VivIngInf/kaffettino-rebrewed/Resources/Images/Buongiornissimi/Christmas/auguri-di-natale-immagini-1.png

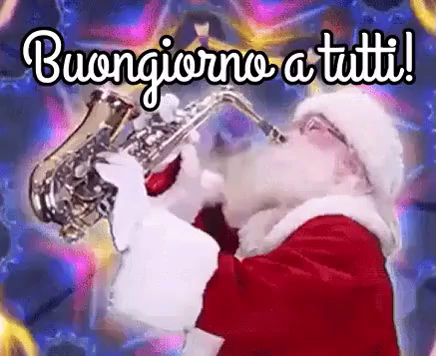
Resources/Images/Buongiornissimi/Christmas/auguri-di-natale-immagini-1.png
