VivIngInf/kaffettino-rebrewed/Resources/Images/Buongiornissimi/Christmas/auguri-di-natale-immagini-11.jpg

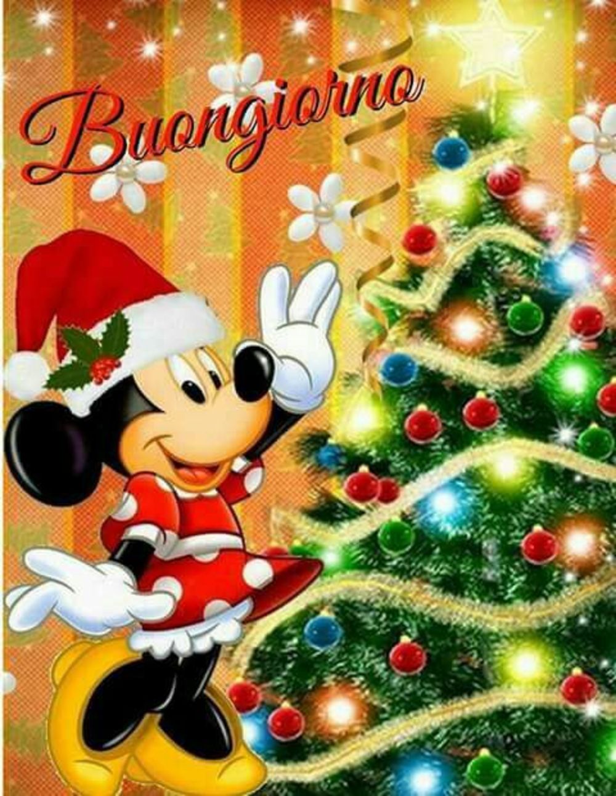
Resources/Images/Buongiornissimi/Christmas/auguri-di-natale-immagini-11.jpg
