VivIngInf/kaffettino-rebrewed/Resources/Images/Buongiornissimi/Christmas/Buongiorno-con-gatto-e-albero-di-Natale.jpg

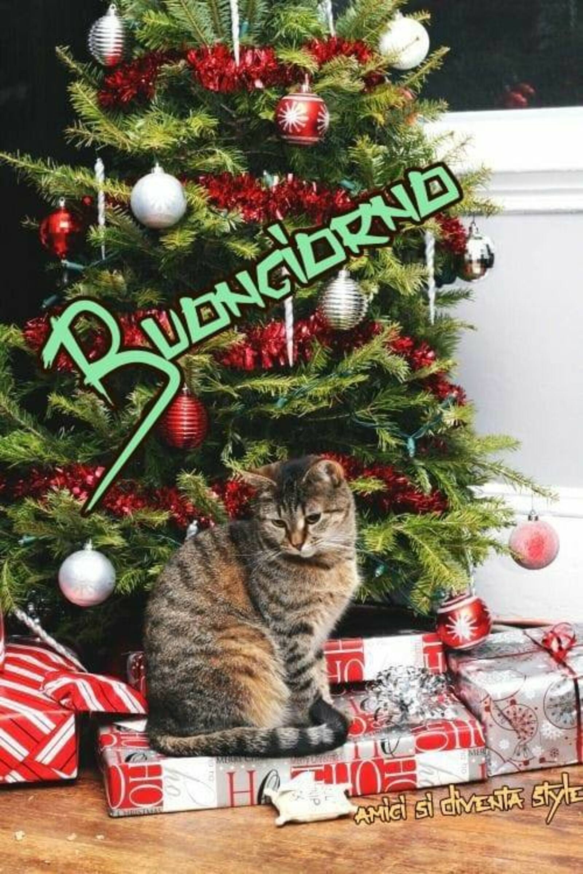
Resources/Images/Buongiornissimi/Christmas/Buongiorno-con-gatto-e-albero-di-Natale.jpg
