VivIngInf/kaffettino-rebrewed/Resources/Images/Buongiornissimi/Christmas/Buongiorno-Natale-1.jpg

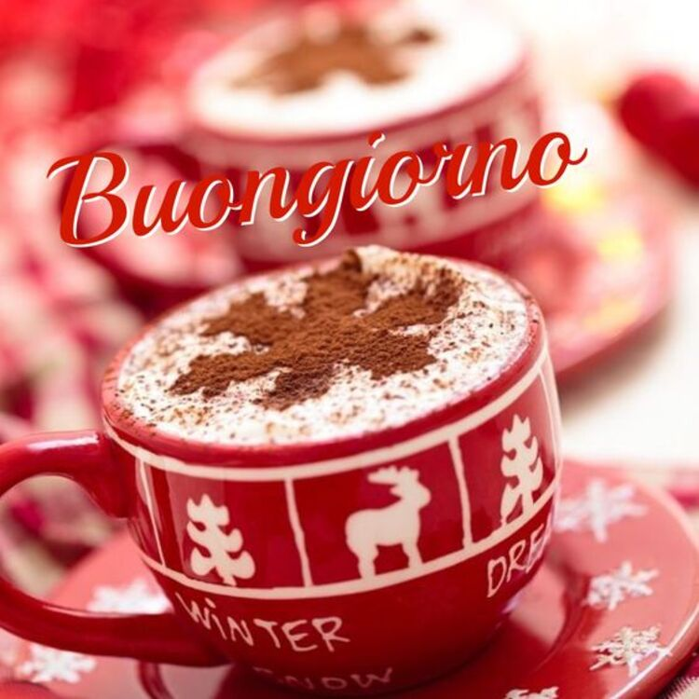
Resources/Images/Buongiornissimi/Christmas/Buongiorno-Natale-1.jpg
