VivIngInf/kaffettino-rebrewed/Resources/Images/Buongiornissimi/Christmas/Buongiorno-natalizio-3-693x1024.jpg

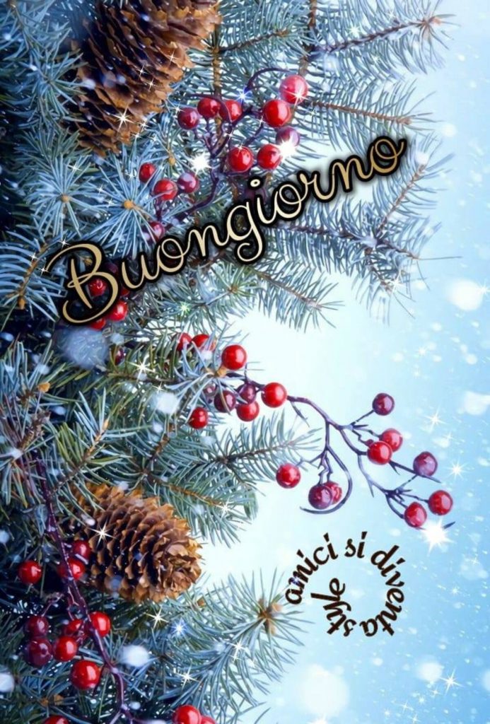
Resources/Images/Buongiornissimi/Christmas/Buongiorno-natalizio-3-693x1024.jpg
