VivIngInf/kaffettino-rebrewed/Resources/Images/Buongiornissimi/Christmas/Buongiorno-natalizio-3.jpg

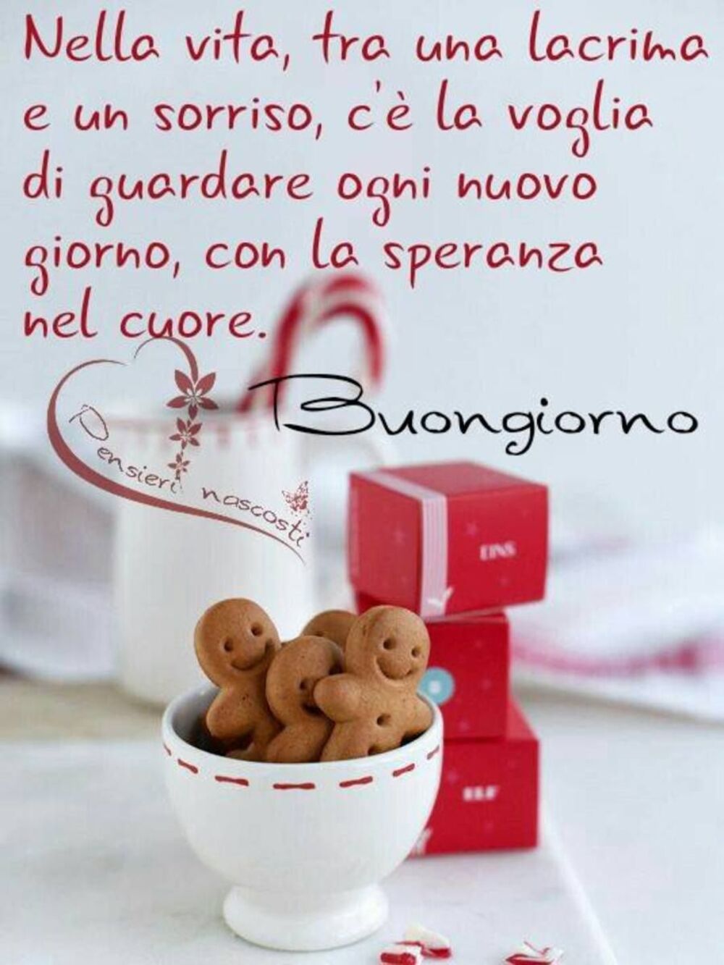
Resources/Images/Buongiornissimi/Christmas/Buongiorno-natalizio-3.jpg
