VivIngInf/kaffettino-rebrewed/Resources/Images/Buongiornissimi/Christmas/Buongiorno-natalizio-8-687x1024.jpg

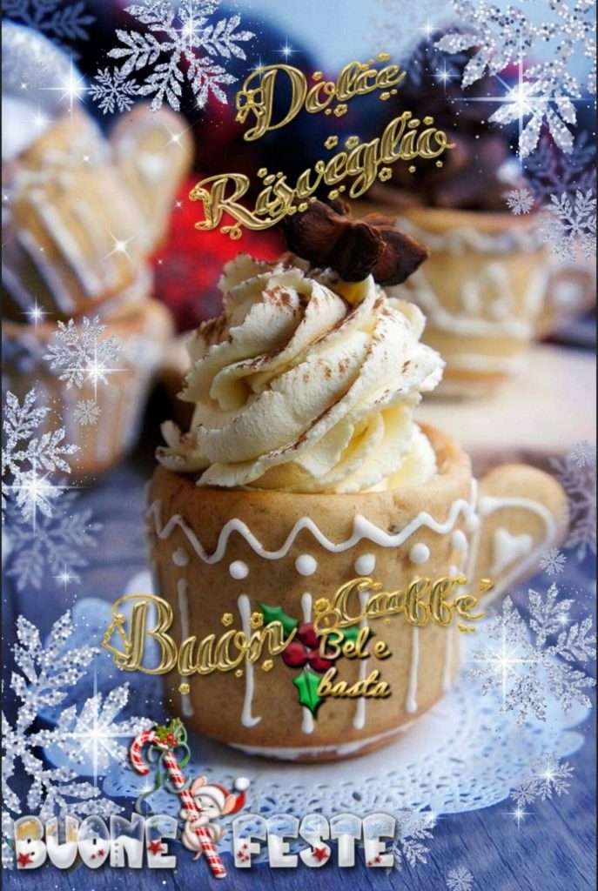
Resources/Images/Buongiornissimi/Christmas/Buongiorno-natalizio-8-687x1024.jpg
