VivIngInf/kaffettino-rebrewed/Resources/Images/Buongiornissimi/Christmas/Buongiorno-natalizio-14-680x1024.jpg

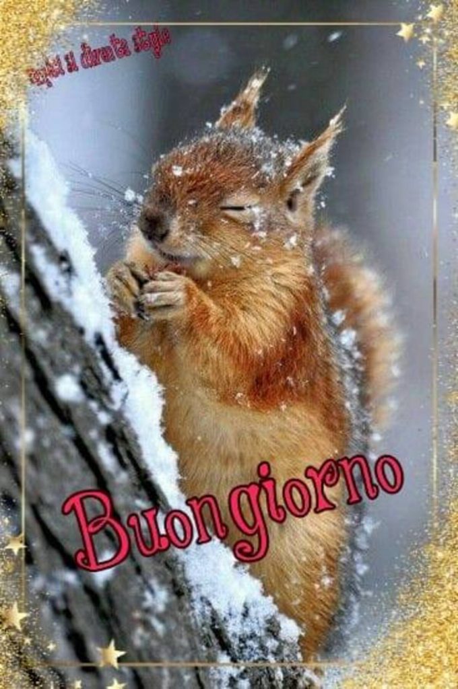
Resources/Images/Buongiornissimi/Christmas/Buongiorno-natalizio-14-680x1024.jpg
