VivIngInf/kaffettino-rebrewed/Resources/Images/Buongiornissimi/Christmas/Buongiorno-natalizio-15-692x1024.jpg

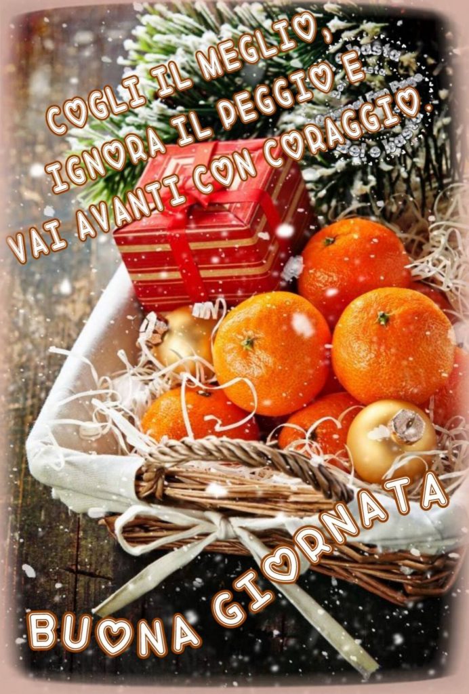
Resources/Images/Buongiornissimi/Christmas/Buongiorno-natalizio-15-692x1024.jpg
