VivIngInf/kaffettino-rebrewed/Resources/Images/Buongiornissimi/Christmas/Buongiorno-natalizio-18-598x1024.jpg

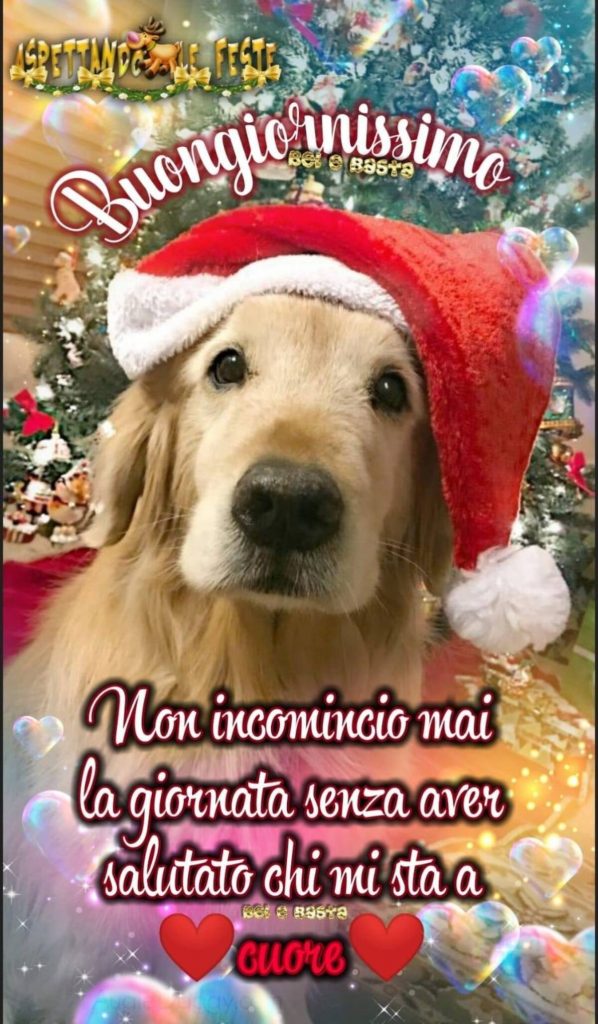
Resources/Images/Buongiornissimi/Christmas/Buongiorno-natalizio-18-598x1024.jpg
