VivIngInf/kaffettino-rebrewed/Resources/Images/Buongiornissimi/Christmas/Buongiorno-natalizio-24-807x1024.jpg

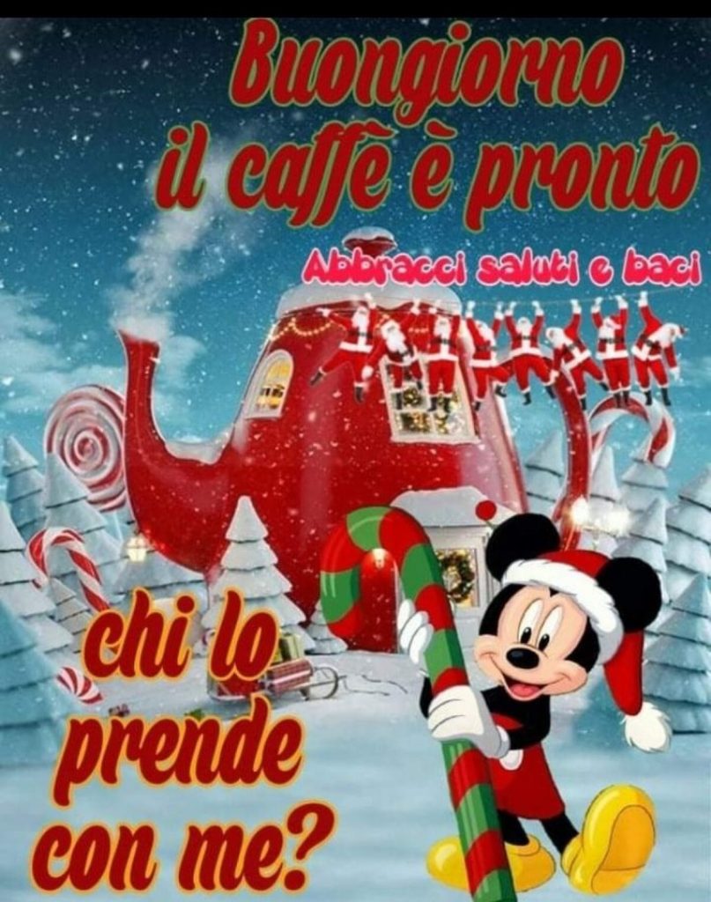
Resources/Images/Buongiornissimi/Christmas/Buongiorno-natalizio-24-807x1024.jpg
