VivIngInf/kaffettino-rebrewed/Resources/Images/Buongiornissimi/Christmas/Buongiorno-natalizio-25-825x1024.jpg

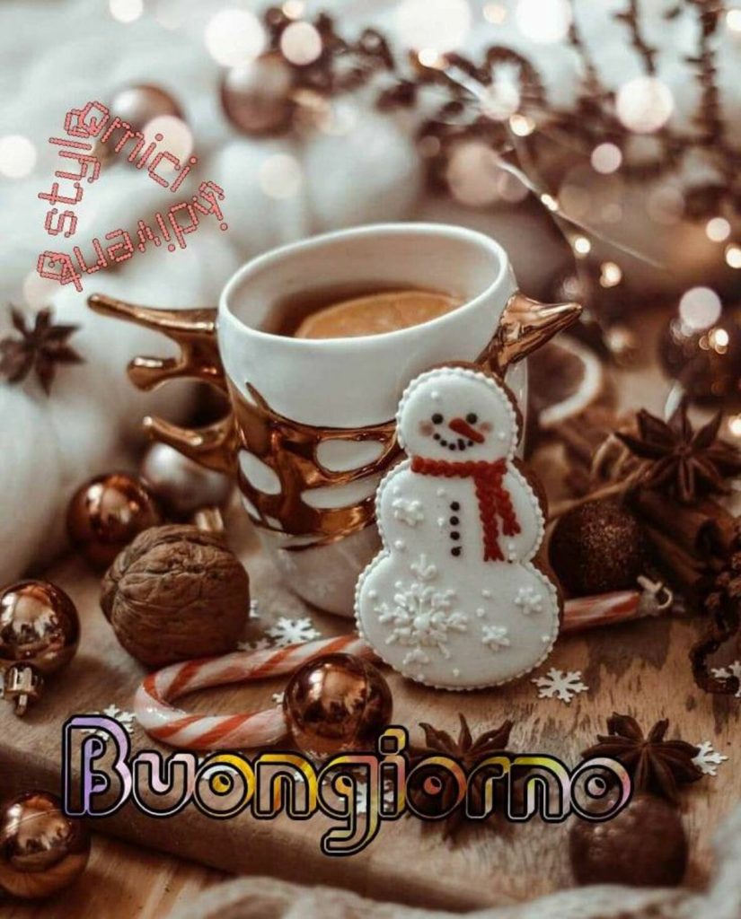
Resources/Images/Buongiornissimi/Christmas/Buongiorno-natalizio-25-825x1024.jpg
