VivIngInf/kaffettino-rebrewed/Resources/Images/Buongiornissimi/Christmas/Buongiorno-natalizio-27-742x1024.jpg

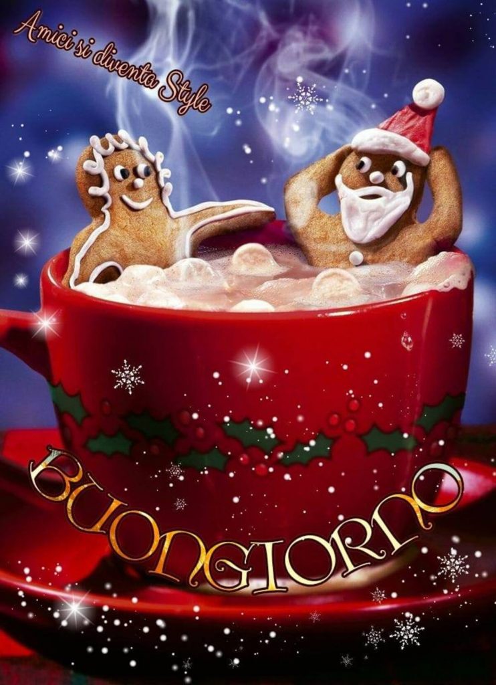
Resources/Images/Buongiornissimi/Christmas/Buongiorno-natalizio-27-742x1024.jpg
