VivIngInf/kaffettino-rebrewed/Resources/Images/Buongiornissimi/Christmas/Buongiorno-natalizio-34-1024x1024.jpg

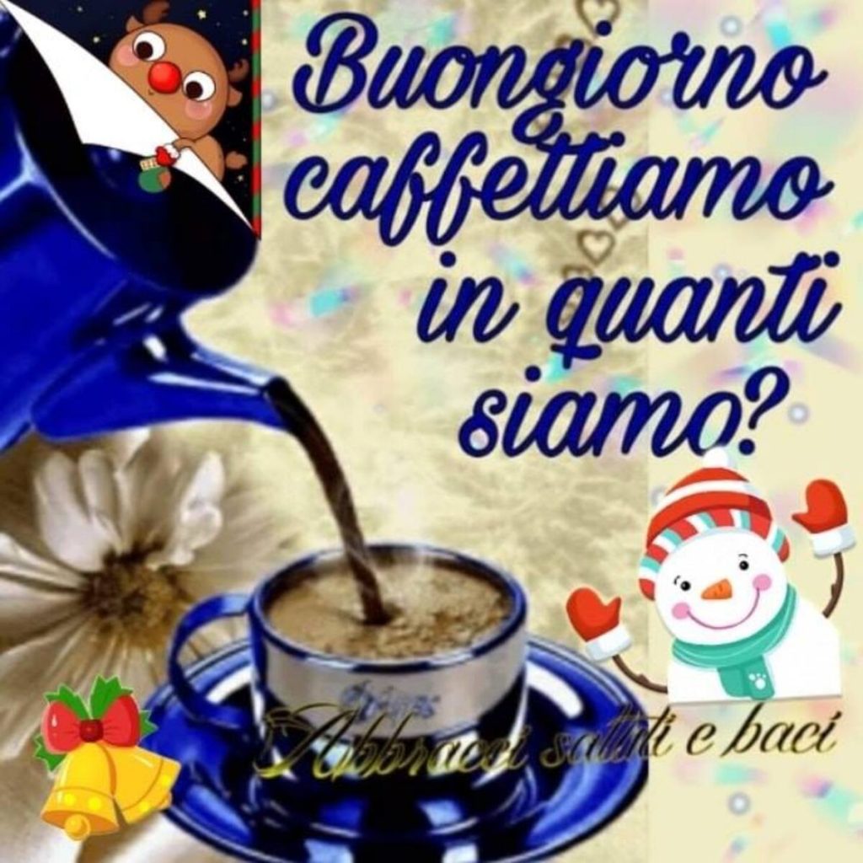
Resources/Images/Buongiornissimi/Christmas/Buongiorno-natalizio-34-1024x1024.jpg
