VivIngInf/kaffettino-rebrewed/Resources/Images/Buongiornissimi/Christmas/Buongiorno-natalizio-37-1024x683.jpg

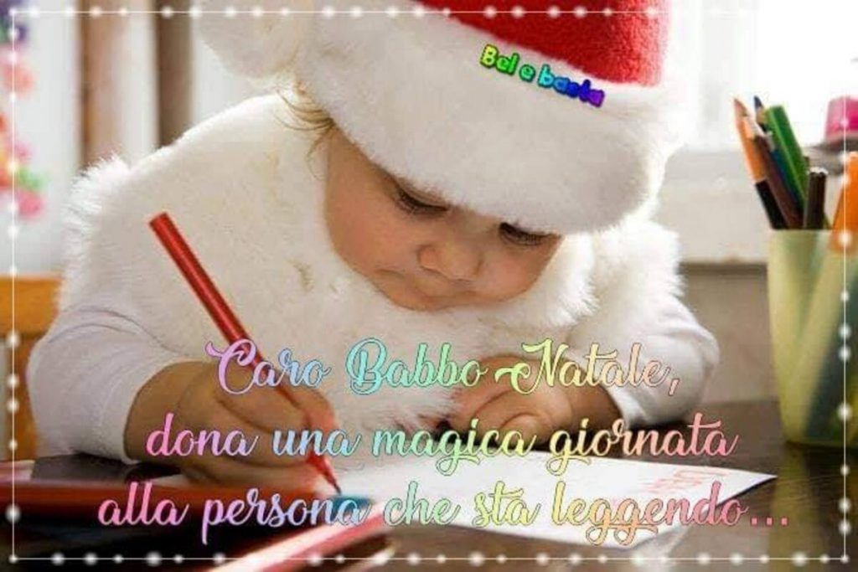
Resources/Images/Buongiornissimi/Christmas/Buongiorno-natalizio-37-1024x683.jpg
