VivIngInf/kaffettino-rebrewed/Resources/Images/Buongiornissimi/Christmas/Buongiorno-natalizio-38-1024x1024.jpg

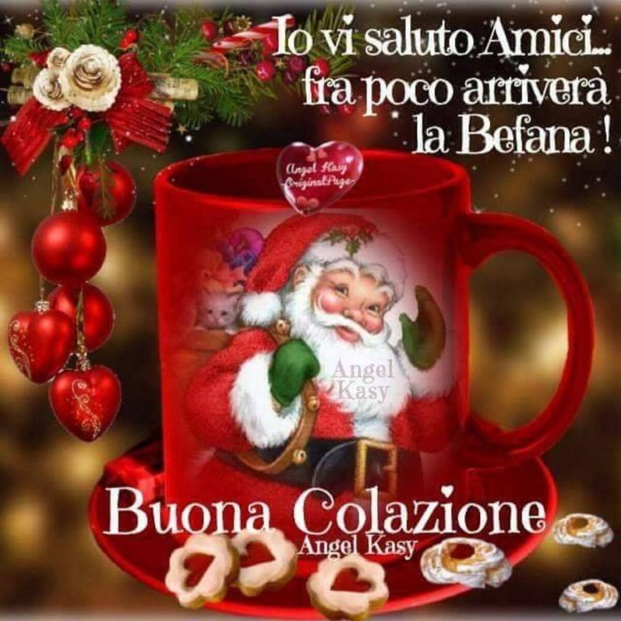
Resources/Images/Buongiornissimi/Christmas/Buongiorno-natalizio-38-1024x1024.jpg
