VivIngInf/kaffettino-rebrewed/Resources/Images/Buongiornissimi/Christmas/Buongiorno-natalizio-43-840x1024.jpg

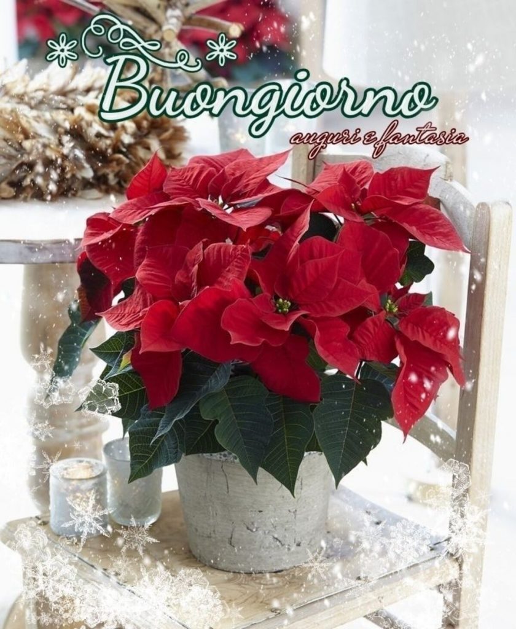
Resources/Images/Buongiornissimi/Christmas/Buongiorno-natalizio-43-840x1024.jpg
