VivIngInf/kaffettino-rebrewed/Resources/Images/Buongiornissimi/Christmas/Buongiorno-natalizio-44-1024x794.jpg

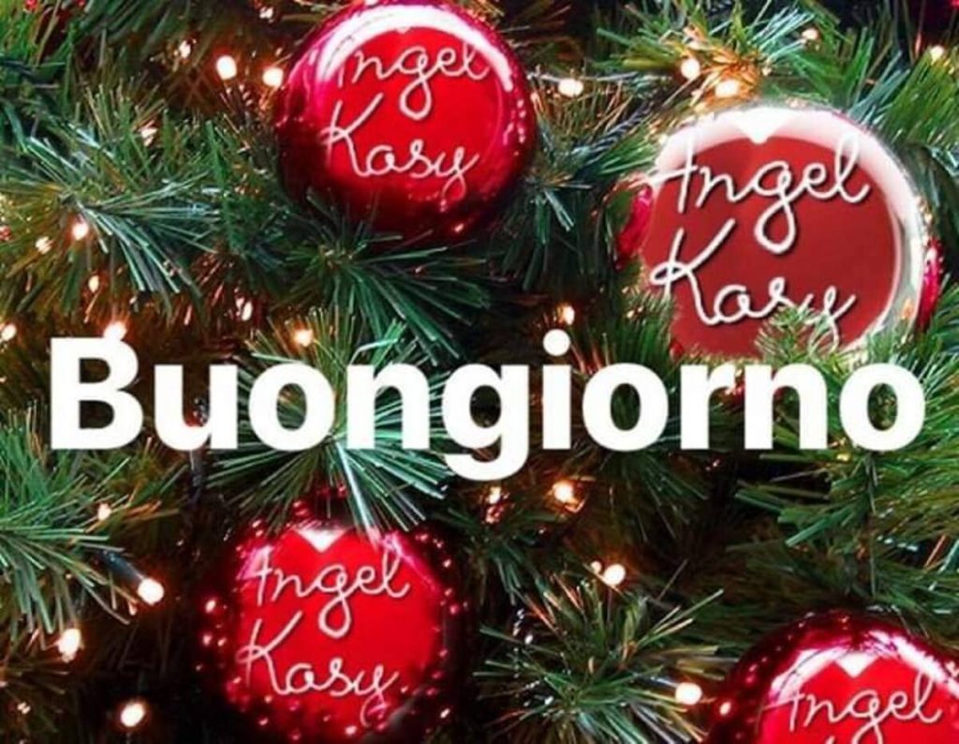
Resources/Images/Buongiornissimi/Christmas/Buongiorno-natalizio-44-1024x794.jpg
