VivIngInf/kaffettino-rebrewed/Resources/Images/Buongiornissimi/Christmas/Buongiorno-natalizio-belle-immagini-1.jpg

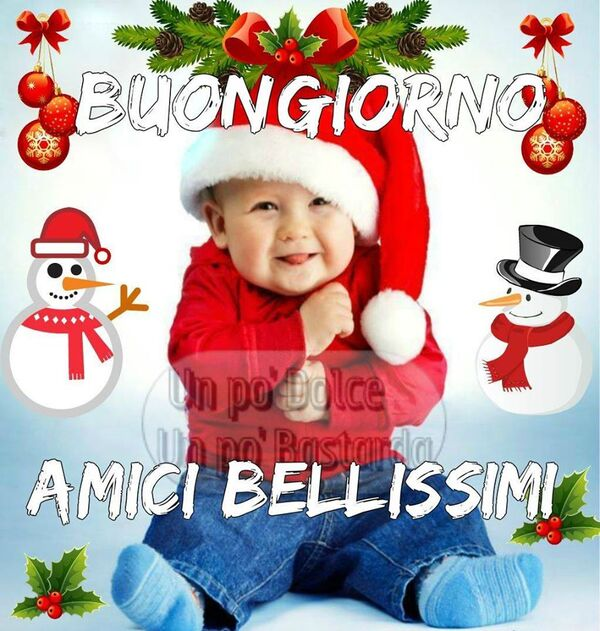
Resources/Images/Buongiornissimi/Christmas/Buongiorno-natalizio-belle-immagini-1.jpg
