VivIngInf/kaffettino-rebrewed/Resources/Images/Buongiornissimi/Christmas/Buongiorno-natalizio-belle-immagini-7.jpg

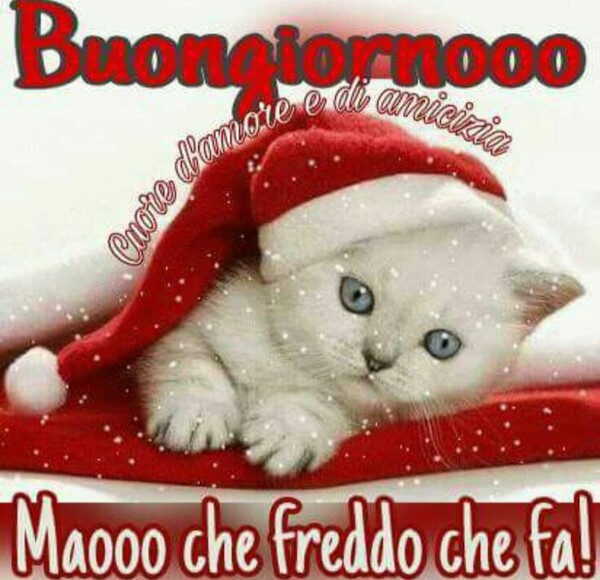
Resources/Images/Buongiornissimi/Christmas/Buongiorno-natalizio-belle-immagini-7.jpg
