VivIngInf/kaffettino-rebrewed/Resources/Images/Buongiornissimi/Christmas/Buongiorno-natalizio-belle-immagini-13.jpg

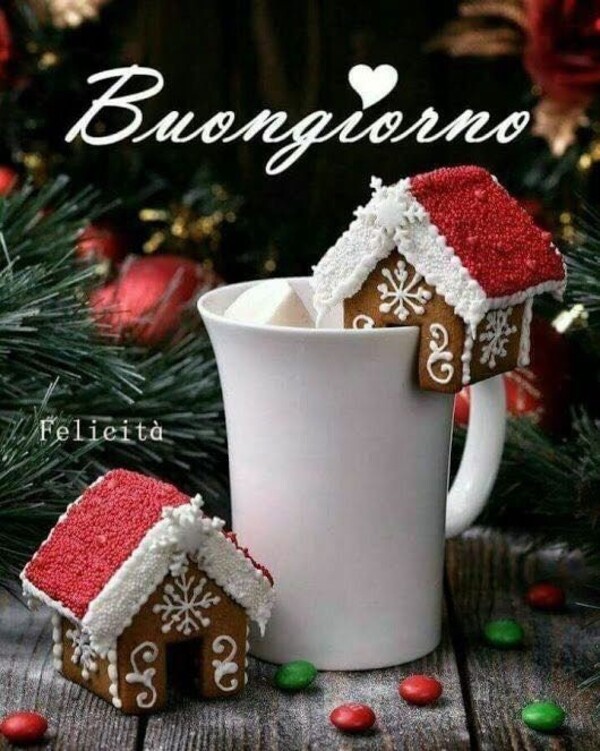
Resources/Images/Buongiornissimi/Christmas/Buongiorno-natalizio-belle-immagini-13.jpg
