VivIngInf/kaffettino-rebrewed/Resources/Images/Buongiornissimi/Christmas/Buongiorno-natalizio-belle-immagini-15.jpg

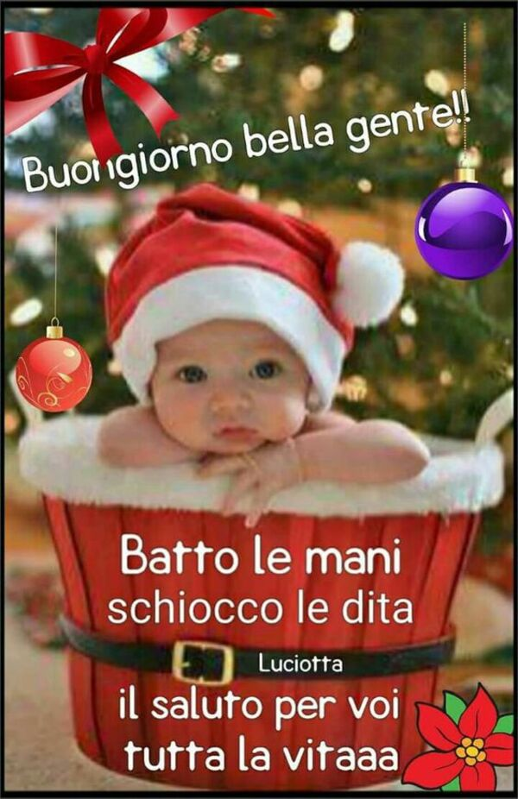
Resources/Images/Buongiornissimi/Christmas/Buongiorno-natalizio-belle-immagini-15.jpg
