VivIngInf/kaffettino-rebrewed/Resources/Images/Buongiornissimi/Christmas/Buongiorno-natalizio-link-nuovi-5.jpg

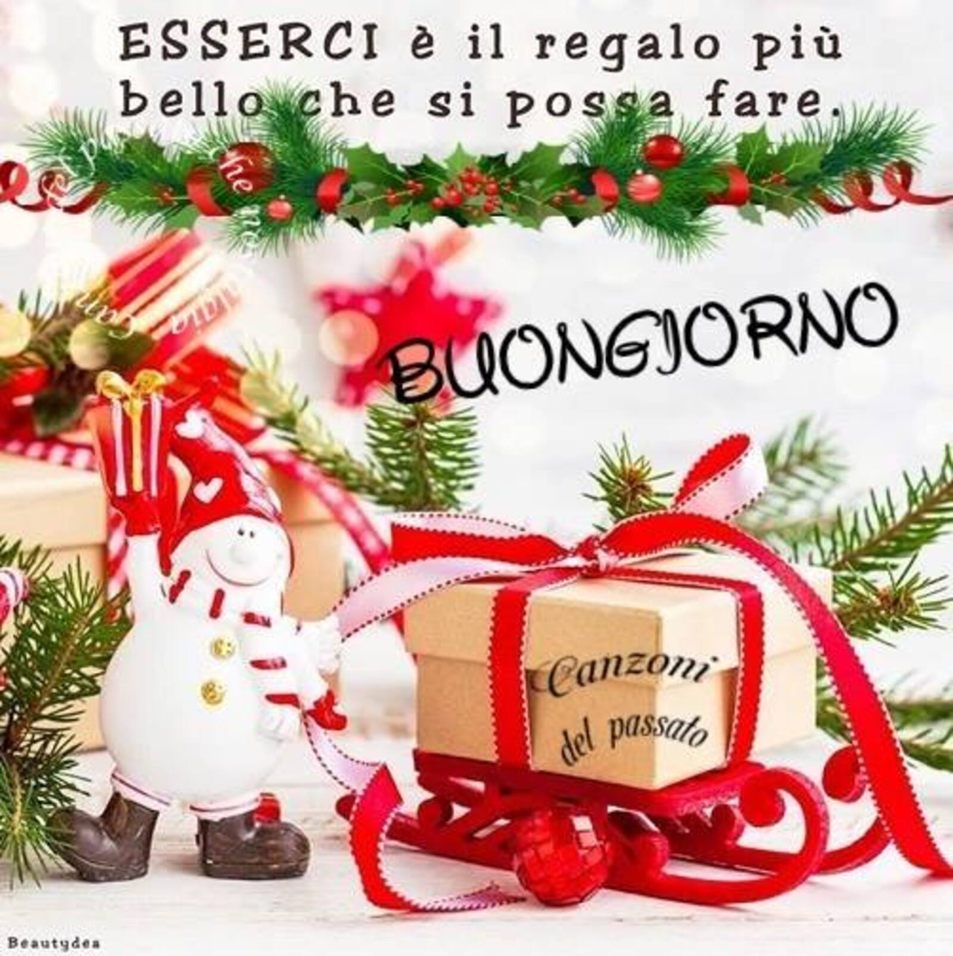
Resources/Images/Buongiornissimi/Christmas/Buongiorno-natalizio-link-nuovi-5.jpg
