VivIngInf/kaffettino-rebrewed/Resources/Images/Buongiornissimi/Christmas/Buongiorno-per-il-Natale-1-860x1024.jpg

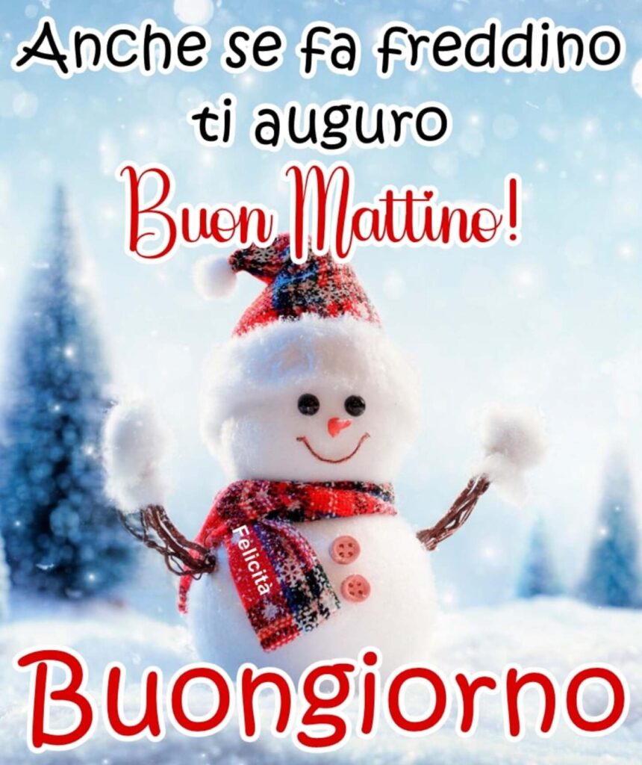
Resources/Images/Buongiornissimi/Christmas/Buongiorno-per-il-Natale-1-860x1024.jpg
