VivIngInf/kaffettino-rebrewed/Resources/Images/Buongiornissimi/Christmas/Buongiorno-per-il-Natale-3-808x1024.jpg

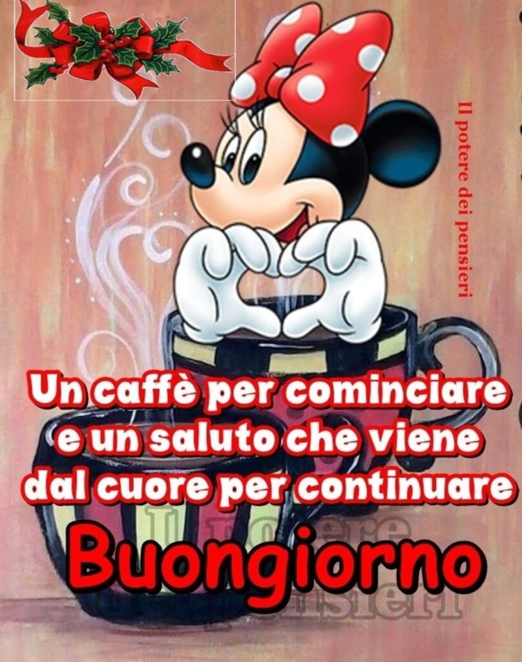
Resources/Images/Buongiornissimi/Christmas/Buongiorno-per-il-Natale-3-808x1024.jpg
