VivIngInf/kaffettino-rebrewed/Resources/Images/Buongiornissimi/Christmas/Buongiorno-per-il-Natale-6-769x1024.jpg

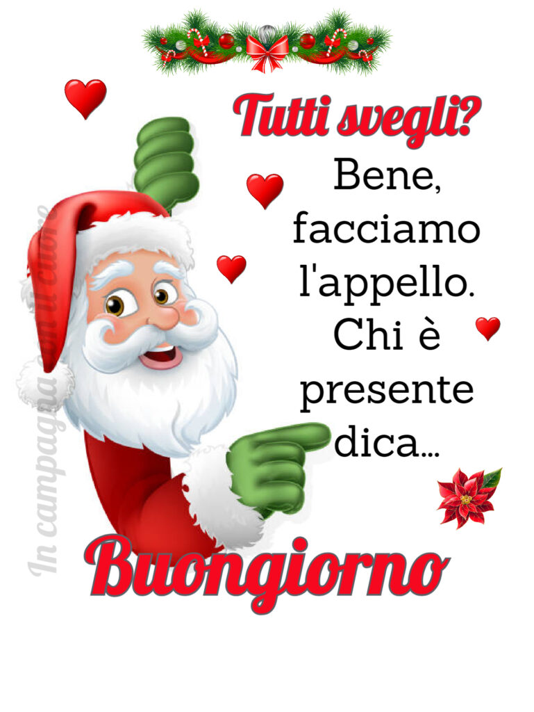
Resources/Images/Buongiornissimi/Christmas/Buongiorno-per-il-Natale-6-769x1024.jpg
