VivIngInf/kaffettino-rebrewed/Resources/Images/Buongiornissimi/Christmas/Buongiorno-per-il-Natale-8-858x1024.jpg

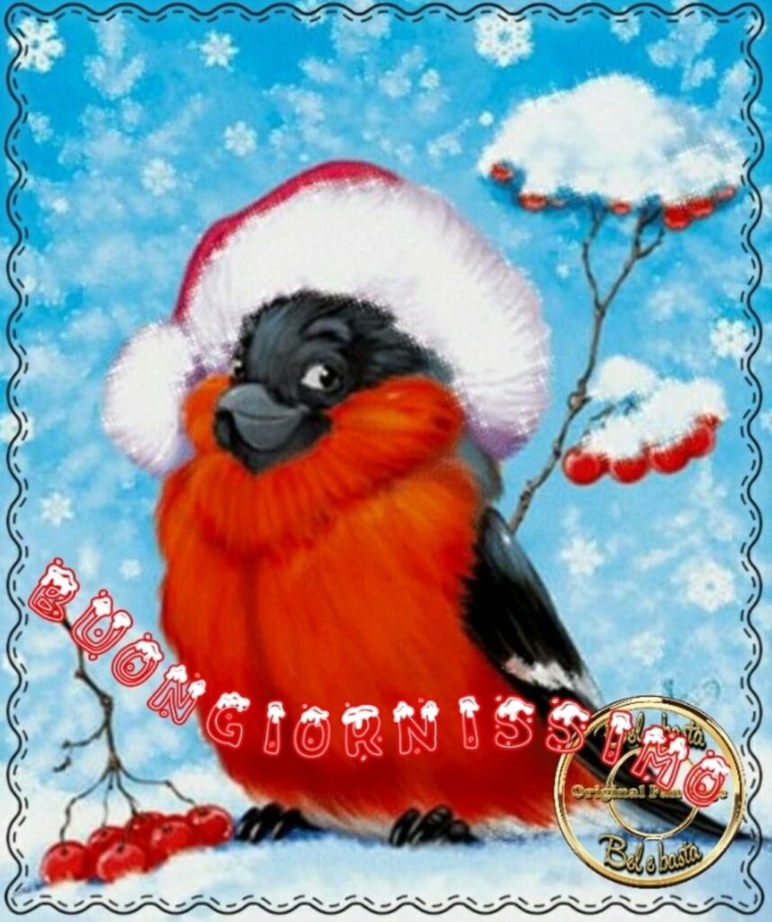
Resources/Images/Buongiornissimi/Christmas/Buongiorno-per-il-Natale-8-858x1024.jpg
