VivIngInf/kaffettino-rebrewed/Resources/Images/Buongiornissimi/Christmas/Buongiorno-per-il-Natale-11-773x1024.jpg

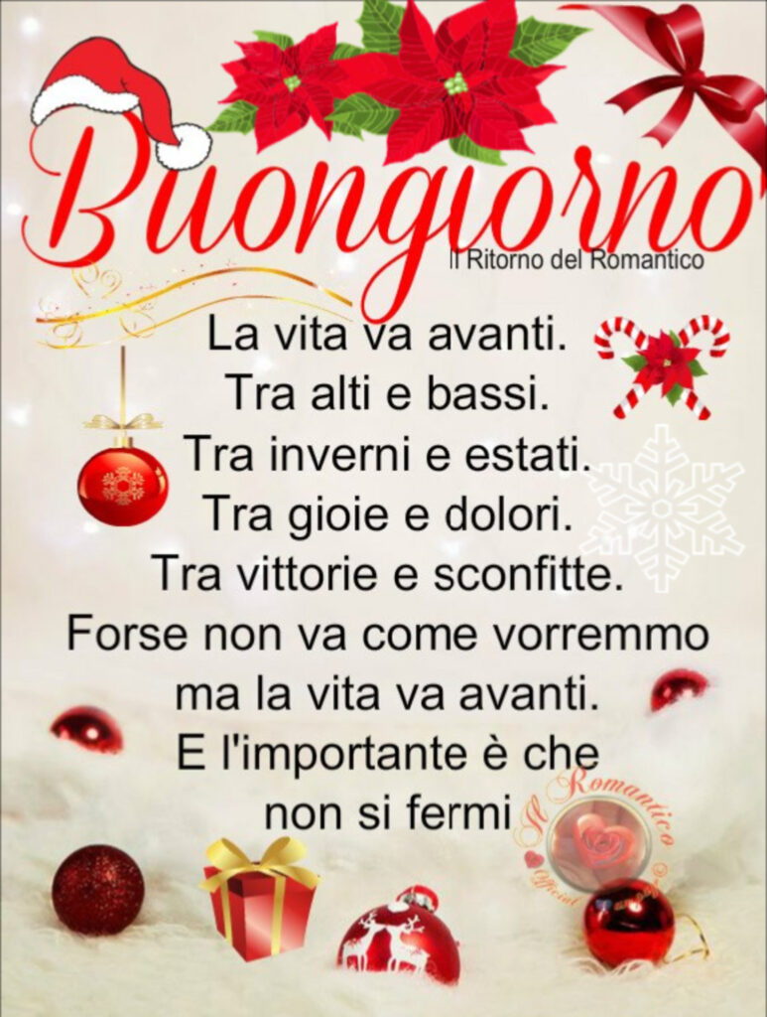
Resources/Images/Buongiornissimi/Christmas/Buongiorno-per-il-Natale-11-773x1024.jpg
