VivIngInf/kaffettino-rebrewed/Resources/Images/Buongiornissimi/Christmas/d4e82814d92ebad9347e3b47b032a1e5.jpg

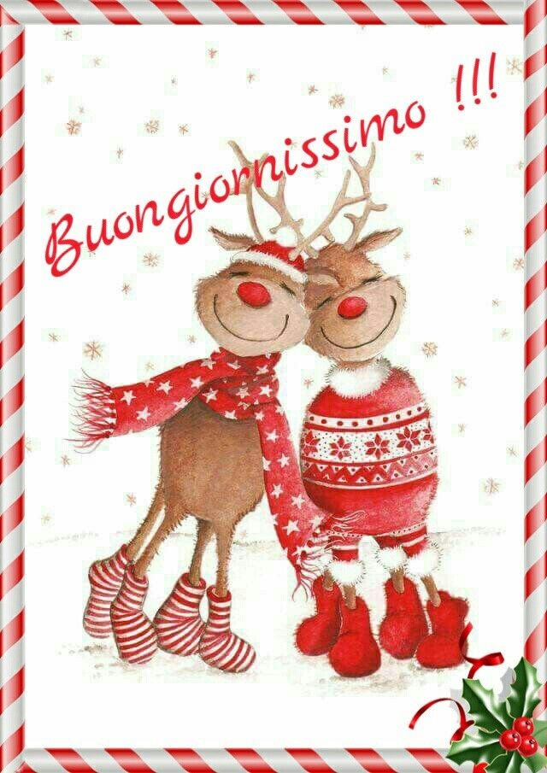
Resources/Images/Buongiornissimi/Christmas/d4e82814d92ebad9347e3b47b032a1e5.jpg
