VivIngInf/kaffettino-rebrewed/Resources/Images/Buongiornissimi/Christmas/d062dc0604afb666024305d2ea12398f.jpg

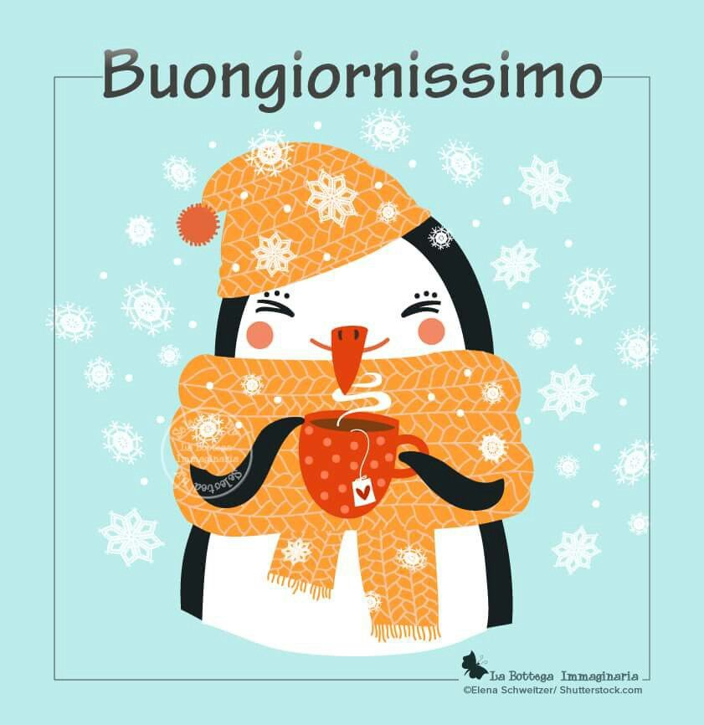
Resources/Images/Buongiornissimi/Christmas/d062dc0604afb666024305d2ea12398f.jpg
