VivIngInf/kaffettino-rebrewed/Resources/Images/Buongiornissimi/Christmas/IMG-20181119-WA0004.jpg

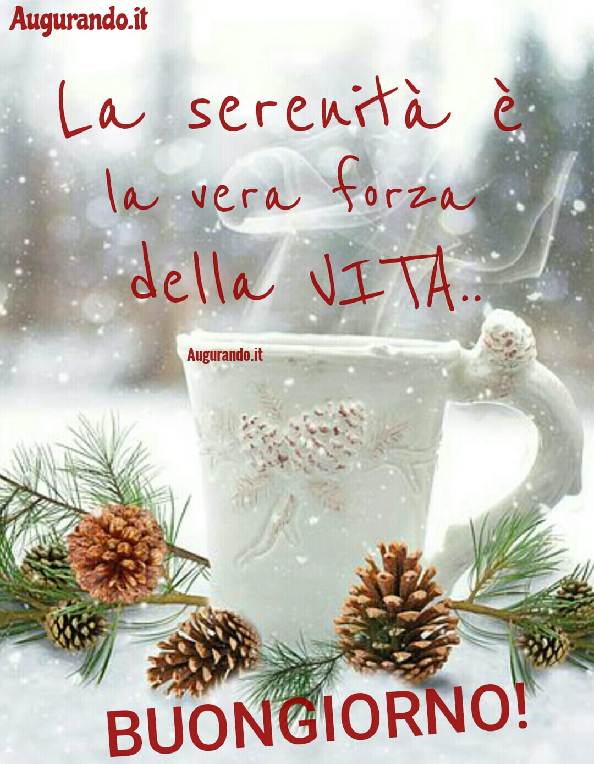
Resources/Images/Buongiornissimi/Christmas/IMG-20181119-WA0004.jpg
