VivIngInf/kaffettino-rebrewed/Resources/Images/Buongiornissimi/Debt/Bed.jpg

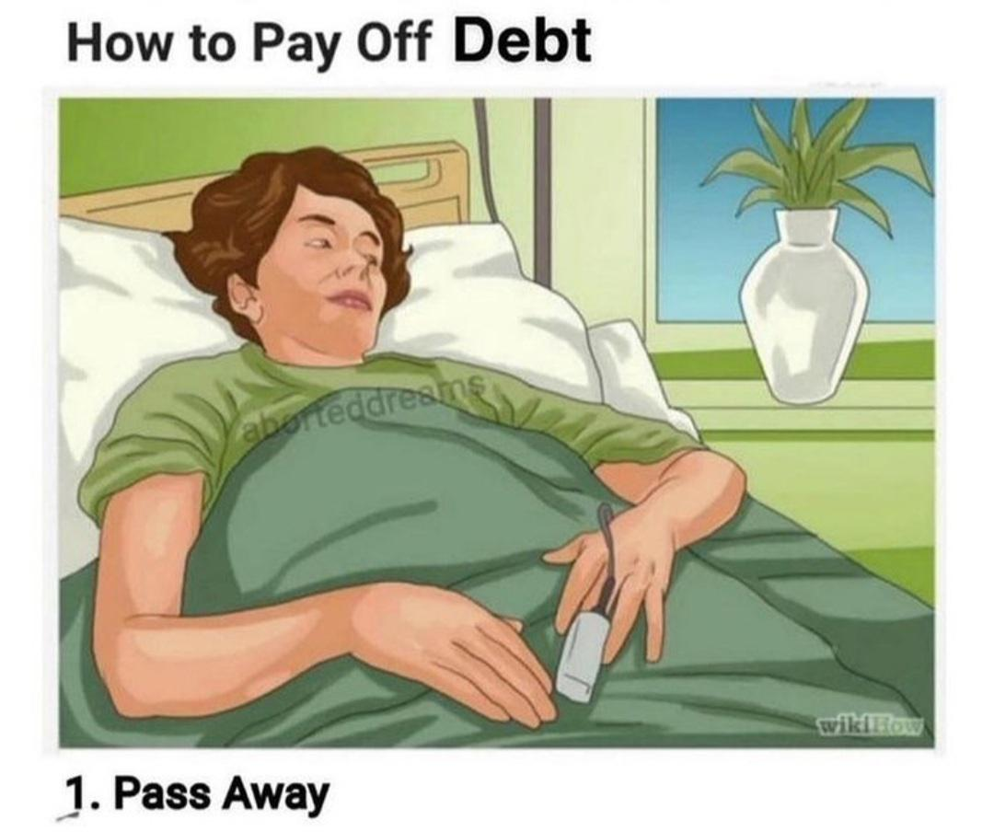
Resources/Images/Buongiornissimi/Debt/Bed.jpg
