VivIngInf/kaffettino-rebrewed/Resources/Images/Buongiornissimi/Debt/Crying.jpg

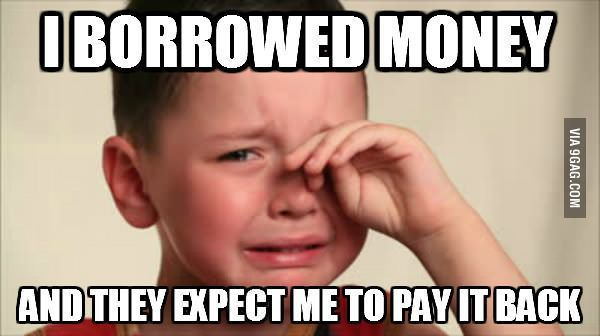
Resources/Images/Buongiornissimi/Debt/Crying.jpg
