VivIngInf/kaffettino-rebrewed/Resources/Images/Buongiornissimi/Debt/Dog.webp

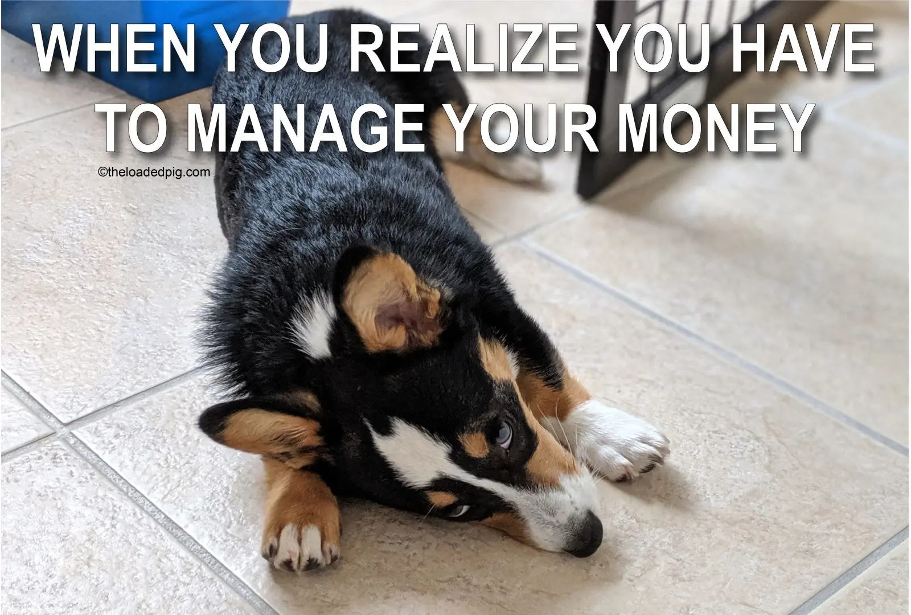
Resources/Images/Buongiornissimi/Debt/Dog.webp
