VivIngInf/kaffettino-rebrewed/Resources/Images/Buongiornissimi/Debt/Excursion.jpg

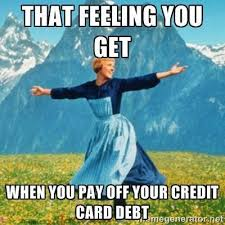
Resources/Images/Buongiornissimi/Debt/Excursion.jpg
