VivIngInf/kaffettino-rebrewed/Resources/Images/Buongiornissimi/Debt/Jump.jpg

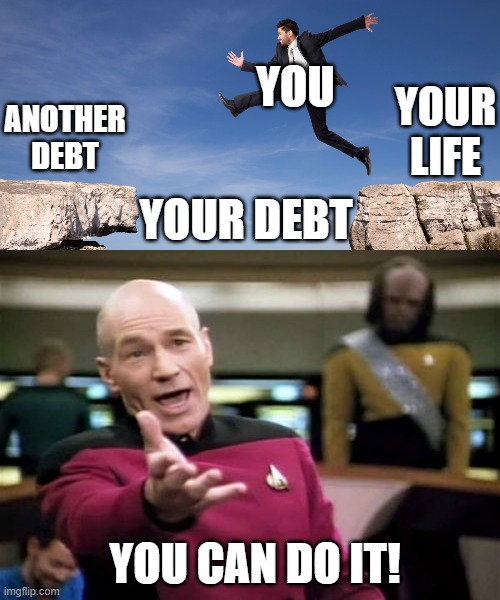
Resources/Images/Buongiornissimi/Debt/Jump.jpg
