VivIngInf/kaffettino-rebrewed/Resources/Images/Buongiornissimi/Debt/Peter.webp

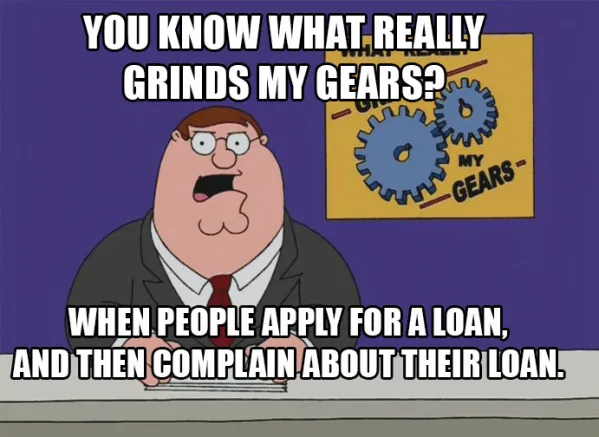
Resources/Images/Buongiornissimi/Debt/Peter.webp
