VivIngInf/kaffettino-rebrewed/Resources/Images/Buongiornissimi/Debt/Swimming.jpg

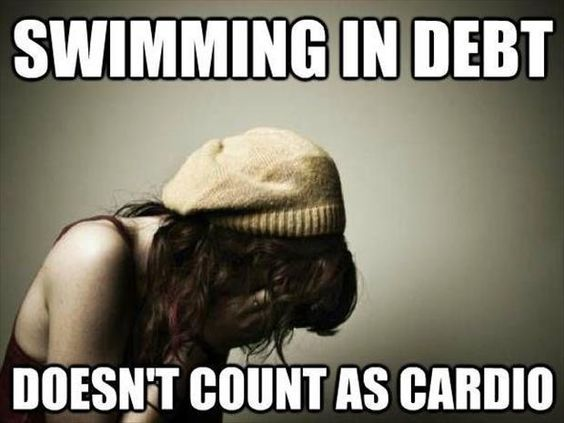
Resources/Images/Buongiornissimi/Debt/Swimming.jpg
