VivIngInf/kaffettino-rebrewed/Resources/Images/Buongiornissimi/Debt/Wallet.jpg

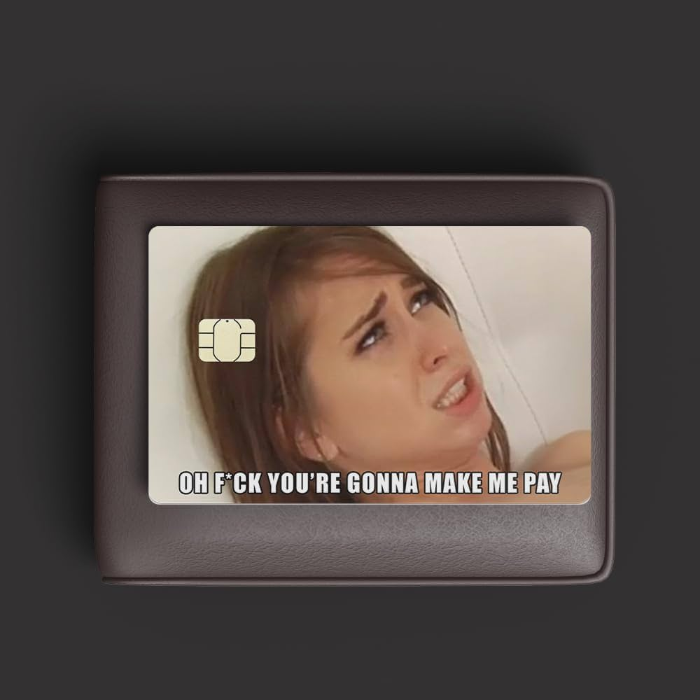
Resources/Images/Buongiornissimi/Debt/Wallet.jpg
