VivIngInf/kaffettino-rebrewed/Resources/Images/Buongiornissimi/Easter/8abb78aae9db7de9b1623d1325ee7758.jpg

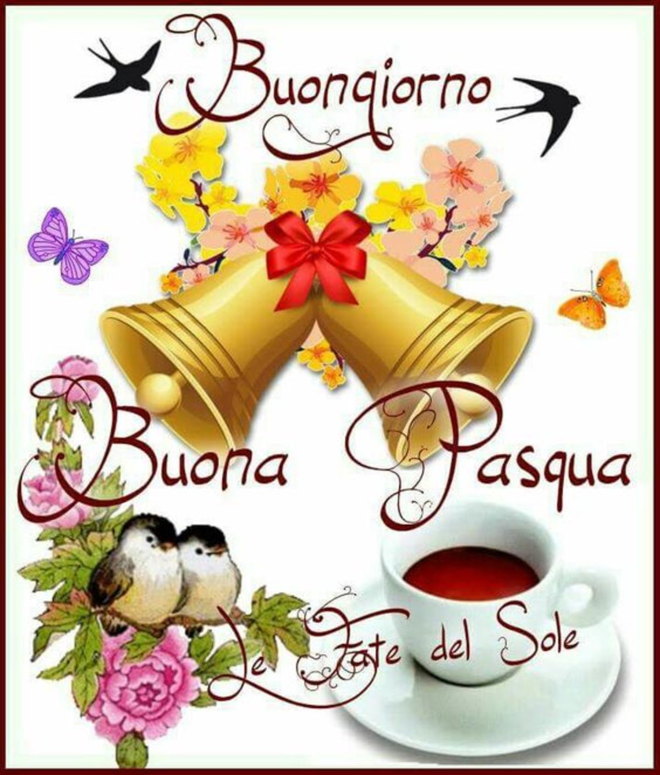
Resources/Images/Buongiornissimi/Easter/8abb78aae9db7de9b1623d1325ee7758.jpg
