VivIngInf/kaffettino-rebrewed/Resources/Images/Buongiornissimi/Easter/Buona-Pasqua-buongiorno-immagini-8727.jpg

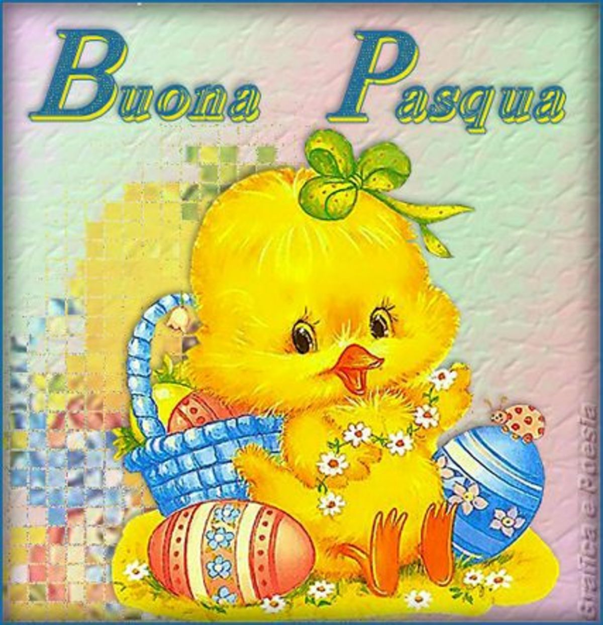
Resources/Images/Buongiornissimi/Easter/Buona-Pasqua-buongiorno-immagini-8727.jpg
