VivIngInf/kaffettino-rebrewed/Resources/Images/Buongiornissimi/Easter/buona-pasqua-con-uova-e-coniglietto.jpg

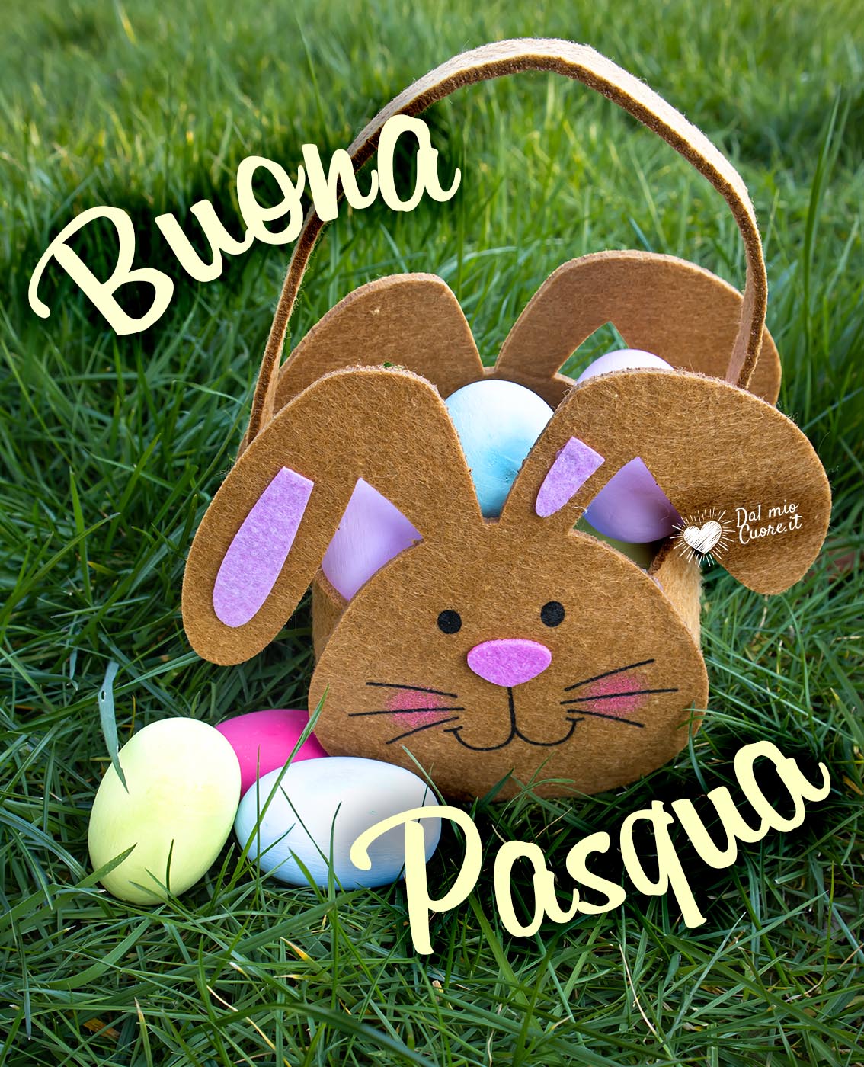
Resources/Images/Buongiornissimi/Easter/buona-pasqua-con-uova-e-coniglietto.jpg
