VivIngInf/kaffettino-rebrewed/Resources/Images/Buongiornissimi/Easter/campane-pasqua.jpg

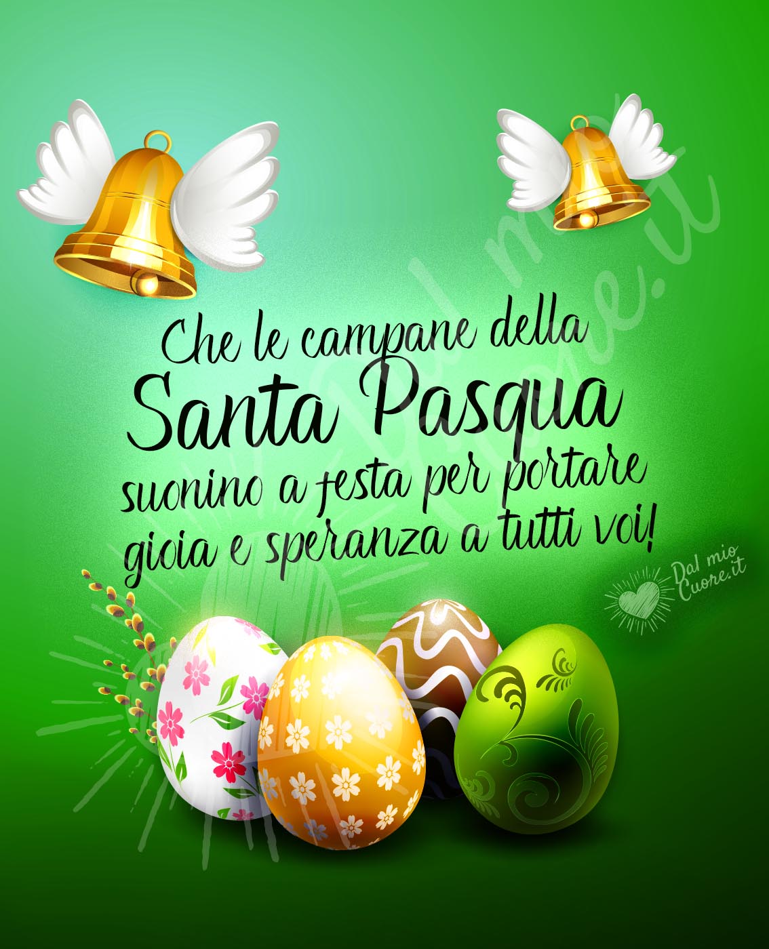
Resources/Images/Buongiornissimi/Easter/campane-pasqua.jpg
