VivIngInf/kaffettino-rebrewed/Resources/Images/Buongiornissimi/Easter/Immagine WhatsApp 2024-03-31 ore 10.33.46_9a69b27c.jpg

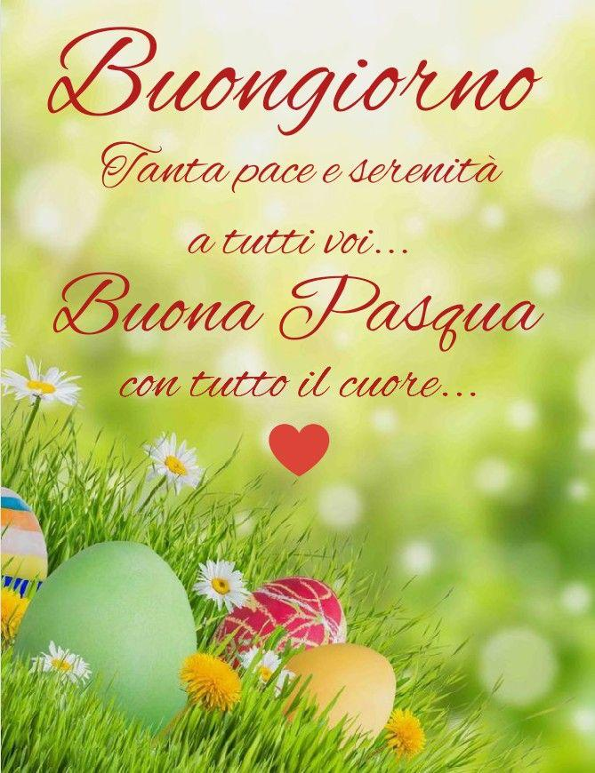
Resources/Images/Buongiornissimi/Easter/Immagine WhatsApp 2024-03-31 ore 10.33.46_9a69b27c.jpg
