VivIngInf/kaffettino-rebrewed/Resources/Images/Buongiornissimi/Easter/Immagine WhatsApp 2024-03-31 ore 10.36.33_8d8238a4.jpg

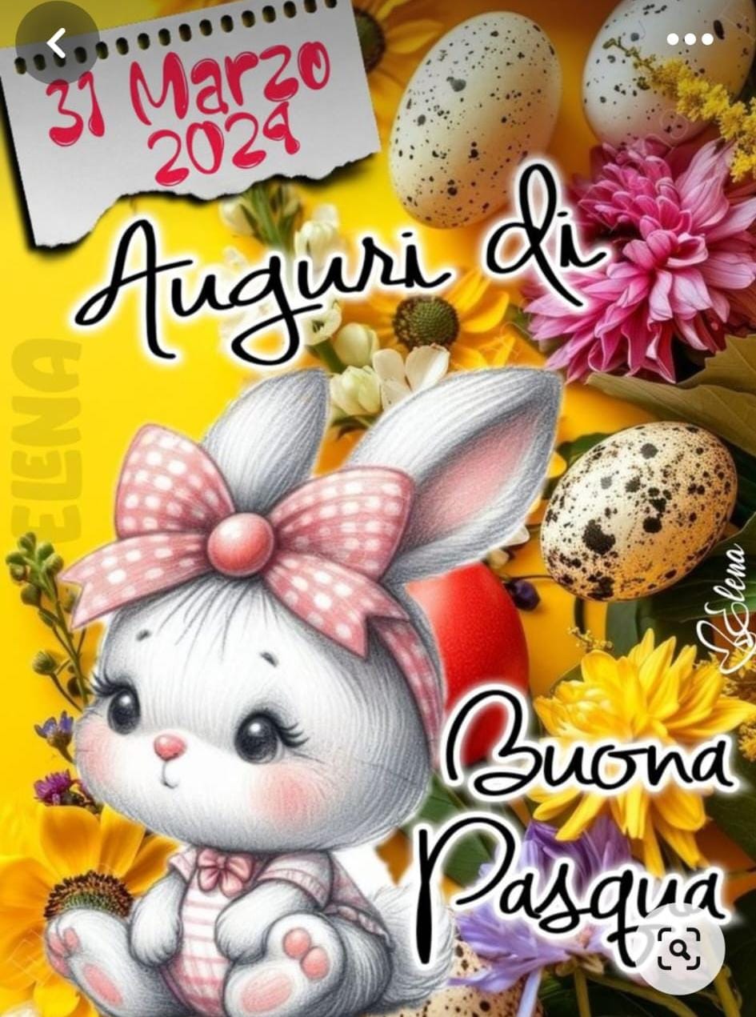
Resources/Images/Buongiornissimi/Easter/Immagine WhatsApp 2024-03-31 ore 10.36.33_8d8238a4.jpg
