VivIngInf/kaffettino-rebrewed/Resources/Images/Buongiornissimi/Easter/immagine_04-13-03.24.48.jpg

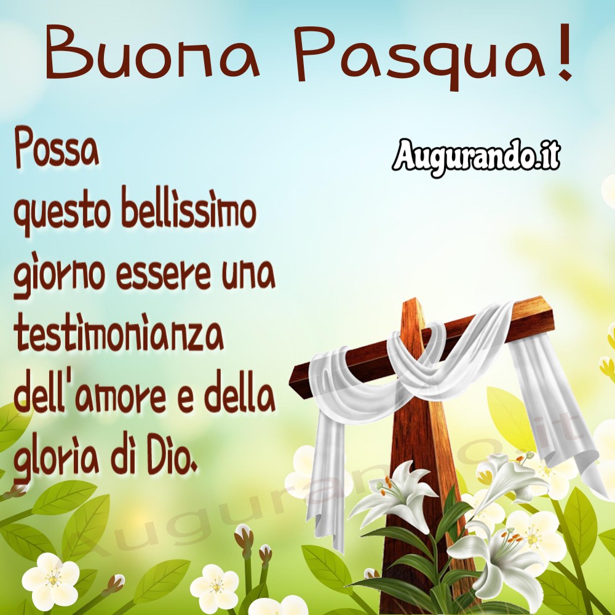
Resources/Images/Buongiornissimi/Easter/immagine_04-13-03.24.48.jpg
