VivIngInf/kaffettino-rebrewed/Resources/Images/Buongiornissimi/Easter/Immagini-buongiorno-carina-buon-giorno-a-tutti-voi-nuove-foto-e-illustrazioni-2023-belle-e-gratis-per-WhatsApp-e-Facebook-1682-1200x1200.jpg

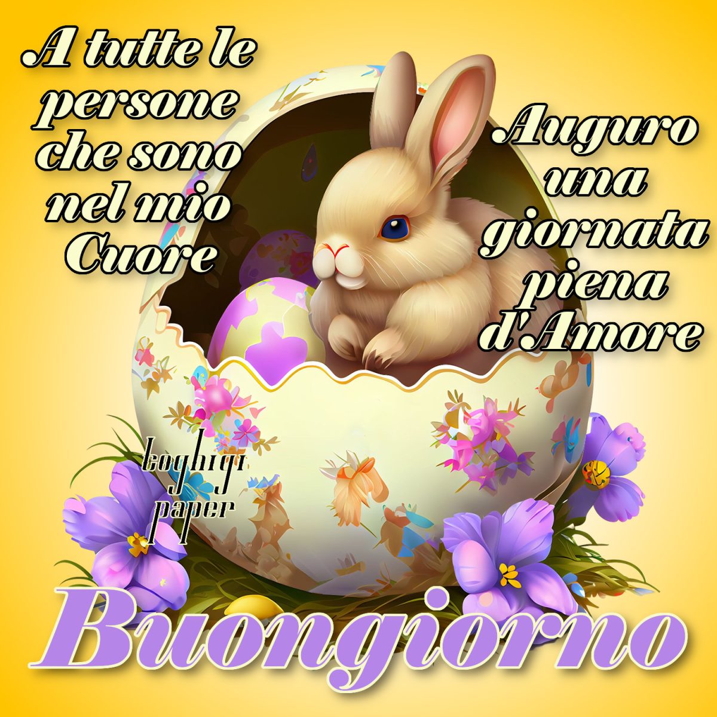
Resources/Images/Buongiornissimi/Easter/Immagini-buongiorno-carina-buon-giorno-a-tutti-voi-nuove-foto-e-illustrazioni-2023-belle-e-gratis-per-WhatsApp-e-Facebook-1682-1200x1200.jpg
