VivIngInf/kaffettino-rebrewed/Resources/Images/Buongiornissimi/Friday/4f488a0c-9a6c-42d8-9248-403378ce7738.webp

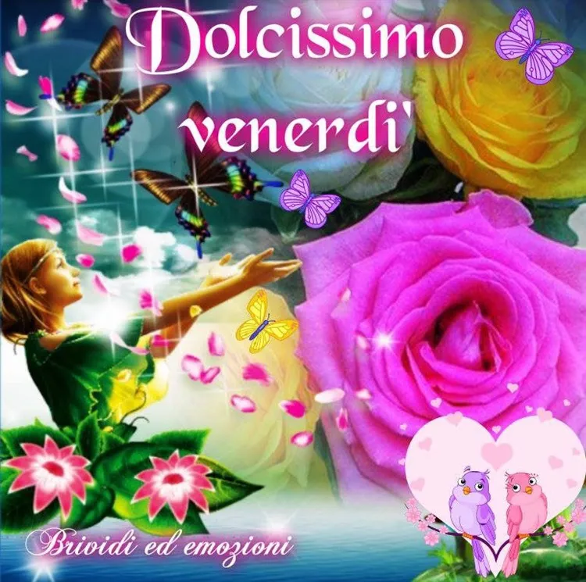
Resources/Images/Buongiornissimi/Friday/4f488a0c-9a6c-42d8-9248-403378ce7738.webp
