VivIngInf/kaffettino-rebrewed/Resources/Images/Buongiornissimi/Friday/9ca3b033-6efd-4079-9b4c-2d049fb06968.webp

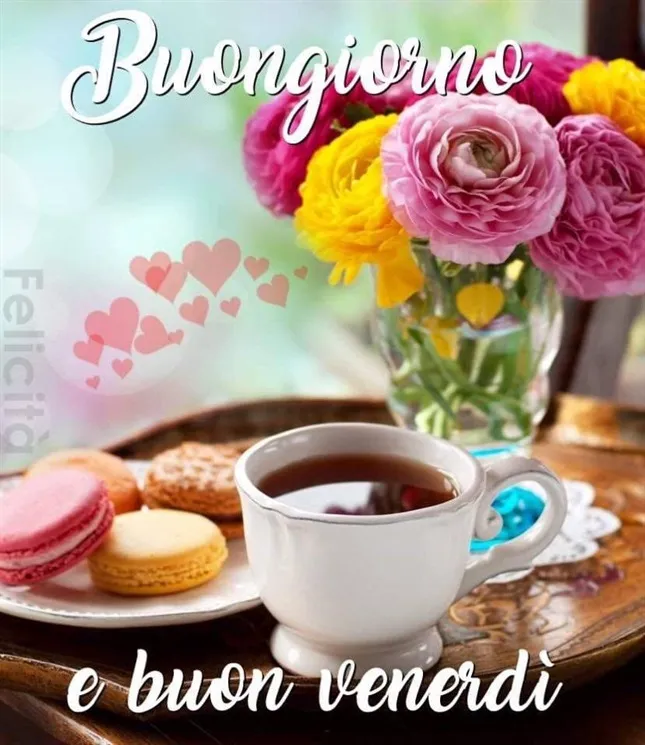
Resources/Images/Buongiornissimi/Friday/9ca3b033-6efd-4079-9b4c-2d049fb06968.webp
