VivIngInf/kaffettino-rebrewed/Resources/Images/Buongiornissimi/Friday/f532cb81-6a29-4cc0-b30d-aa58d23269c9.webp

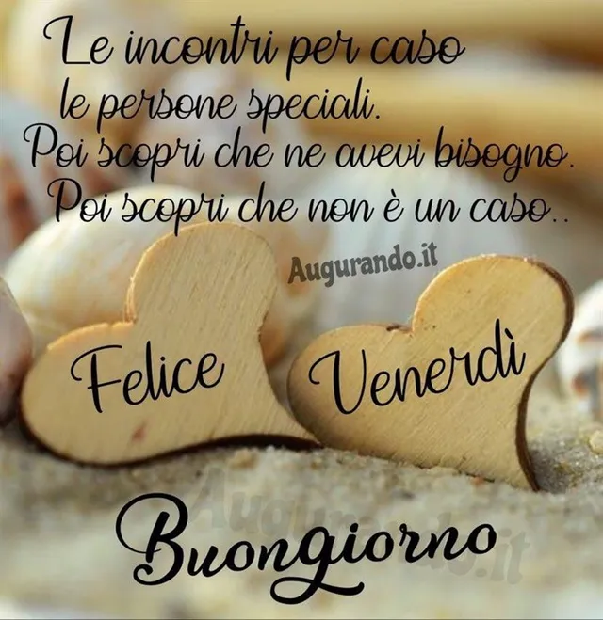
Resources/Images/Buongiornissimi/Friday/f532cb81-6a29-4cc0-b30d-aa58d23269c9.webp
