VivIngInf/kaffettino-rebrewed/Resources/Images/Buongiornissimi/Generic/0cd03b4f-e176-4b3a-ba63-b01ec4a9e170.webp

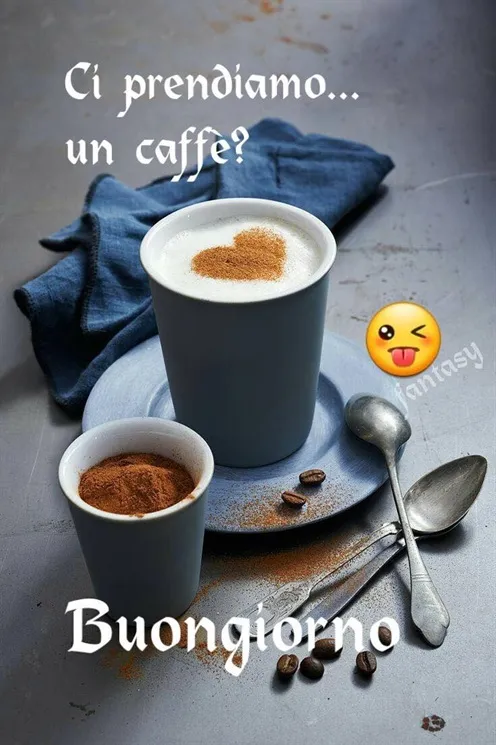
Resources/Images/Buongiornissimi/Generic/0cd03b4f-e176-4b3a-ba63-b01ec4a9e170.webp
