VivIngInf/kaffettino-rebrewed/Resources/Images/Buongiornissimi/Generic/1b87f4f6f6bcae58b27e785f82037db5.jpg

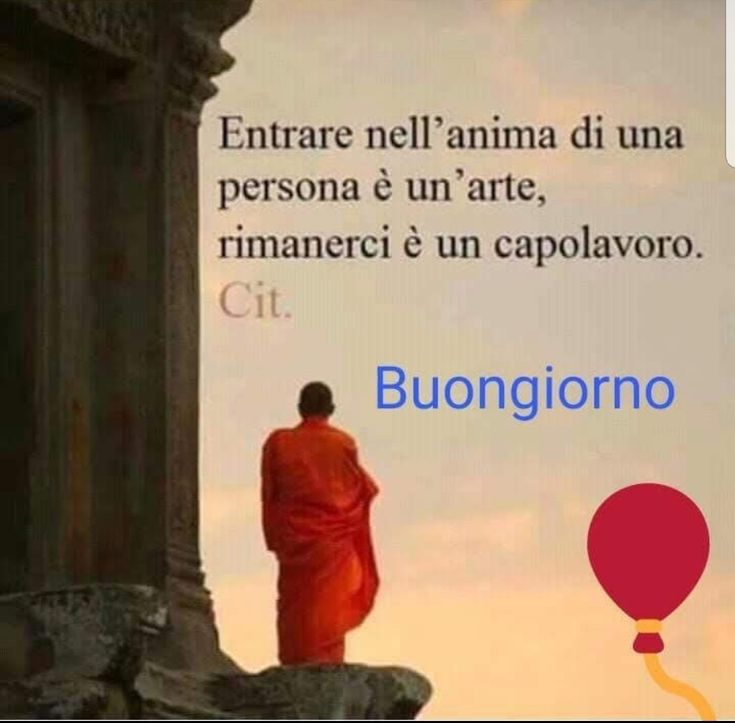
Resources/Images/Buongiornissimi/Generic/1b87f4f6f6bcae58b27e785f82037db5.jpg
