VivIngInf/kaffettino-rebrewed/Resources/Images/Buongiornissimi/Generic/5aa4cef3-88a1-4547-8e83-7e98b3b1e247.webp

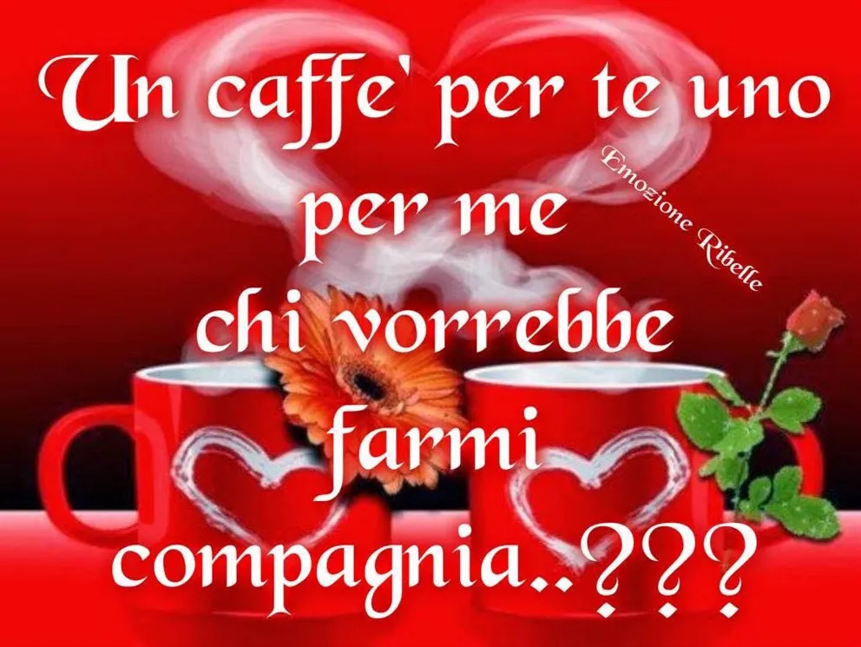
Resources/Images/Buongiornissimi/Generic/5aa4cef3-88a1-4547-8e83-7e98b3b1e247.webp
