VivIngInf/kaffettino-rebrewed/Resources/Images/Buongiornissimi/Generic/5b0cf740-647b-4bf8-86a9-f51fdd0b8581.webp

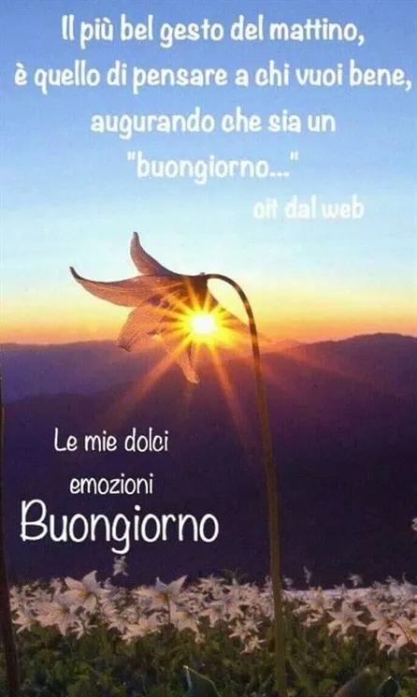
Resources/Images/Buongiornissimi/Generic/5b0cf740-647b-4bf8-86a9-f51fdd0b8581.webp
