VivIngInf/kaffettino-rebrewed/Resources/Images/Buongiornissimi/Generic/5b81dde2-28db-466e-8c16-6fa4bef59208.webp

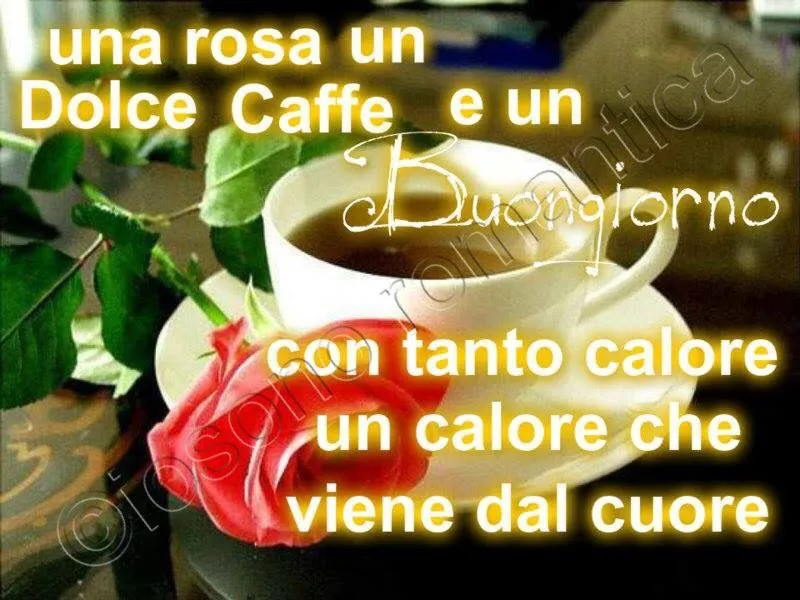
Resources/Images/Buongiornissimi/Generic/5b81dde2-28db-466e-8c16-6fa4bef59208.webp
