VivIngInf/kaffettino-rebrewed/Resources/Images/Buongiornissimi/Generic/5fd64717-fd01-4203-b0f4-138df30803b3.webp

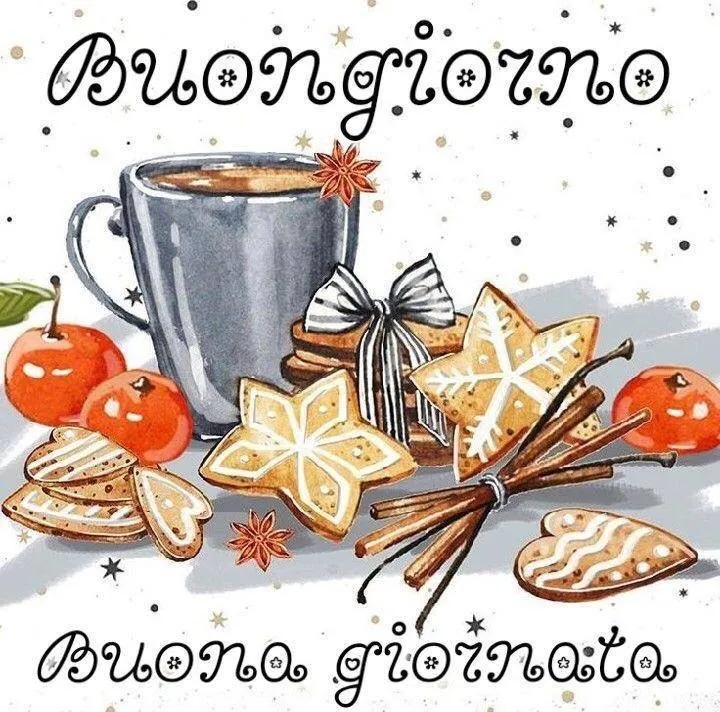
Resources/Images/Buongiornissimi/Generic/5fd64717-fd01-4203-b0f4-138df30803b3.webp
