VivIngInf/kaffettino-rebrewed/Resources/Images/Buongiornissimi/Generic/6b4ee7c6e6c8f73aadceb773648431fd.jpg

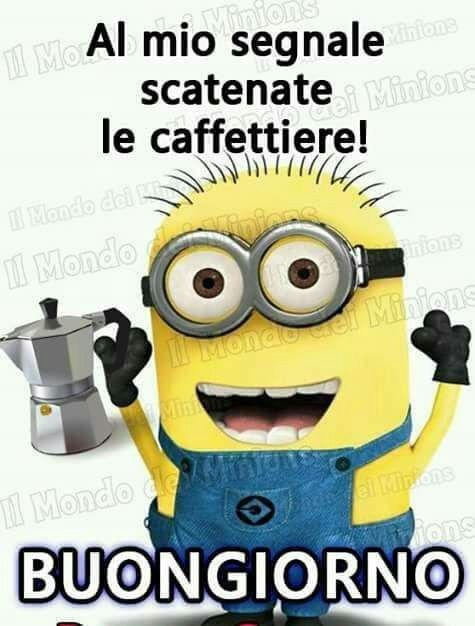
Resources/Images/Buongiornissimi/Generic/6b4ee7c6e6c8f73aadceb773648431fd.jpg
