VivIngInf/kaffettino-rebrewed/Resources/Images/Buongiornissimi/Generic/8c0f9481-1c6c-4b6d-8e49-031604e2f272.webp

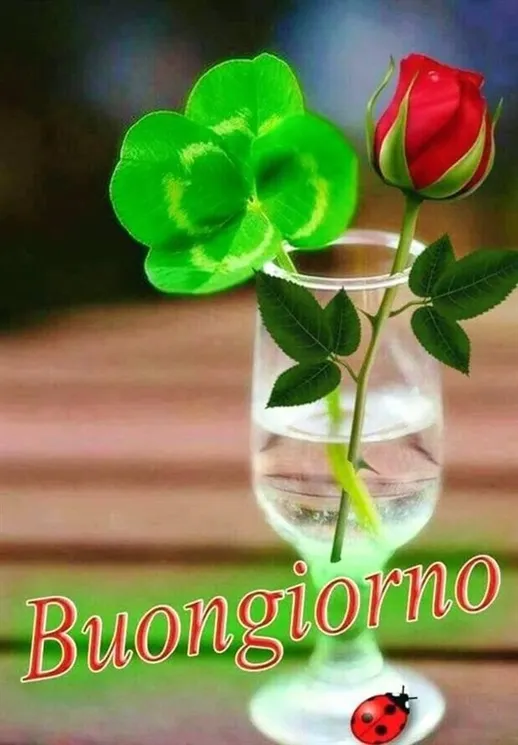
Resources/Images/Buongiornissimi/Generic/8c0f9481-1c6c-4b6d-8e49-031604e2f272.webp
