VivIngInf/kaffettino-rebrewed/Resources/Images/Buongiornissimi/Generic/9bb3ce2d-50fd-4d6e-9a53-dfc79c3d239a.webp

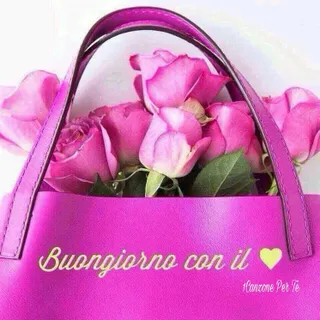
Resources/Images/Buongiornissimi/Generic/9bb3ce2d-50fd-4d6e-9a53-dfc79c3d239a.webp
