VivIngInf/kaffettino-rebrewed/Resources/Images/Buongiornissimi/Generic/9e38db0e-bb65-4197-bb3c-504397742d2d.webp

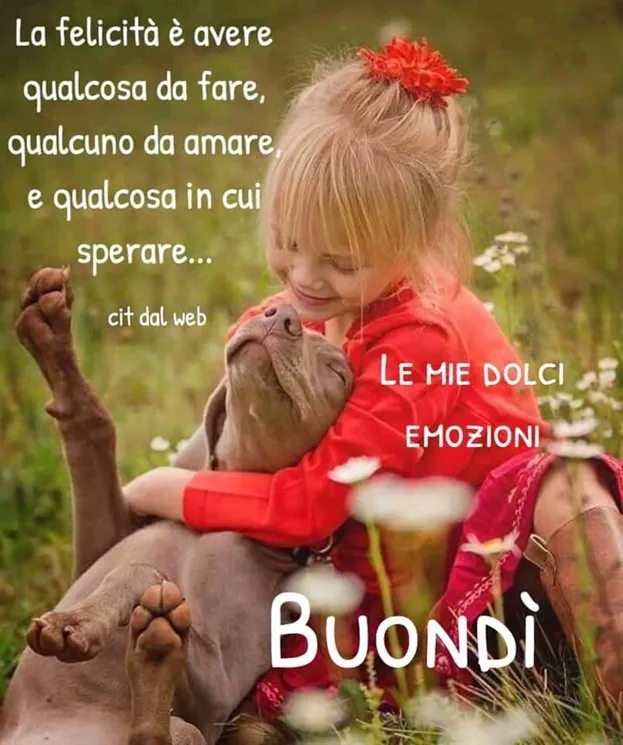
Resources/Images/Buongiornissimi/Generic/9e38db0e-bb65-4197-bb3c-504397742d2d.webp
