VivIngInf/kaffettino-rebrewed/Resources/Images/Buongiornissimi/Generic/10efbae6e278d4fe69cb8eef036e3af7.jpg

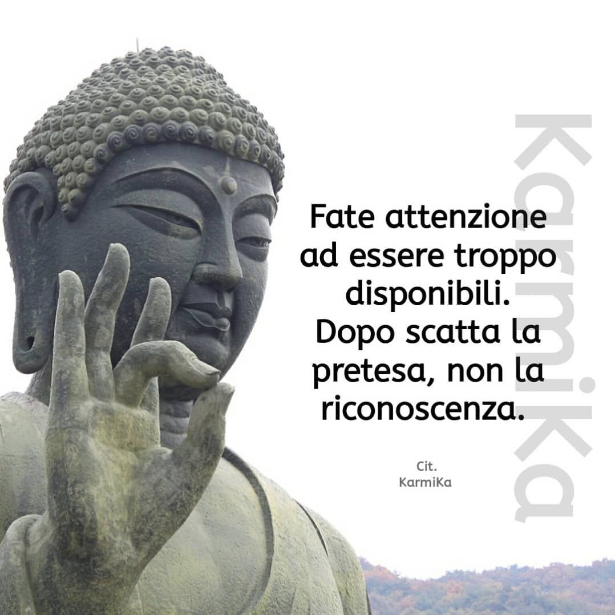
Resources/Images/Buongiornissimi/Generic/10efbae6e278d4fe69cb8eef036e3af7.jpg
