VivIngInf/kaffettino-rebrewed/Resources/Images/Buongiornissimi/Generic/22b4b0a0-1949-4e6d-b147-1446d3182da9.webp

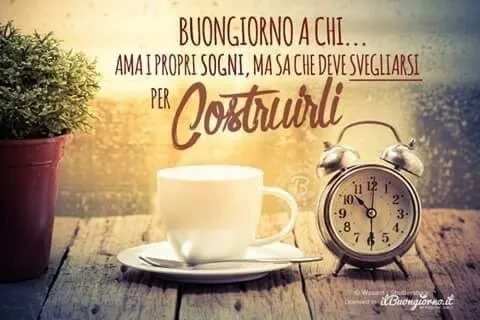
Resources/Images/Buongiornissimi/Generic/22b4b0a0-1949-4e6d-b147-1446d3182da9.webp
