VivIngInf/kaffettino-rebrewed/Resources/Images/Buongiornissimi/Generic/56c3cdce-9aa5-417f-94c6-ebe91152a586.webp

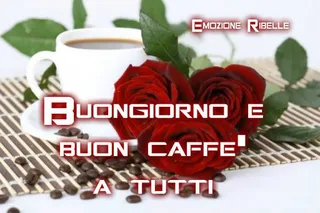
Resources/Images/Buongiornissimi/Generic/56c3cdce-9aa5-417f-94c6-ebe91152a586.webp
