VivIngInf/kaffettino-rebrewed/Resources/Images/Buongiornissimi/Generic/60c8fa58-d0fb-4c18-b04b-db5620e8aa8a.webp

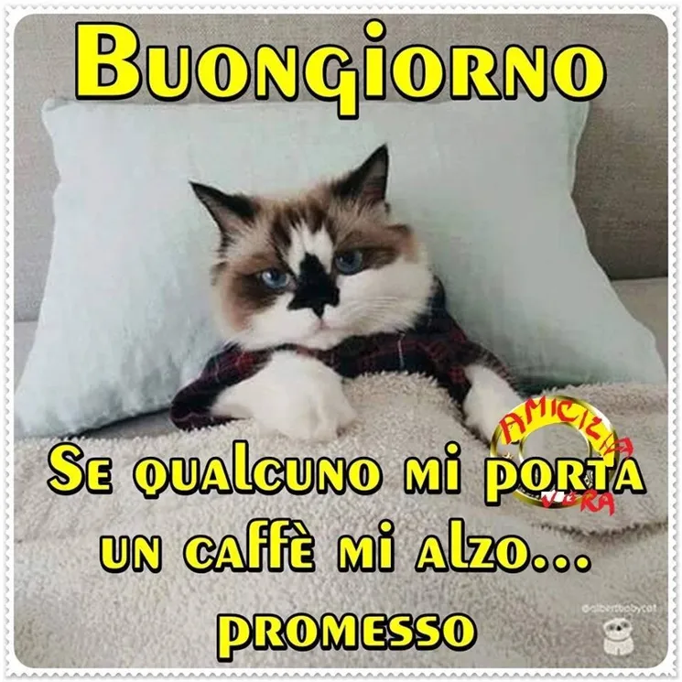
Resources/Images/Buongiornissimi/Generic/60c8fa58-d0fb-4c18-b04b-db5620e8aa8a.webp
