VivIngInf/kaffettino-rebrewed/Resources/Images/Buongiornissimi/Generic/74a548ed2f69eb4367773a2d7d45e5c0.jpg

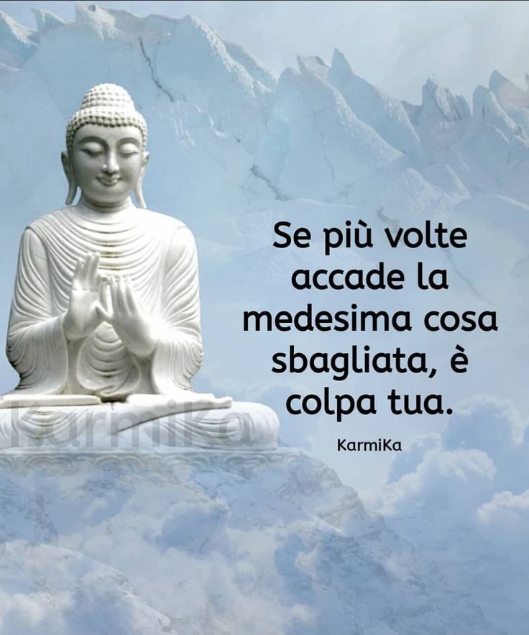
Resources/Images/Buongiornissimi/Generic/74a548ed2f69eb4367773a2d7d45e5c0.jpg
