VivIngInf/kaffettino-rebrewed/Resources/Images/Buongiornissimi/Generic/76ff6ede-9fb5-4364-92ce-060d82894dc9.webp

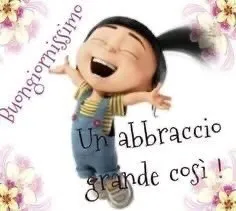
Resources/Images/Buongiornissimi/Generic/76ff6ede-9fb5-4364-92ce-060d82894dc9.webp
