VivIngInf/kaffettino-rebrewed/Resources/Images/Buongiornissimi/Generic/77e8747b-7521-45c7-a4d6-5395b19dc438.webp

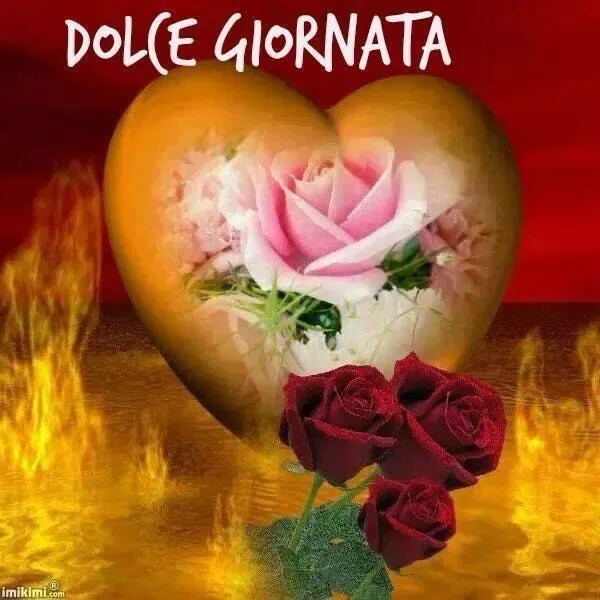
Resources/Images/Buongiornissimi/Generic/77e8747b-7521-45c7-a4d6-5395b19dc438.webp
