VivIngInf/kaffettino-rebrewed/Resources/Images/Buongiornissimi/Generic/85caae59-a019-45fd-bce3-38656babeaa1.webp

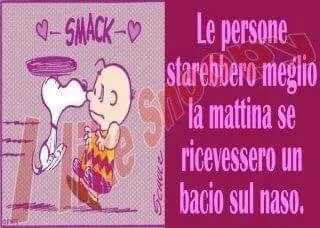
Resources/Images/Buongiornissimi/Generic/85caae59-a019-45fd-bce3-38656babeaa1.webp
