VivIngInf/kaffettino-rebrewed/Resources/Images/Buongiornissimi/Generic/98a0391545f2d568e55d5a8558e42584.jpg

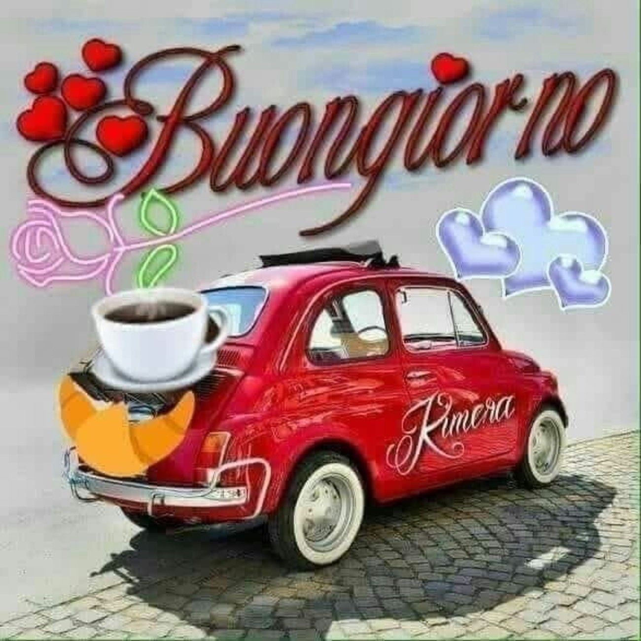
Resources/Images/Buongiornissimi/Generic/98a0391545f2d568e55d5a8558e42584.jpg
