VivIngInf/kaffettino-rebrewed/Resources/Images/Buongiornissimi/Generic/157c298f-6cad-449f-89ac-1644cc5fb77e.webp

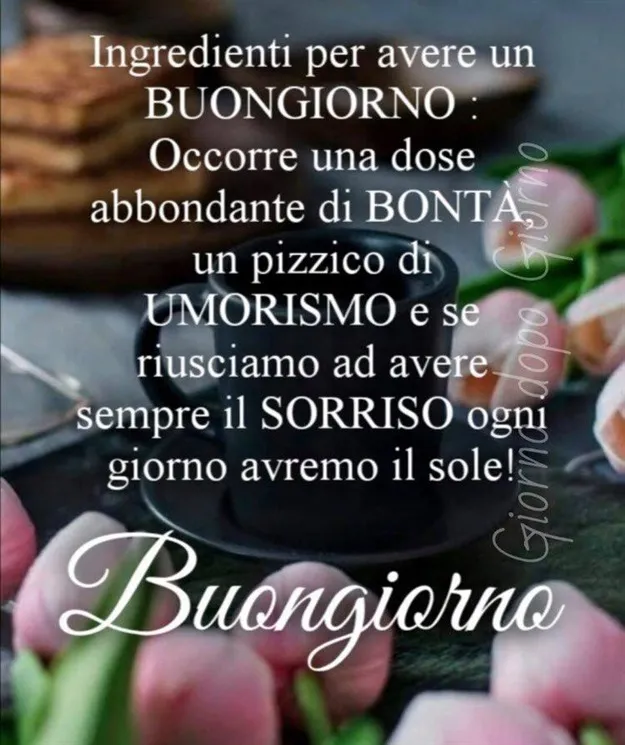
Resources/Images/Buongiornissimi/Generic/157c298f-6cad-449f-89ac-1644cc5fb77e.webp
