VivIngInf/kaffettino-rebrewed/Resources/Images/Buongiornissimi/Generic/815a67853370c019c04a44d6eb07f9b1.jpg

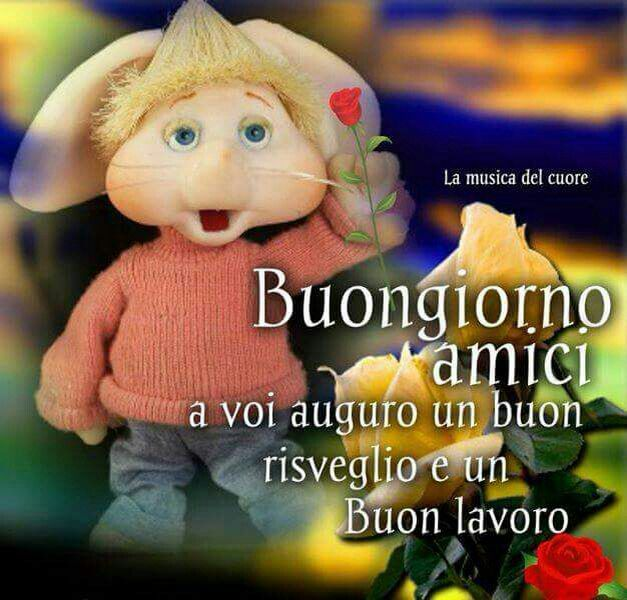
Resources/Images/Buongiornissimi/Generic/815a67853370c019c04a44d6eb07f9b1.jpg
