VivIngInf/kaffettino-rebrewed/Resources/Images/Buongiornissimi/Generic/828d6648-c863-4f1b-b4ef-9f10e72b7218.webp

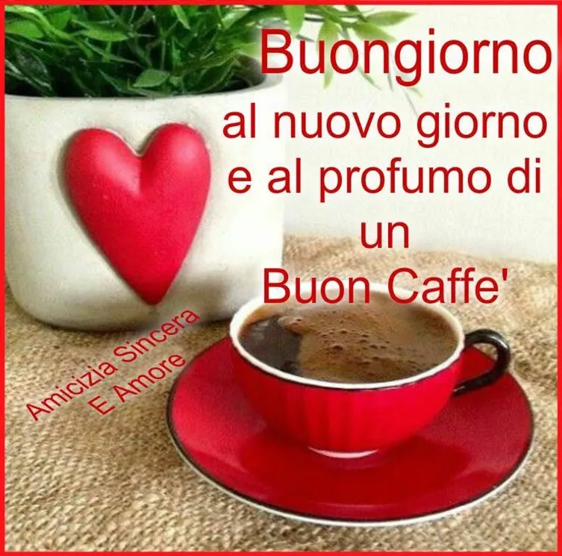
Resources/Images/Buongiornissimi/Generic/828d6648-c863-4f1b-b4ef-9f10e72b7218.webp
