VivIngInf/kaffettino-rebrewed/Resources/Images/Buongiornissimi/Generic/1482c3cd-0d9d-42ee-9c26-3ffe86cfa517.webp

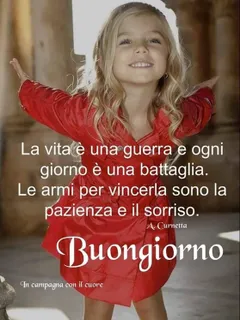
Resources/Images/Buongiornissimi/Generic/1482c3cd-0d9d-42ee-9c26-3ffe86cfa517.webp
