VivIngInf/kaffettino-rebrewed/Resources/Images/Buongiornissimi/Generic/4747ad4f50aee21f61521fef9f947030.jpg

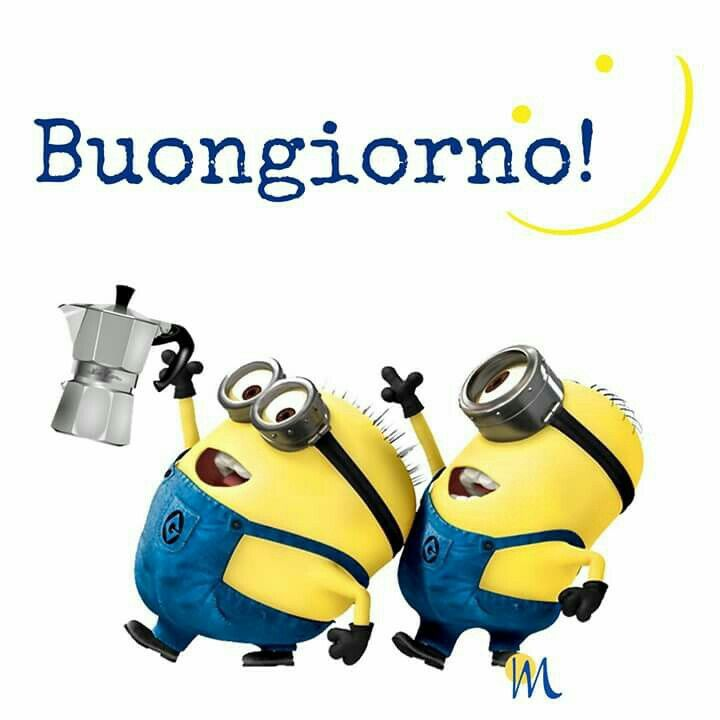
Resources/Images/Buongiornissimi/Generic/4747ad4f50aee21f61521fef9f947030.jpg
