VivIngInf/kaffettino-rebrewed/Resources/Images/Buongiornissimi/Generic/6804c4fa-e695-49a2-9704-2db2e0143d5b.webp

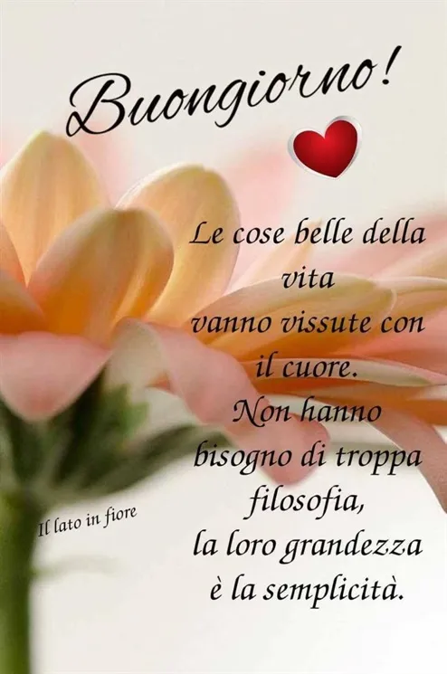
Resources/Images/Buongiornissimi/Generic/6804c4fa-e695-49a2-9704-2db2e0143d5b.webp
