VivIngInf/kaffettino-rebrewed/Resources/Images/Buongiornissimi/Generic/286699b4-24ea-4fdf-8fc1-25eb198ec6a5.webp

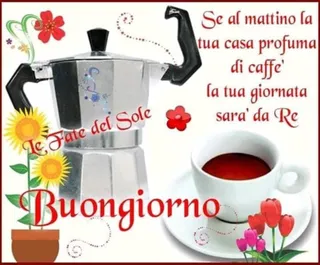
Resources/Images/Buongiornissimi/Generic/286699b4-24ea-4fdf-8fc1-25eb198ec6a5.webp
