VivIngInf/kaffettino-rebrewed/Resources/Images/Buongiornissimi/Generic/620125ae-3254-4791-b95e-2a63fea609cc.webp

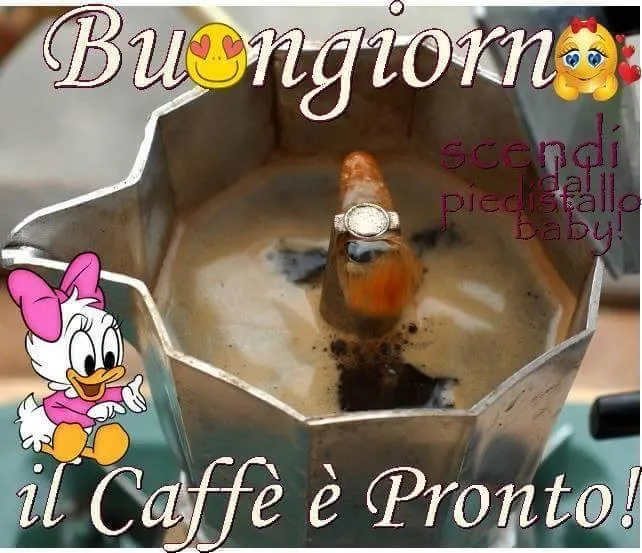
Resources/Images/Buongiornissimi/Generic/620125ae-3254-4791-b95e-2a63fea609cc.webp
