VivIngInf/kaffettino-rebrewed/Resources/Images/Buongiornissimi/Generic/7323754e-8d31-4471-bb27-1d2d5df5b123.webp

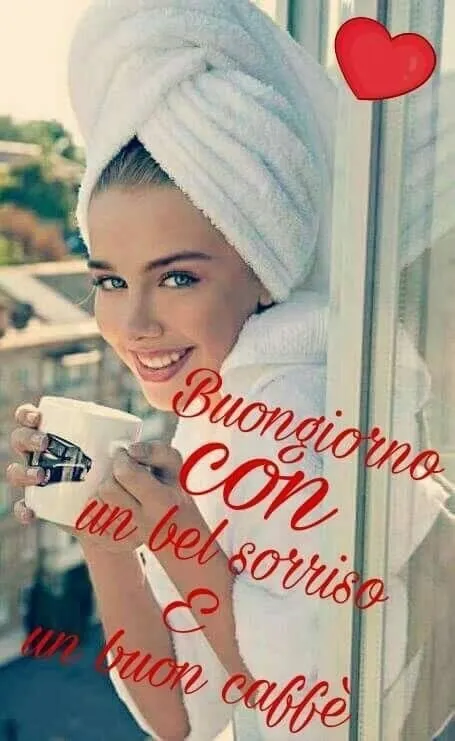
Resources/Images/Buongiornissimi/Generic/7323754e-8d31-4471-bb27-1d2d5df5b123.webp
