VivIngInf/kaffettino-rebrewed/Resources/Images/Buongiornissimi/Generic/Accompagnaci-Maria.jpg

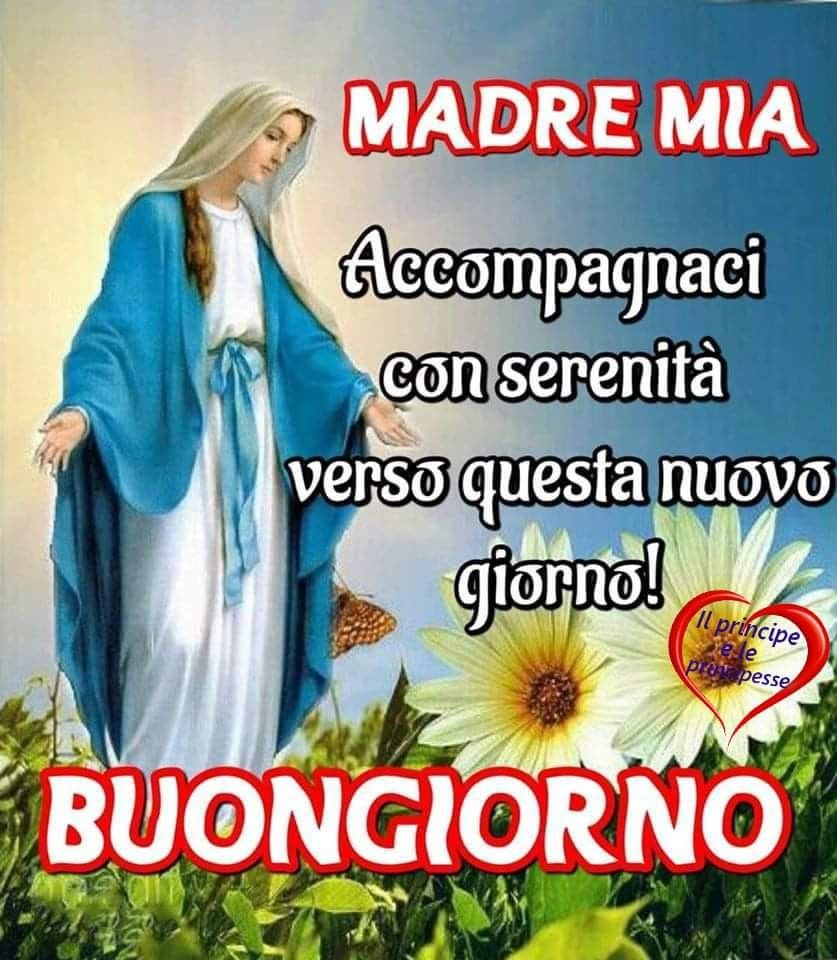
Resources/Images/Buongiornissimi/Generic/Accompagnaci-Maria.jpg
