VivIngInf/kaffettino-rebrewed/Resources/Images/Buongiornissimi/Generic/ad64a67d-0613-44a9-b77c-b0592c5aa7a5.webp

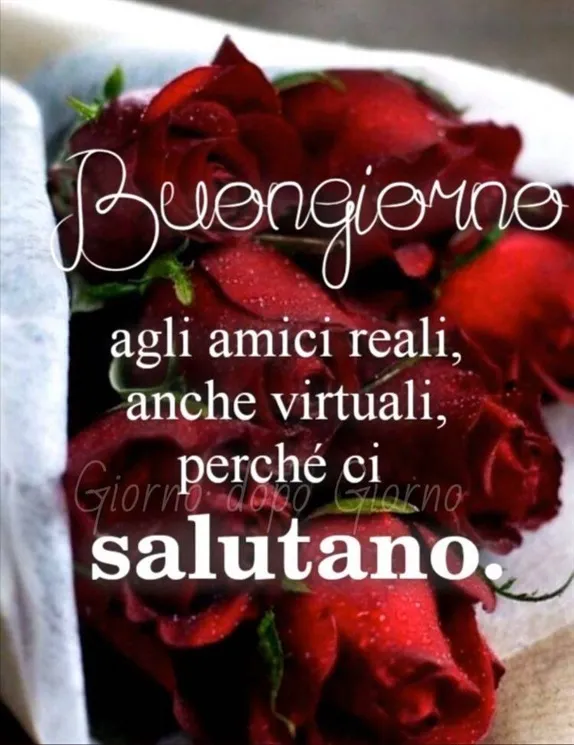
Resources/Images/Buongiornissimi/Generic/ad64a67d-0613-44a9-b77c-b0592c5aa7a5.webp
