VivIngInf/kaffettino-rebrewed/Resources/Images/Buongiornissimi/Generic/Amore-di-Madre-Maria-Buongiorno.jpg

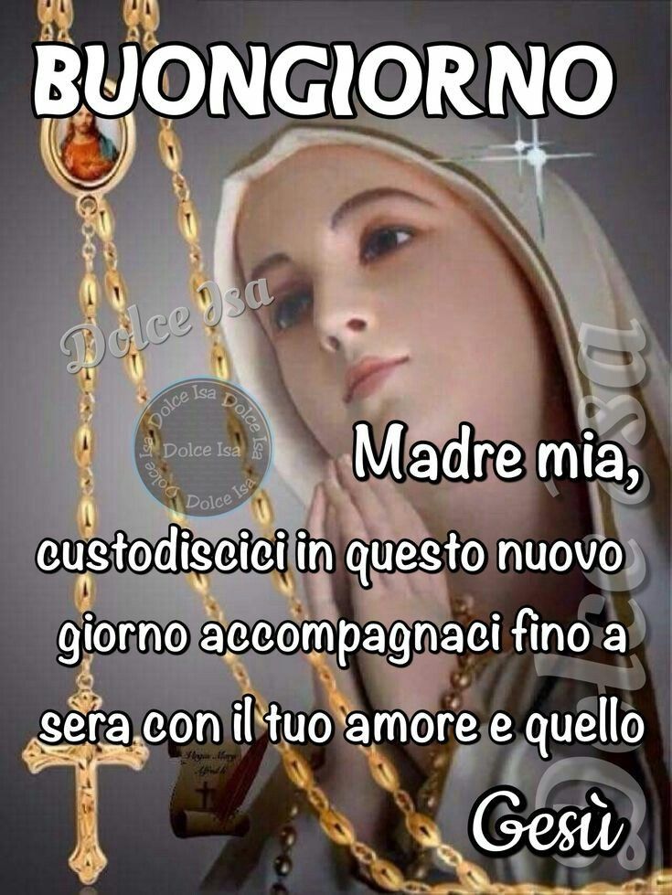
Resources/Images/Buongiornissimi/Generic/Amore-di-Madre-Maria-Buongiorno.jpg
