VivIngInf/kaffettino-rebrewed/Resources/Images/Buongiornissimi/Generic/Annunci-un-nuovo-giorno.jpg

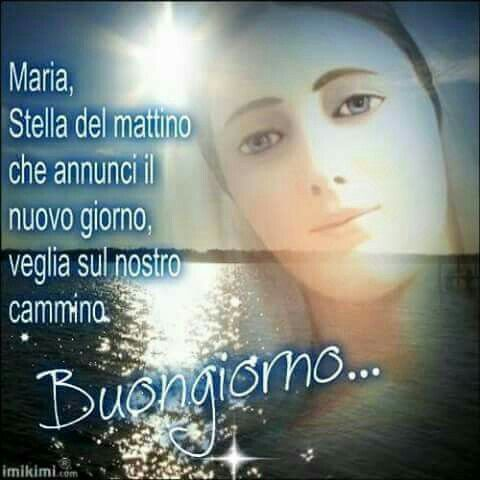
Resources/Images/Buongiornissimi/Generic/Annunci-un-nuovo-giorno.jpg
