VivIngInf/kaffettino-rebrewed/Resources/Images/Buongiornissimi/Generic/b5925bc1-4dbc-492c-998a-7862e984bb73.webp

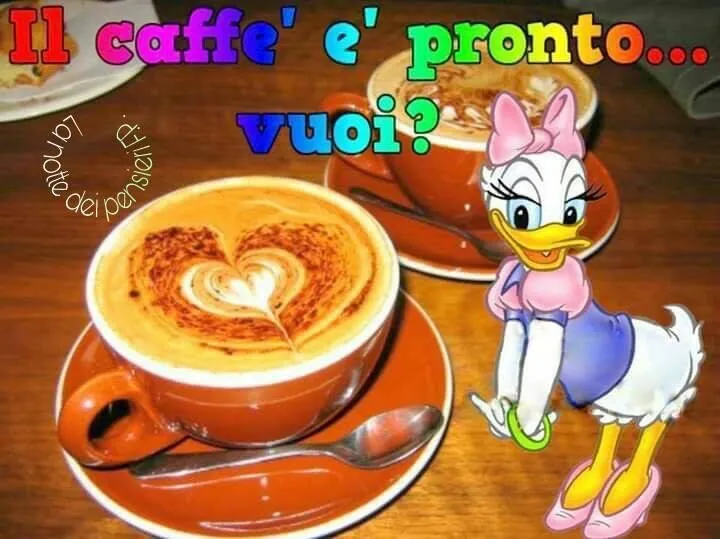
Resources/Images/Buongiornissimi/Generic/b5925bc1-4dbc-492c-998a-7862e984bb73.webp
