VivIngInf/kaffettino-rebrewed/Resources/Images/Buongiornissimi/Generic/ba7a61ee-a637-40c8-a5da-7025822e2f56.webp

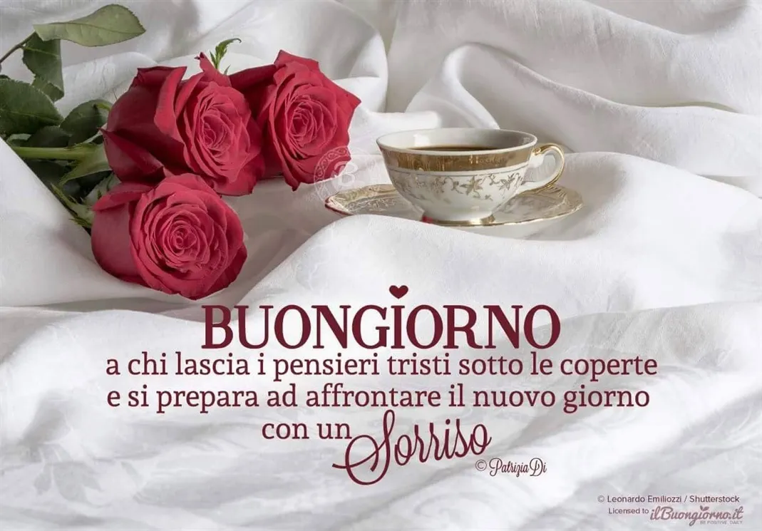
Resources/Images/Buongiornissimi/Generic/ba7a61ee-a637-40c8-a5da-7025822e2f56.webp
