VivIngInf/kaffettino-rebrewed/Resources/Images/Buongiornissimi/Generic/Benedico-la-tua-giornata-e-la-tua-famiglia.jpg

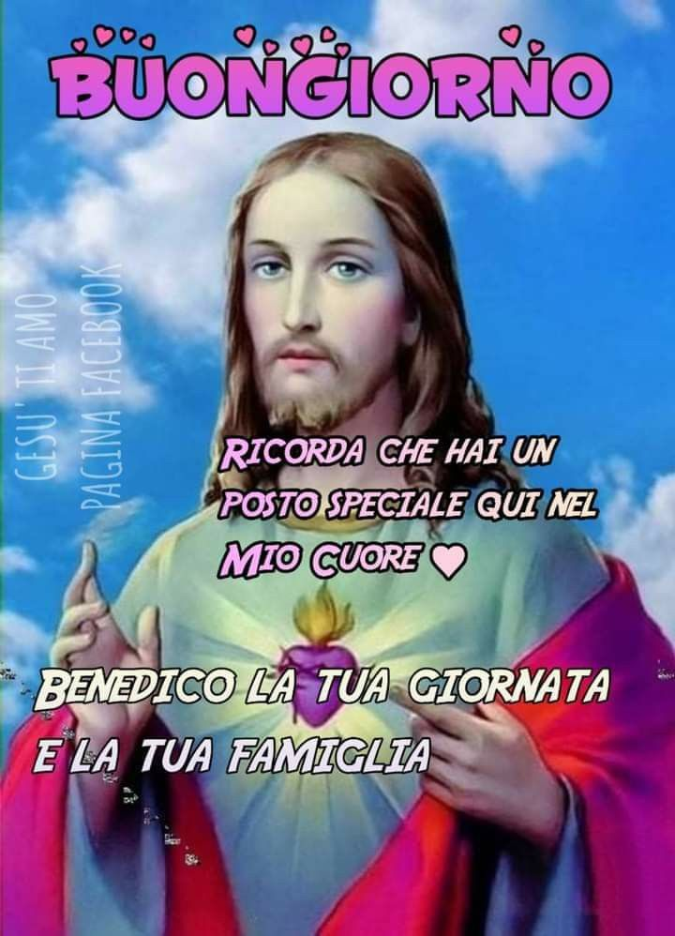
Resources/Images/Buongiornissimi/Generic/Benedico-la-tua-giornata-e-la-tua-famiglia.jpg
