VivIngInf/kaffettino-rebrewed/Resources/Images/Buongiornissimi/Generic/Buon-Giorno-Dio-vi-benedica-6.jpg

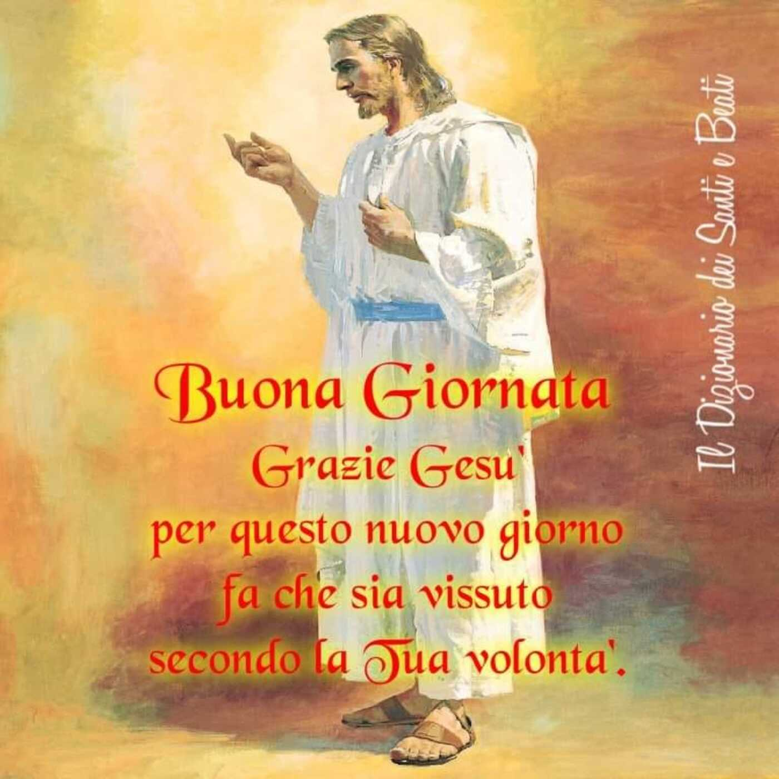
Resources/Images/Buongiornissimi/Generic/Buon-Giorno-Dio-vi-benedica-6.jpg
