VivIngInf/kaffettino-rebrewed/Resources/Images/Buongiornissimi/Generic/Buona-Giornata-Madonnina.jpg

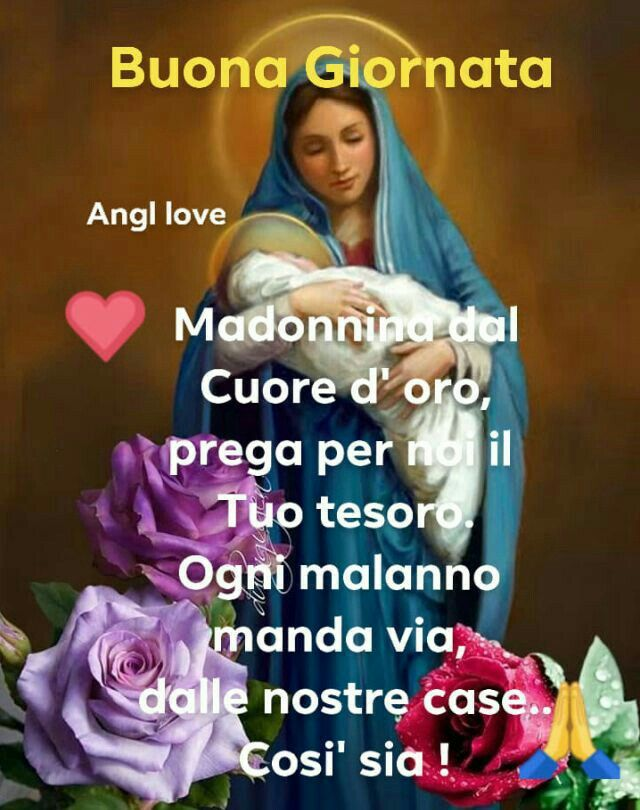
Resources/Images/Buongiornissimi/Generic/Buona-Giornata-Madonnina.jpg
