VivIngInf/kaffettino-rebrewed/Resources/Images/Buongiornissimi/Generic/Buongiorno-con-Maria.jpg

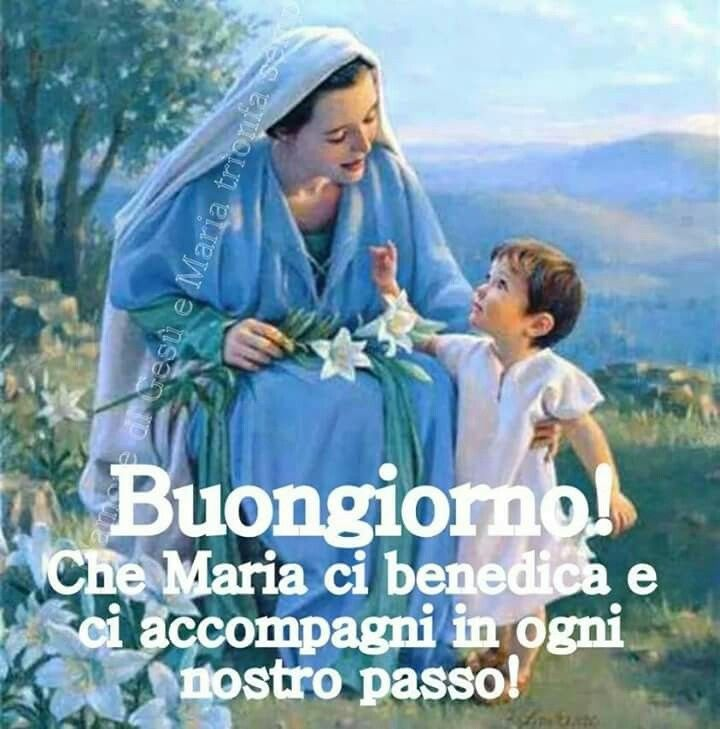
Resources/Images/Buongiornissimi/Generic/Buongiorno-con-Maria.jpg
