VivIngInf/kaffettino-rebrewed/Resources/Images/Buongiornissimi/Generic/Buongiorno-religioso-9.jpg

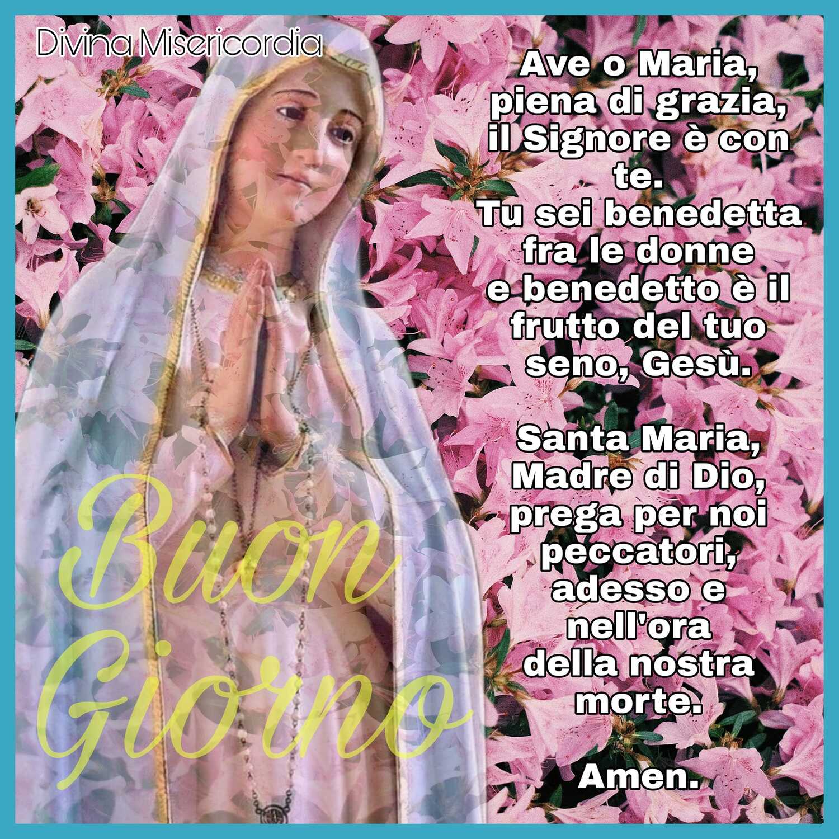
Resources/Images/Buongiornissimi/Generic/Buongiorno-religioso-9.jpg
