VivIngInf/kaffettino-rebrewed/Resources/Images/Buongiornissimi/Generic/Buongiorno-religioso-link-bellissimi-23-1024x1024.jpg

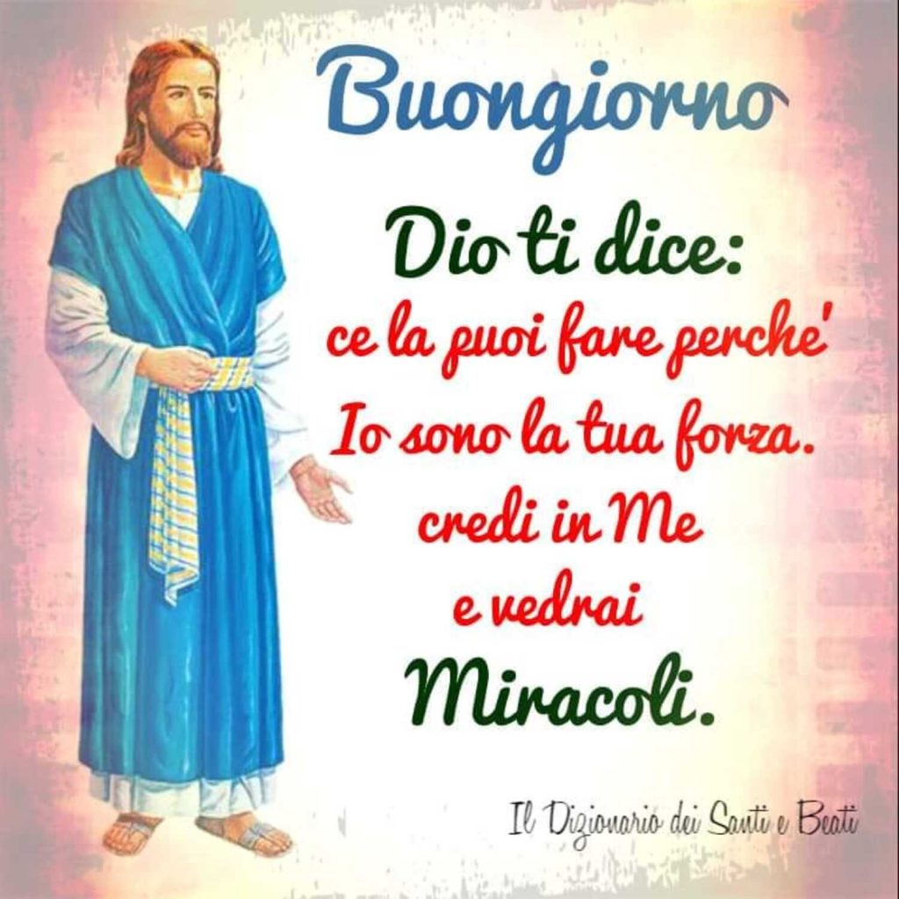
Resources/Images/Buongiornissimi/Generic/Buongiorno-religioso-link-bellissimi-23-1024x1024.jpg
