VivIngInf/kaffettino-rebrewed/Resources/Images/Buongiornissimi/Generic/c27aefe0-6cec-4100-ba61-06b469922b3d.webp

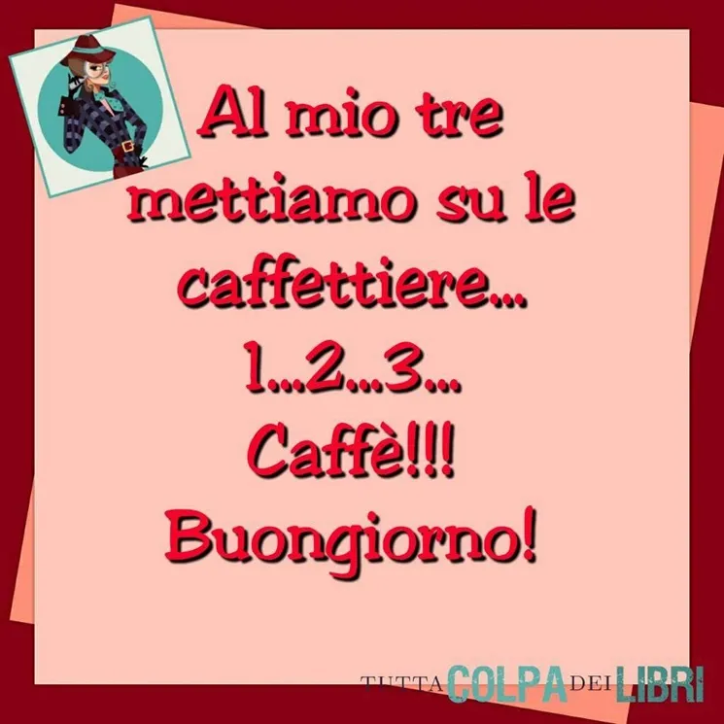
Resources/Images/Buongiornissimi/Generic/c27aefe0-6cec-4100-ba61-06b469922b3d.webp
