VivIngInf/kaffettino-rebrewed/Resources/Images/Buongiornissimi/Generic/c0834764-381d-474d-847b-bfe4e8e80e86.webp

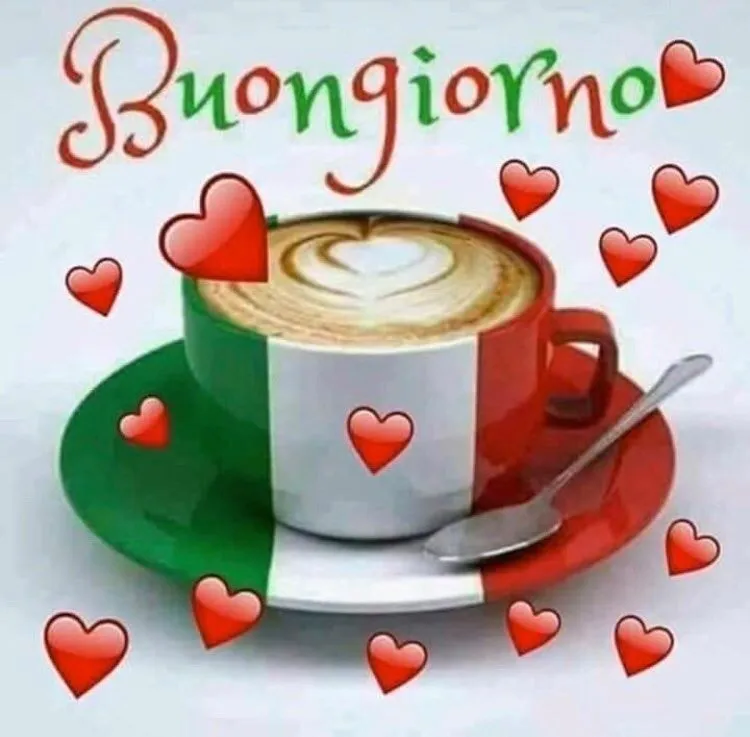
Resources/Images/Buongiornissimi/Generic/c0834764-381d-474d-847b-bfe4e8e80e86.webp
