VivIngInf/kaffettino-rebrewed/Resources/Images/Buongiornissimi/Generic/cf484c48-05ae-4d1e-ae1e-7fb168d18c87.webp

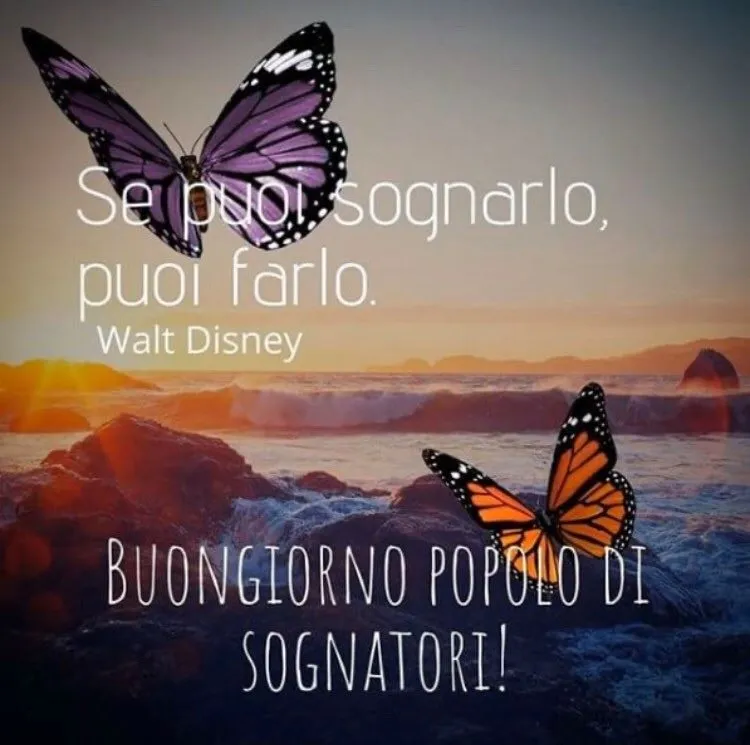
Resources/Images/Buongiornissimi/Generic/cf484c48-05ae-4d1e-ae1e-7fb168d18c87.webp
