VivIngInf/kaffettino-rebrewed/Resources/Images/Buongiornissimi/Generic/confucio-accontentarsi.jpg

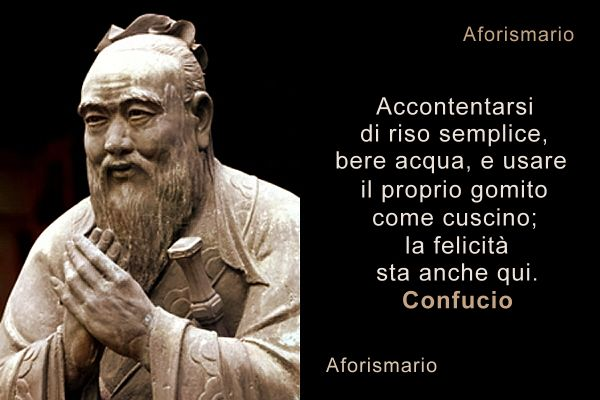
Resources/Images/Buongiornissimi/Generic/confucio-accontentarsi.jpg
