VivIngInf/kaffettino-rebrewed/Resources/Images/Buongiornissimi/Generic/d1cc1f65-66d0-49d1-8d30-7a559ded4f57.webp

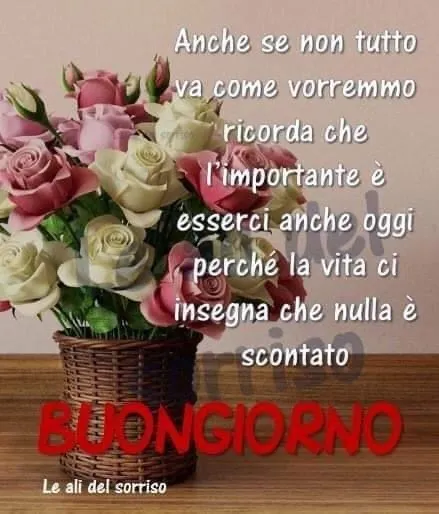
Resources/Images/Buongiornissimi/Generic/d1cc1f65-66d0-49d1-8d30-7a559ded4f57.webp
