VivIngInf/kaffettino-rebrewed/Resources/Images/Buongiornissimi/Generic/dd9f153e-cef9-47d7-be47-0786f366cde2.webp

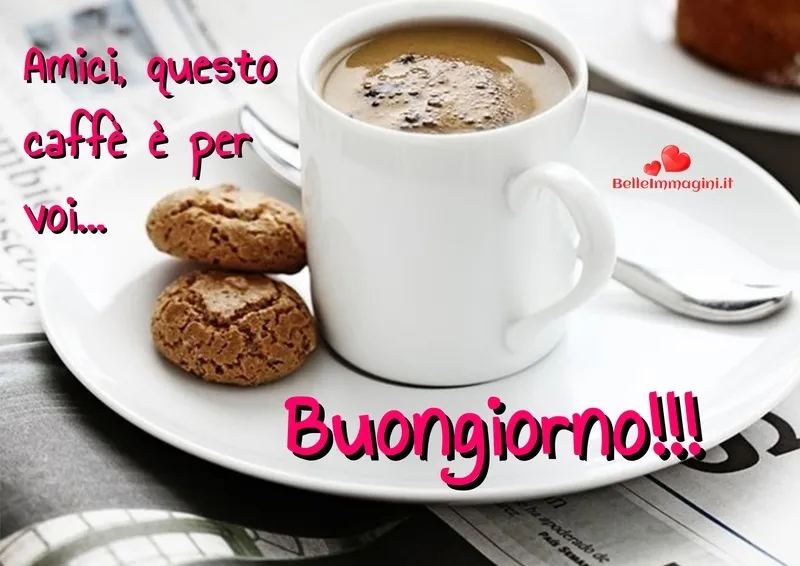
Resources/Images/Buongiornissimi/Generic/dd9f153e-cef9-47d7-be47-0786f366cde2.webp
