VivIngInf/kaffettino-rebrewed/Resources/Images/Buongiornissimi/Generic/ddf8ba0c-9baf-47c8-8224-497226b03e32.webp

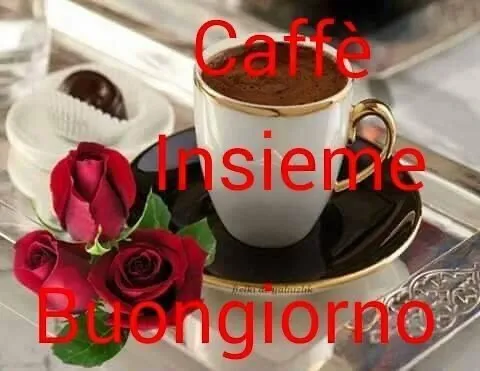
Resources/Images/Buongiornissimi/Generic/ddf8ba0c-9baf-47c8-8224-497226b03e32.webp
