VivIngInf/kaffettino-rebrewed/Resources/Images/Buongiornissimi/Generic/Dio-ti-protegga.jpg

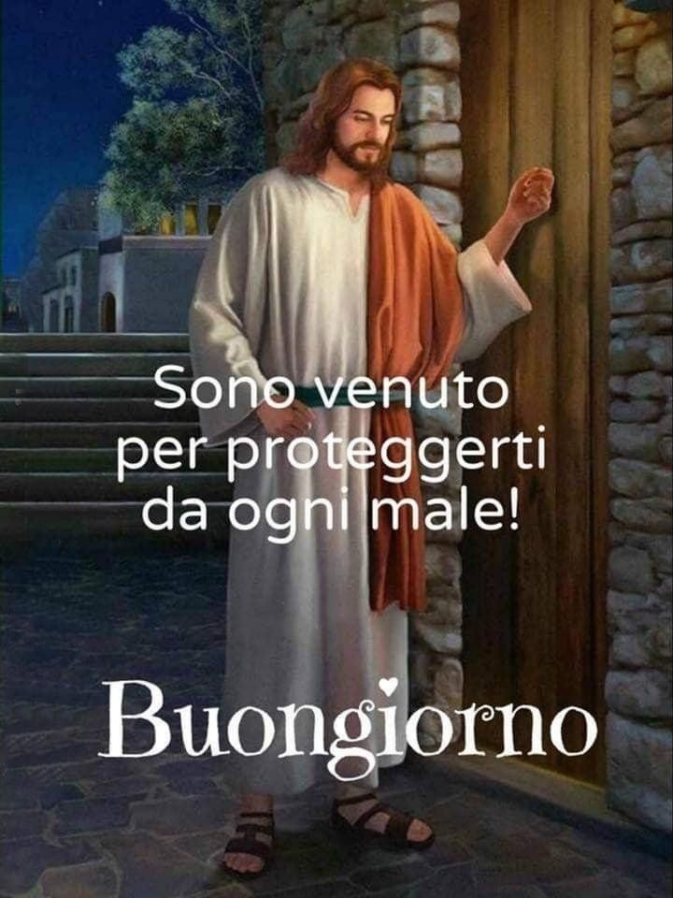
Resources/Images/Buongiornissimi/Generic/Dio-ti-protegga.jpg
