VivIngInf/kaffettino-rebrewed/Resources/Images/Buongiornissimi/Generic/e16a8c5f-9fd3-468a-8ef3-a6b7f8038ee3.webp

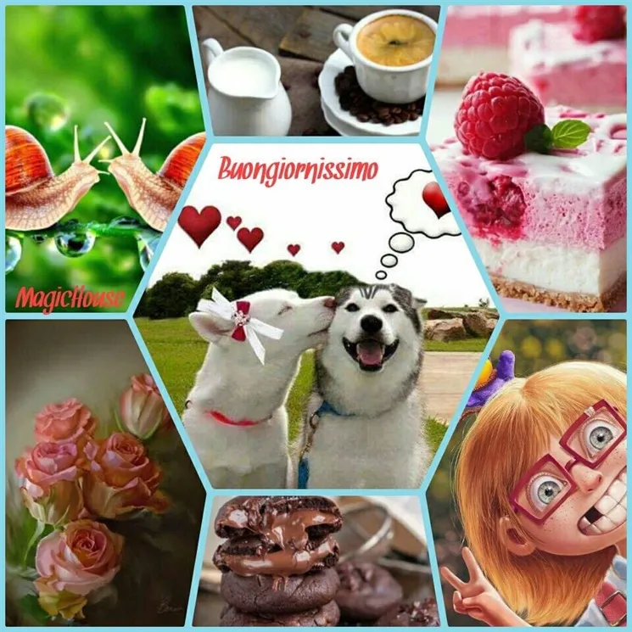
Resources/Images/Buongiornissimi/Generic/e16a8c5f-9fd3-468a-8ef3-a6b7f8038ee3.webp
