VivIngInf/kaffettino-rebrewed/Resources/Images/Buongiornissimi/Generic/e88fd98a3c1a37a0517caea03cec3ccf.jpg

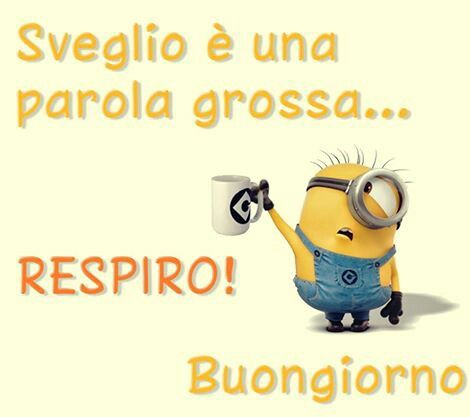
Resources/Images/Buongiornissimi/Generic/e88fd98a3c1a37a0517caea03cec3ccf.jpg
