VivIngInf/kaffettino-rebrewed/Resources/Images/Buongiornissimi/Generic/e92e4e53876411f93f4c04bde929a6ae.jpg

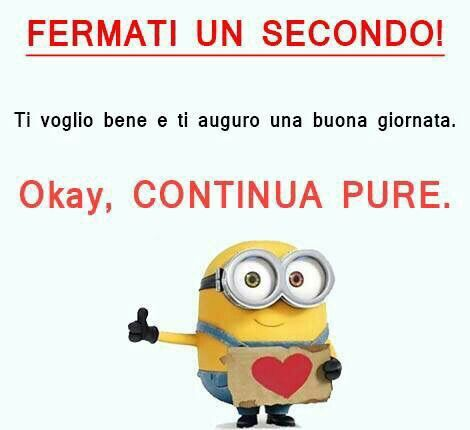
Resources/Images/Buongiornissimi/Generic/e92e4e53876411f93f4c04bde929a6ae.jpg
