VivIngInf/kaffettino-rebrewed/Resources/Images/Buongiornissimi/Generic/e41205ab-6bed-404f-89e0-813f154c2fc9.webp

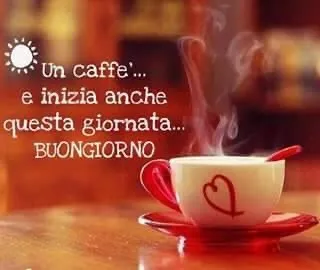
Resources/Images/Buongiornissimi/Generic/e41205ab-6bed-404f-89e0-813f154c2fc9.webp
