VivIngInf/kaffettino-rebrewed/Resources/Images/Buongiornissimi/Generic/ed44c3a8-0faf-4869-8847-27ea5380bf00.webp

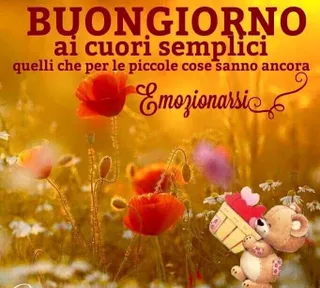
Resources/Images/Buongiornissimi/Generic/ed44c3a8-0faf-4869-8847-27ea5380bf00.webp
