VivIngInf/kaffettino-rebrewed/Resources/Images/Buongiornissimi/Generic/Et7j6mOWgAUVToV.jpeg

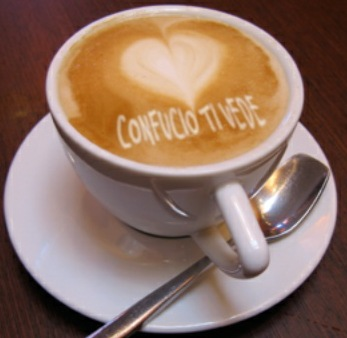
Resources/Images/Buongiornissimi/Generic/Et7j6mOWgAUVToV.jpeg
