VivIngInf/kaffettino-rebrewed/Resources/Images/Buongiornissimi/Generic/Foto-del-Buongiorno-religiose-gratis-16-1024x1024.jpg

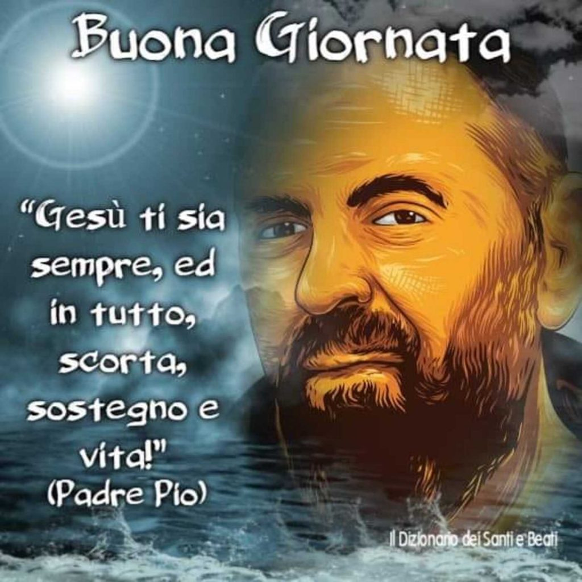
Resources/Images/Buongiornissimi/Generic/Foto-del-Buongiorno-religiose-gratis-16-1024x1024.jpg
