VivIngInf/kaffettino-rebrewed/Resources/Images/Buongiornissimi/Generic/Frasi-confucio-1.jpg

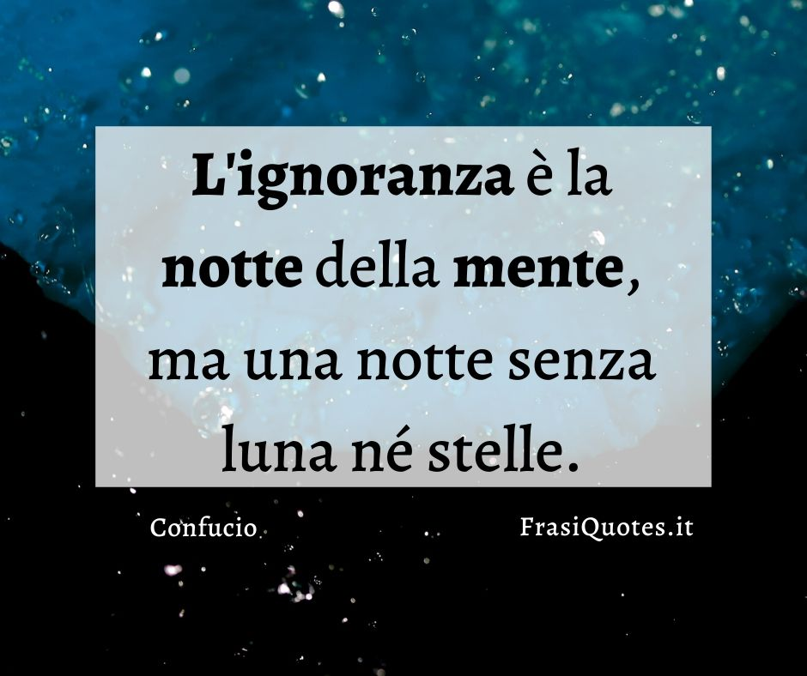
Resources/Images/Buongiornissimi/Generic/Frasi-confucio-1.jpg
