VivIngInf/kaffettino-rebrewed/Resources/Images/Buongiornissimi/Generic/Gabbo_easteregg.jpg

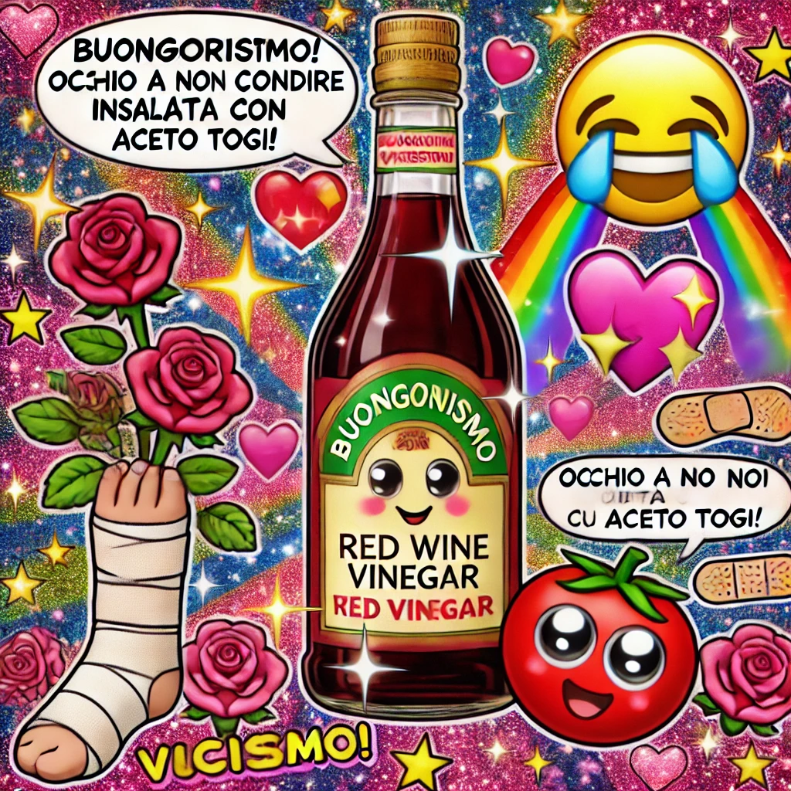
Resources/Images/Buongiornissimi/Generic/Gabbo_easteregg.jpg
