VivIngInf/kaffettino-rebrewed/Resources/Images/Buongiornissimi/Generic/Immagini-Buongiorno-Minions-1.jpg

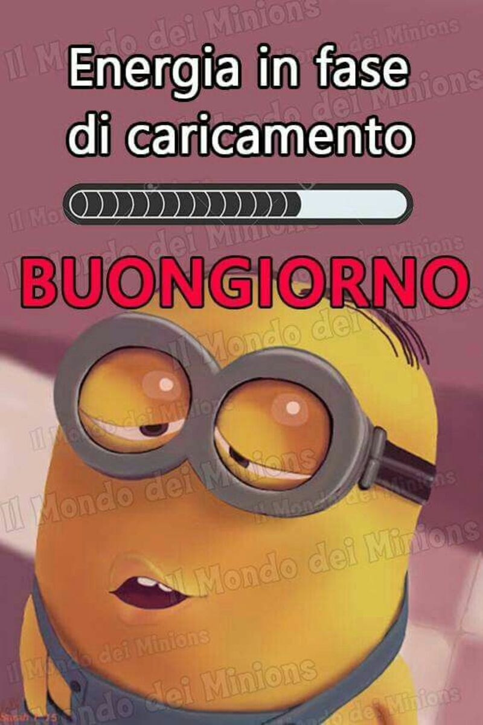
Resources/Images/Buongiornissimi/Generic/Immagini-Buongiorno-Minions-1.jpg
