VivIngInf/kaffettino-rebrewed/Resources/Images/Buongiornissimi/Generic/jason-borne-zeus-good-morning.jpg

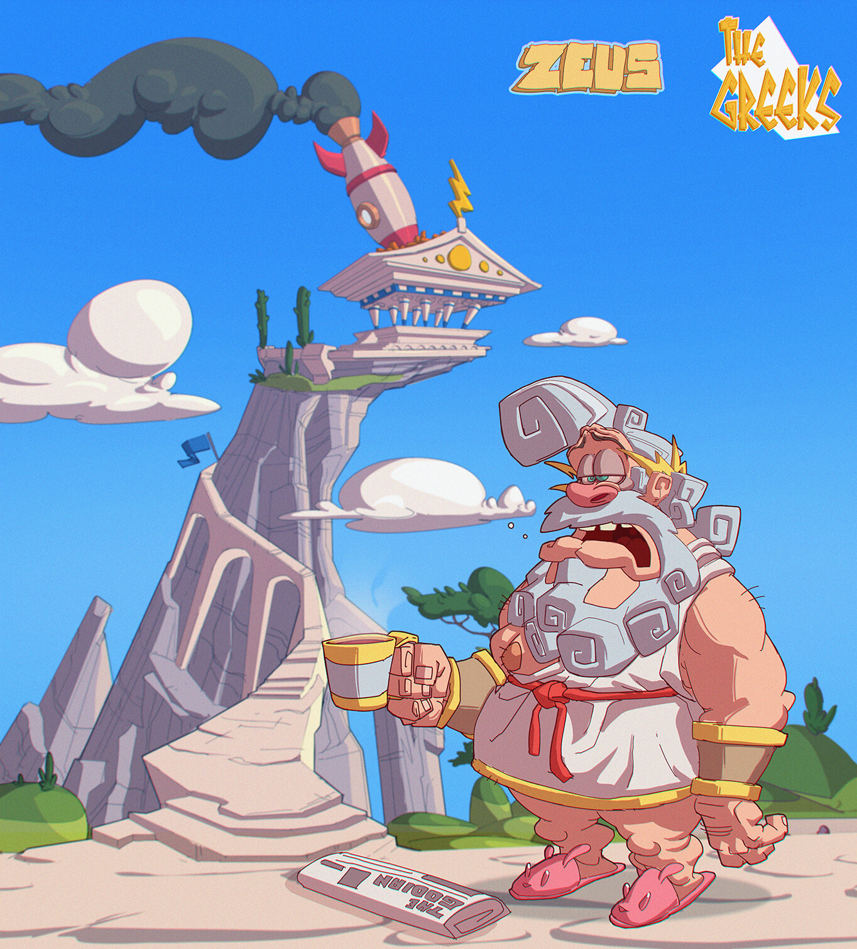
Resources/Images/Buongiornissimi/Generic/jason-borne-zeus-good-morning.jpg
