VivIngInf/kaffettino-rebrewed/Resources/Images/Buongiornissimi/Generic/Link-religiosi-di-buongiorno-24.jpg

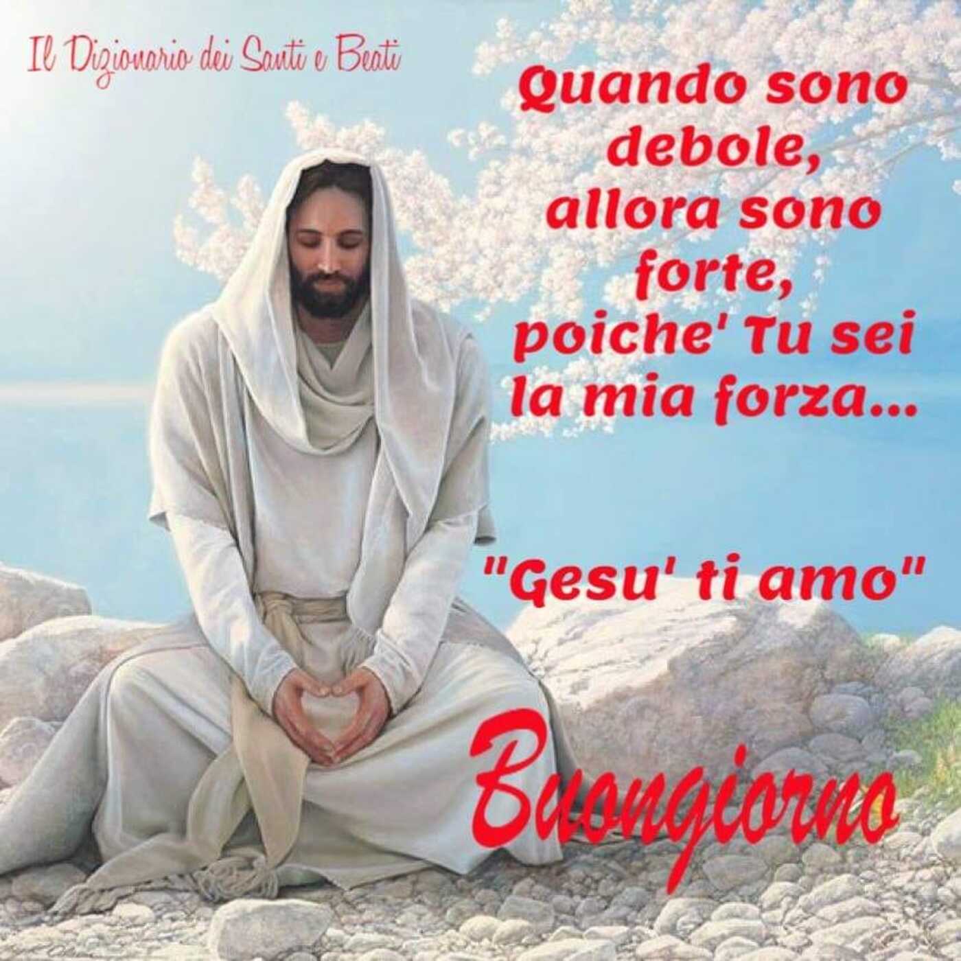
Resources/Images/Buongiornissimi/Generic/Link-religiosi-di-buongiorno-24.jpg
