VivIngInf/kaffettino-rebrewed/Resources/Images/Buongiornissimi/Generic/MinionMorto.jpg

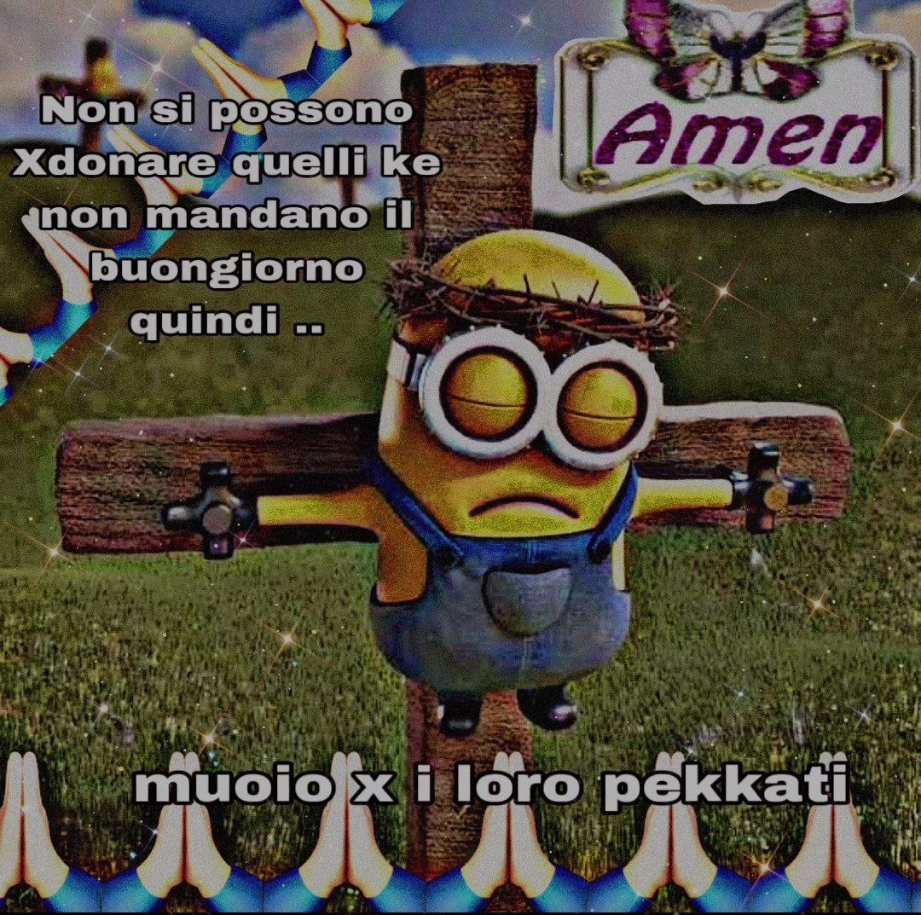
Resources/Images/Buongiornissimi/Generic/MinionMorto.jpg
