VivIngInf/kaffettino-rebrewed/Resources/Images/Buongiornissimi/Generic/Padre Pio 1.png

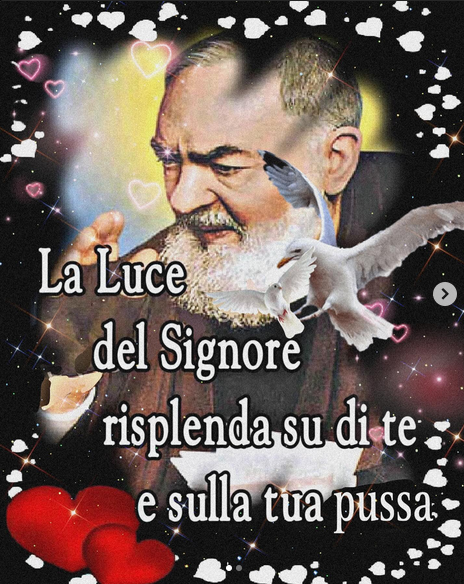
Resources/Images/Buongiornissimi/Generic/Padre Pio 1.png
