VivIngInf/kaffettino-rebrewed/Resources/Images/Buongiornissimi/Generic/Padre Pio 2.png

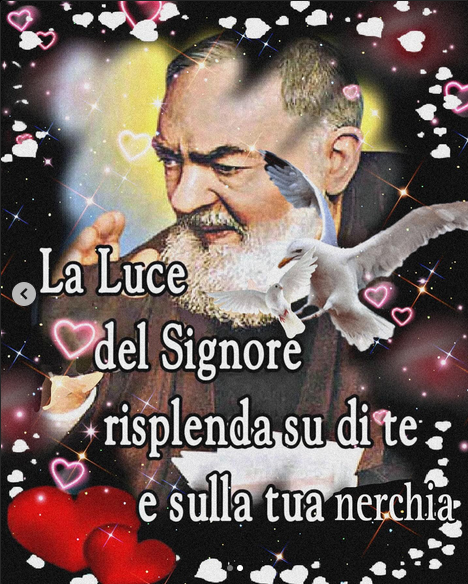
Resources/Images/Buongiornissimi/Generic/Padre Pio 2.png
