VivIngInf/kaffettino-rebrewed/Resources/Images/Buongiornissimi/Generic/st,small,507x507-pad,600x600,f8f8f8.jpg

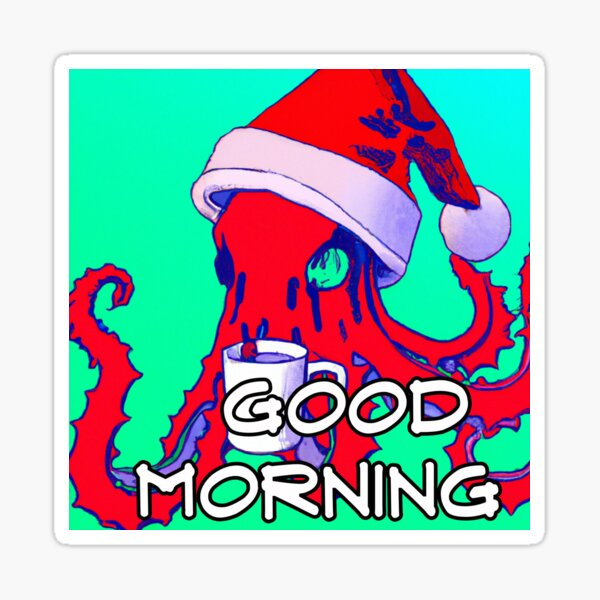
Resources/Images/Buongiornissimi/Generic/st,small,507x507-pad,600x600,f8f8f8.jpg
