VivIngInf/kaffettino-rebrewed/Resources/Images/Buongiornissimi/Monday/0365f407-9a3d-4577-a059-953b0fa6c58c.webp

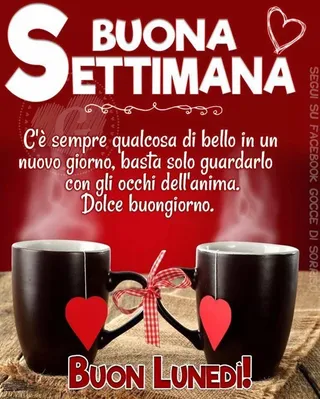
Resources/Images/Buongiornissimi/Monday/0365f407-9a3d-4577-a059-953b0fa6c58c.webp
