VivIngInf/kaffettino-rebrewed/Resources/Images/Buongiornissimi/Pasquetta/Auguri-Buona-Pasquetta-1.jpg

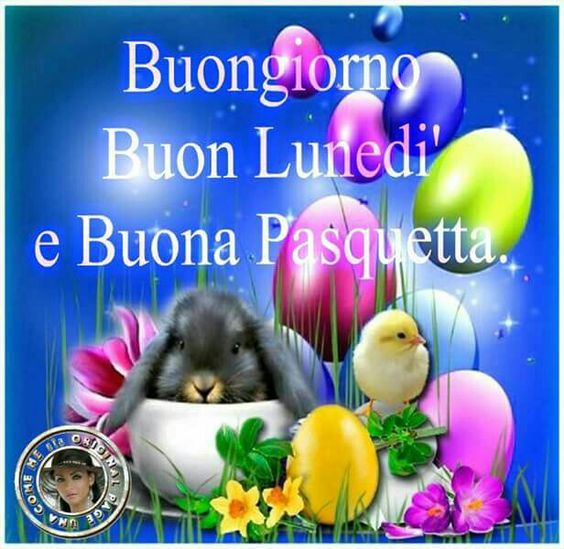
Resources/Images/Buongiornissimi/Pasquetta/Auguri-Buona-Pasquetta-1.jpg
