VivIngInf/kaffettino-rebrewed/Resources/Images/Buongiornissimi/Pasquetta/buona-pasquetta-bbq.jpg

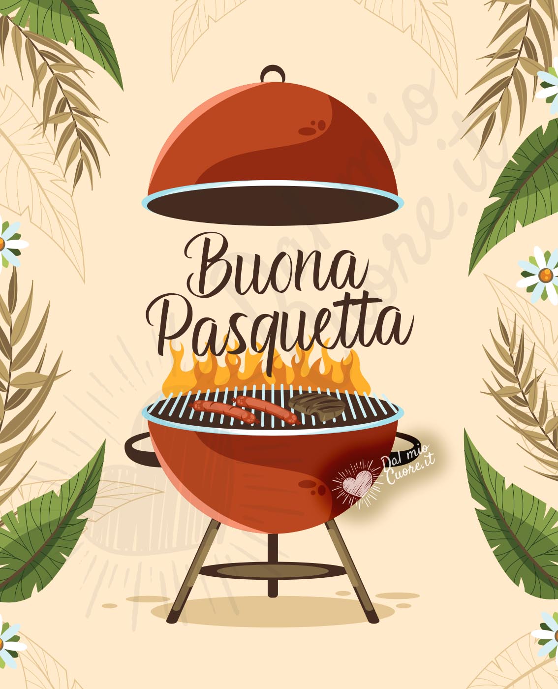
Resources/Images/Buongiornissimi/Pasquetta/buona-pasquetta-bbq.jpg
