VivIngInf/kaffettino-rebrewed/Resources/Images/Buongiornissimi/Pasquetta/buona-pasquetta-immagini.webp

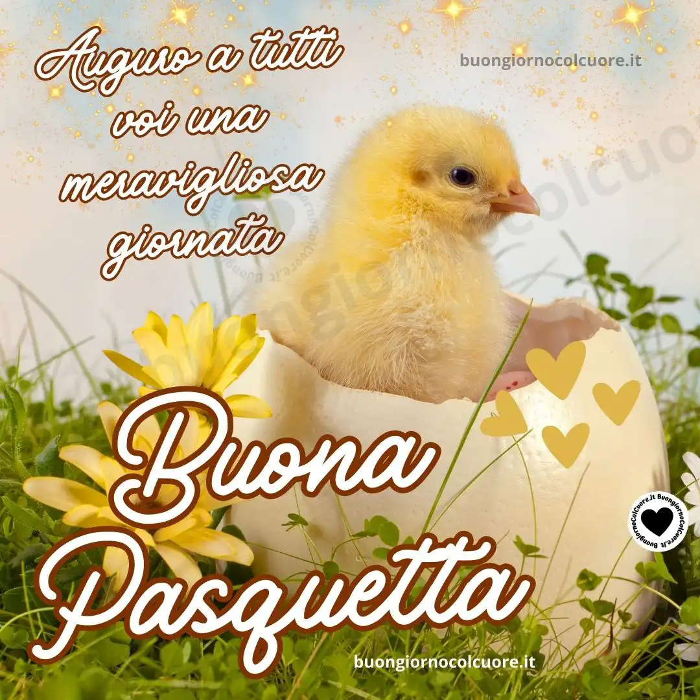
Resources/Images/Buongiornissimi/Pasquetta/buona-pasquetta-immagini.webp
