VivIngInf/kaffettino-rebrewed/Resources/Images/Buongiornissimi/Pasquetta/Buongiorno-buona-pasquetta-0.jpg

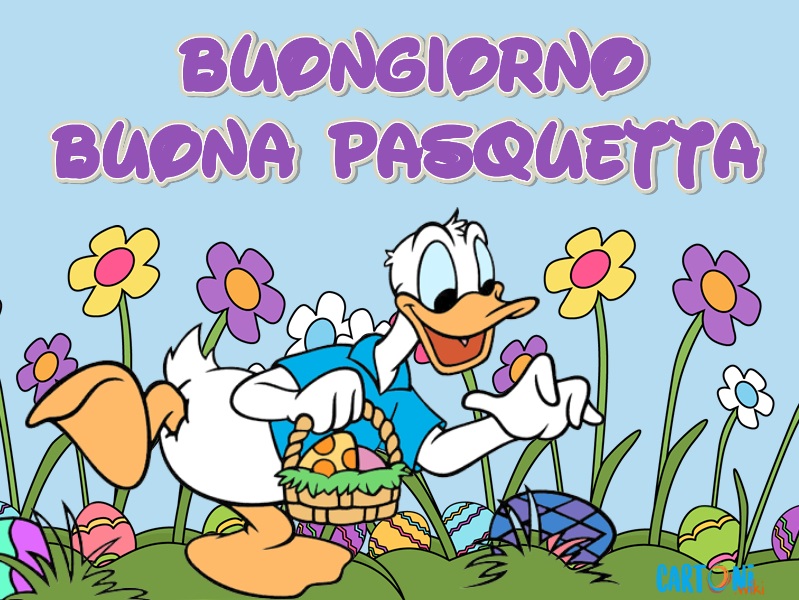
Resources/Images/Buongiornissimi/Pasquetta/Buongiorno-buona-pasquetta-0.jpg
