VivIngInf/kaffettino-rebrewed/Resources/Images/Buongiornissimi/Pasquetta/buongiorno-buona-pasquetta-vi-siete-pesati.jpg

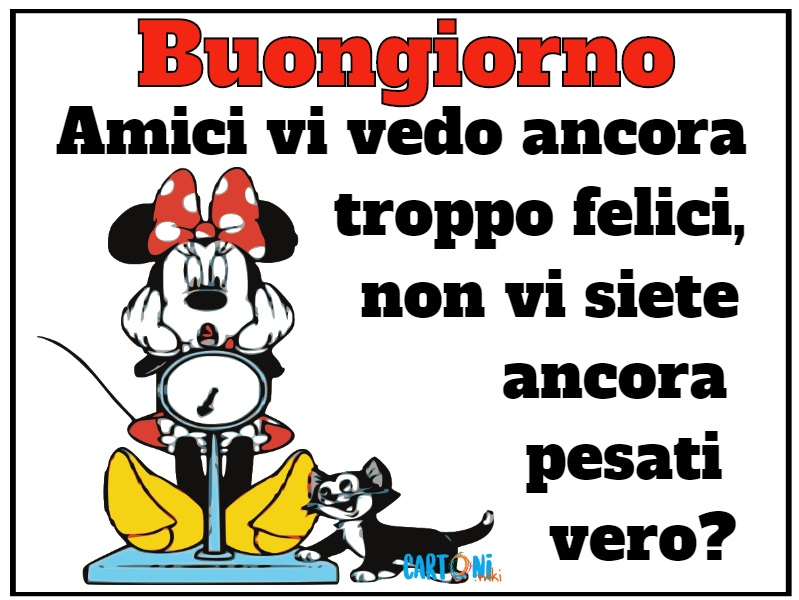
Resources/Images/Buongiornissimi/Pasquetta/buongiorno-buona-pasquetta-vi-siete-pesati.jpg
