VivIngInf/kaffettino-rebrewed/Resources/Images/Buongiornissimi/Pasquetta/buongiorno-è-pasquetta-2.jpg

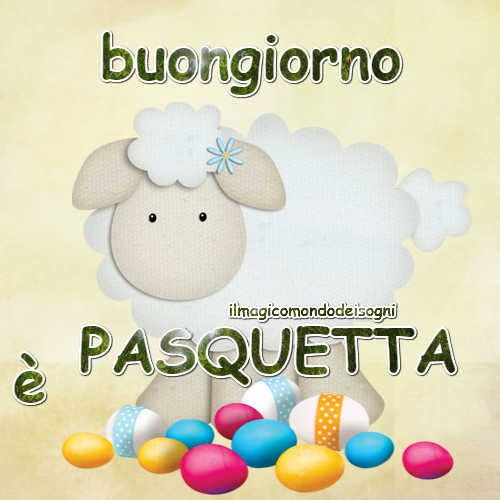
Resources/Images/Buongiornissimi/Pasquetta/buongiorno-è-pasquetta-2.jpg
