VivIngInf/kaffettino-rebrewed/Resources/Images/Buongiornissimi/Pasquetta/c0677435fa4549f961de9112c61cfee7.jpg

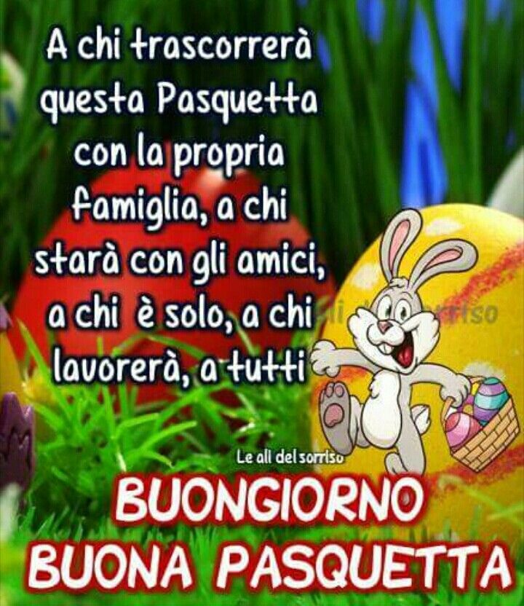
Resources/Images/Buongiornissimi/Pasquetta/c0677435fa4549f961de9112c61cfee7.jpg
