VivIngInf/kaffettino-rebrewed/Resources/Images/Buongiornissimi/Pasquetta/fb_img_1522734556513.jpg

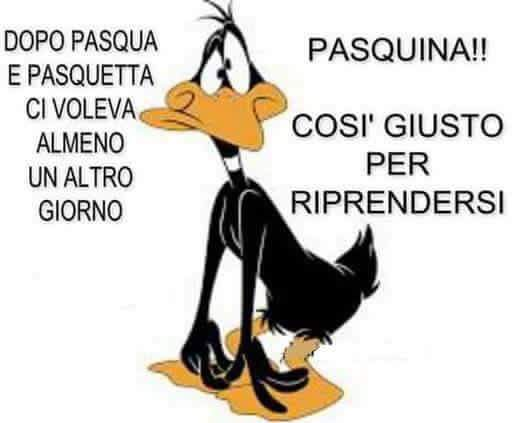
Resources/Images/Buongiornissimi/Pasquetta/fb_img_1522734556513.jpg
