VivIngInf/kaffettino-rebrewed/Resources/Images/Buongiornissimi/Pasquetta/IMG-20190421-WA0003.jpg

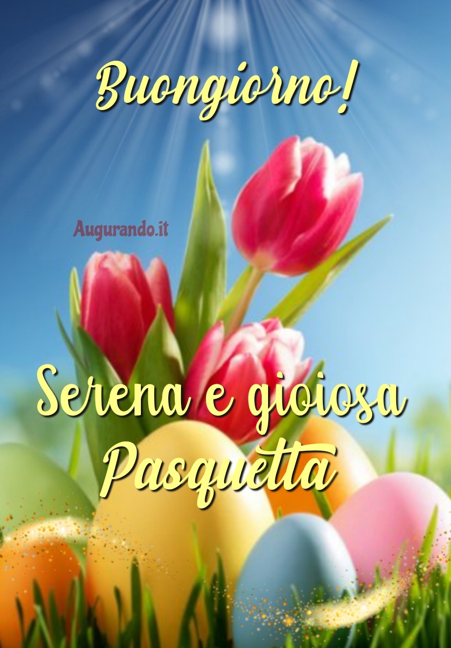
Resources/Images/Buongiornissimi/Pasquetta/IMG-20190421-WA0003.jpg
