VivIngInf/kaffettino-rebrewed/Resources/Images/Buongiornissimi/Pasquetta/immagine_04-07-09.01.18.jpg

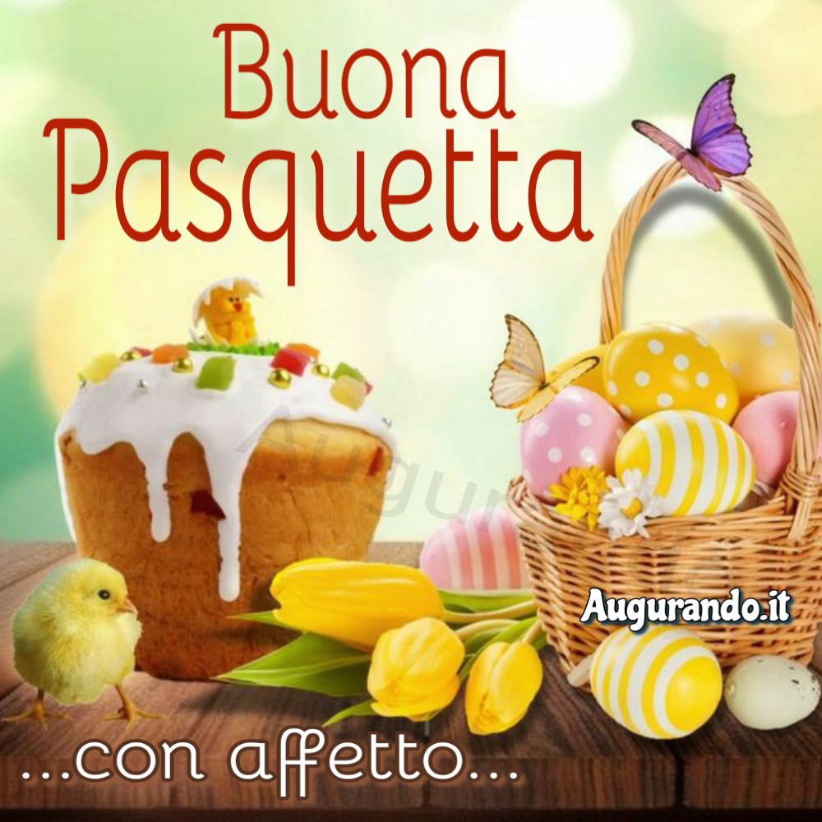
Resources/Images/Buongiornissimi/Pasquetta/immagine_04-07-09.01.18.jpg
