VivIngInf/kaffettino-rebrewed/Resources/Images/Buongiornissimi/Pasquetta/immagine_04-07-09.08.10.jpg

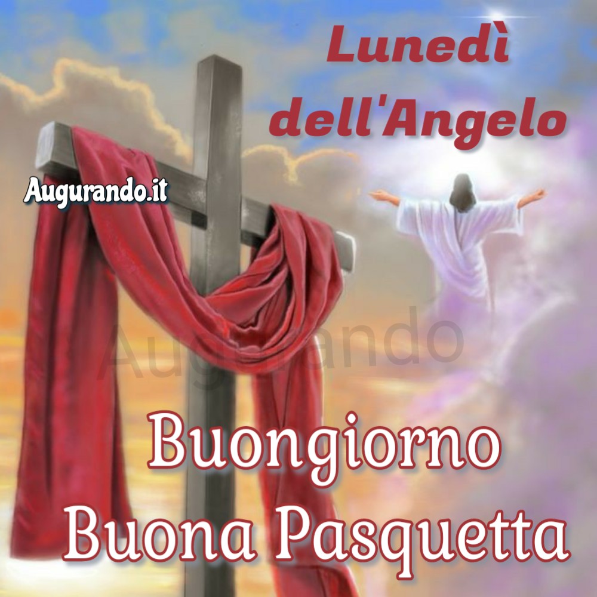
Resources/Images/Buongiornissimi/Pasquetta/immagine_04-07-09.08.10.jpg
