VivIngInf/kaffettino-rebrewed/Resources/Images/Buongiornissimi/Pasquetta/Immagini-buongiorno-buon-lunedi-di-pasquetta-nuove-foto-e-illustrazioni-2023-belle-e-gratis-per-WhatsApp-e-Facebook-1653.jpg

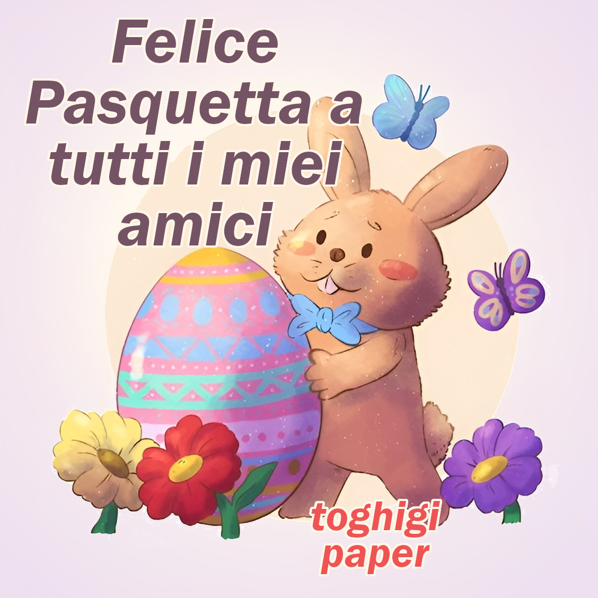
Resources/Images/Buongiornissimi/Pasquetta/Immagini-buongiorno-buon-lunedi-di-pasquetta-nuove-foto-e-illustrazioni-2023-belle-e-gratis-per-WhatsApp-e-Facebook-1653.jpg
