VivIngInf/kaffettino-rebrewed/Resources/Images/Buongiornissimi/Pasquetta/pasquetta_023.jpg

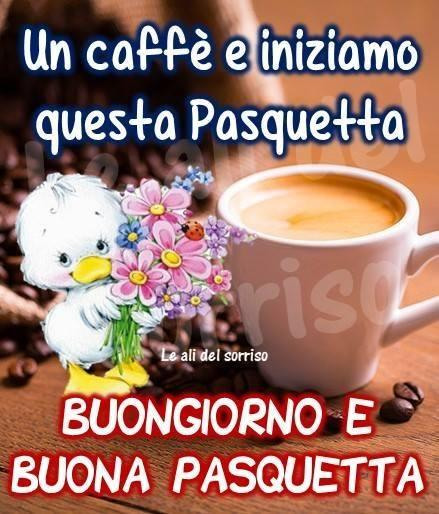
Resources/Images/Buongiornissimi/Pasquetta/pasquetta_023.jpg
