VivIngInf/kaffettino-rebrewed/Resources/Images/Buongiornissimi/Santa Lucia/0b765209eae464ec8e85c1e6ed095991.jpg

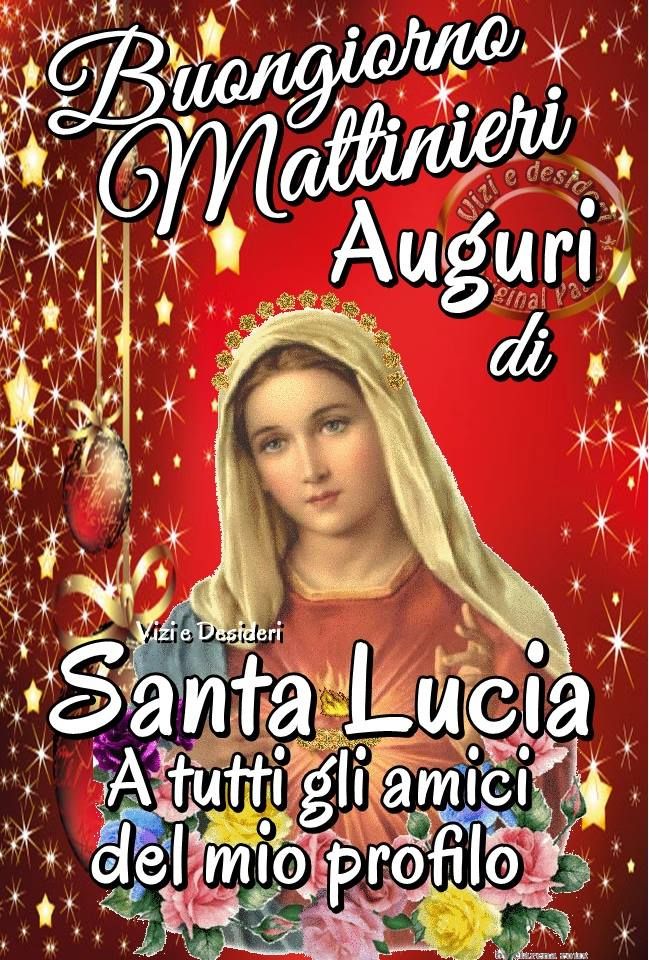
Resources/Images/Buongiornissimi/Santa Lucia/0b765209eae464ec8e85c1e6ed095991.jpg
