VivIngInf/kaffettino-rebrewed/Resources/Images/Buongiornissimi/Santa Lucia/04d1c7e49831098e6a21c706628971ab.jpg

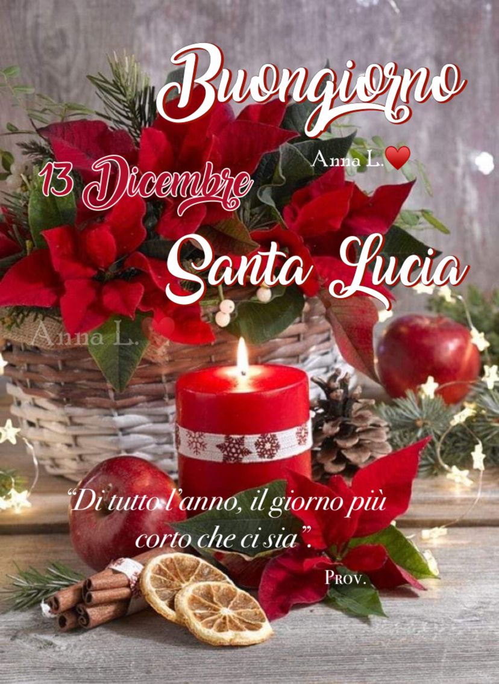
Resources/Images/Buongiornissimi/Santa Lucia/04d1c7e49831098e6a21c706628971ab.jpg
