VivIngInf/kaffettino-rebrewed/Resources/Images/Buongiornissimi/Santa Lucia/festa-di-santa-lucia_004.jpg

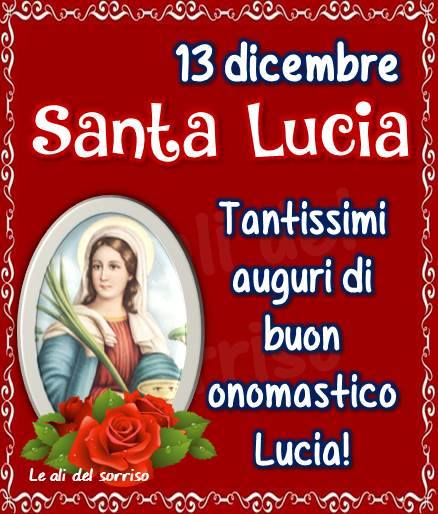
Resources/Images/Buongiornissimi/Santa Lucia/festa-di-santa-lucia_004.jpg
