VivIngInf/kaffettino-rebrewed/Resources/Images/Buongiornissimi/Santa Lucia/Immagini-Santa-Lucia-11-960x960.jpg

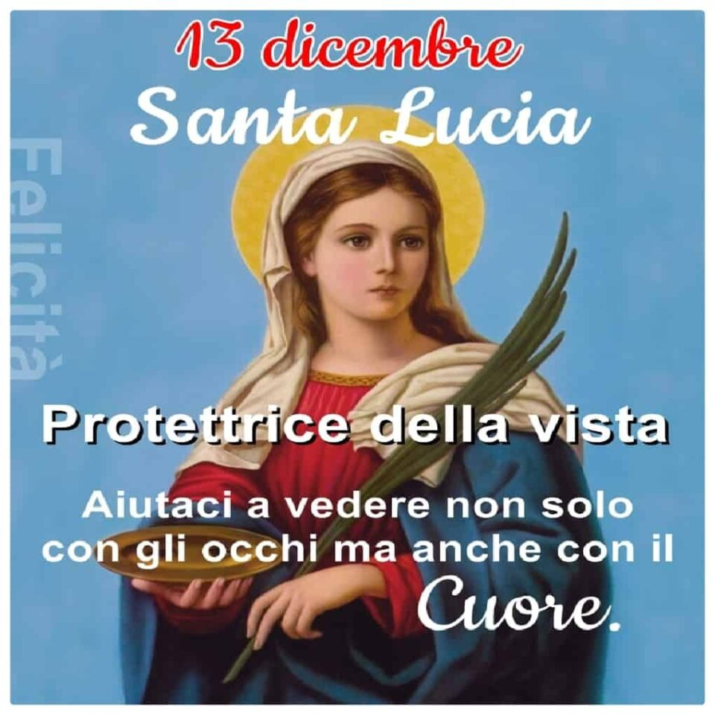
Resources/Images/Buongiornissimi/Santa Lucia/Immagini-Santa-Lucia-11-960x960.jpg
