VivIngInf/kaffettino-rebrewed/Resources/Images/Buongiornissimi/Santa Lucia/SANTA LUCIA Adèle Söderberg copia.jpg

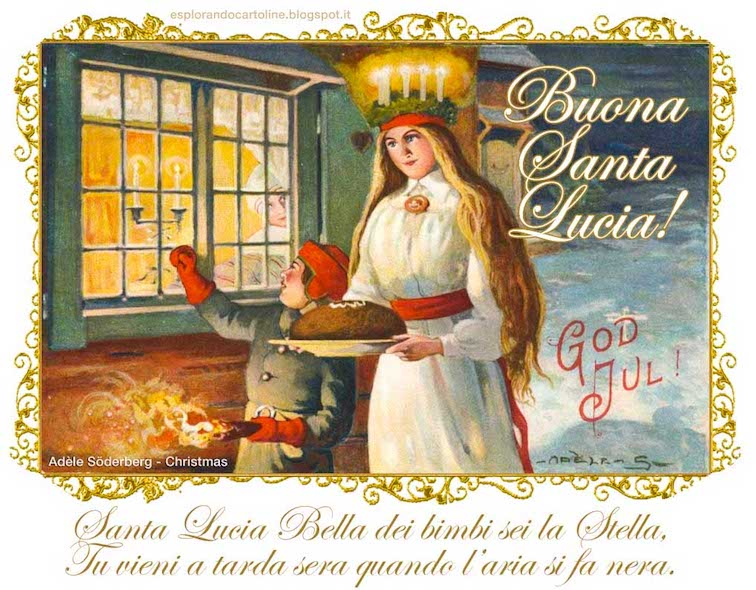
Resources/Images/Buongiornissimi/Santa Lucia/SANTA LUCIA Adèle Söderberg copia.jpg
