VivIngInf/kaffettino-rebrewed/Resources/Images/Buongiornissimi/Santa Lucia/Santa-Lucia-immagini-buon-onomastico-13-Dicembre-1850.jpg

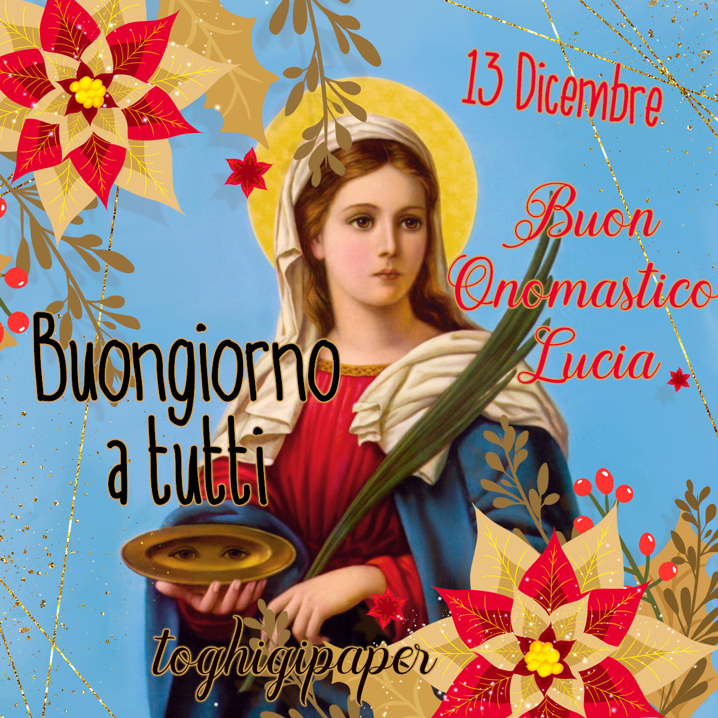
Resources/Images/Buongiornissimi/Santa Lucia/Santa-Lucia-immagini-buon-onomastico-13-Dicembre-1850.jpg
