VivIngInf/kaffettino-rebrewed/Resources/Images/Buongiornissimi/Santa Lucia/whatsapp-image-2020-12-13-at-09-24-27.jpeg

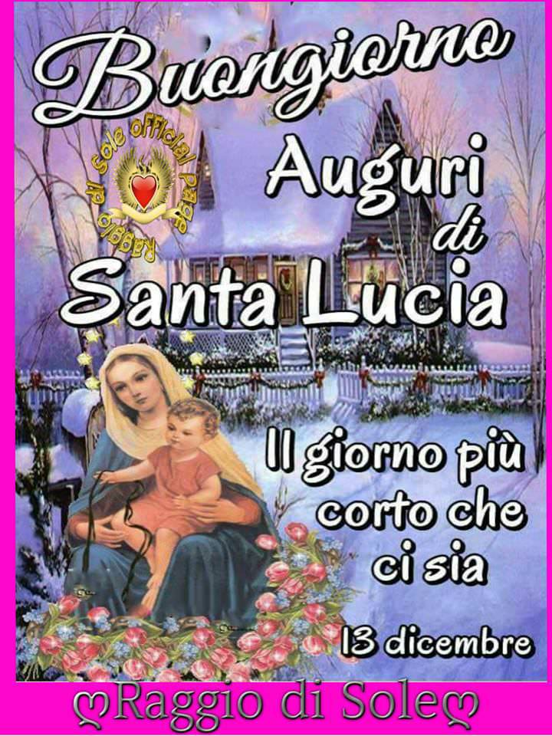
Resources/Images/Buongiornissimi/Santa Lucia/whatsapp-image-2020-12-13-at-09-24-27.jpeg
