VivIngInf/kaffettino-rebrewed/Resources/Images/Buongiornissimi/Saturday/70a5dd85-ea8a-4b44-bcf1-9fd2db836b1e.webp

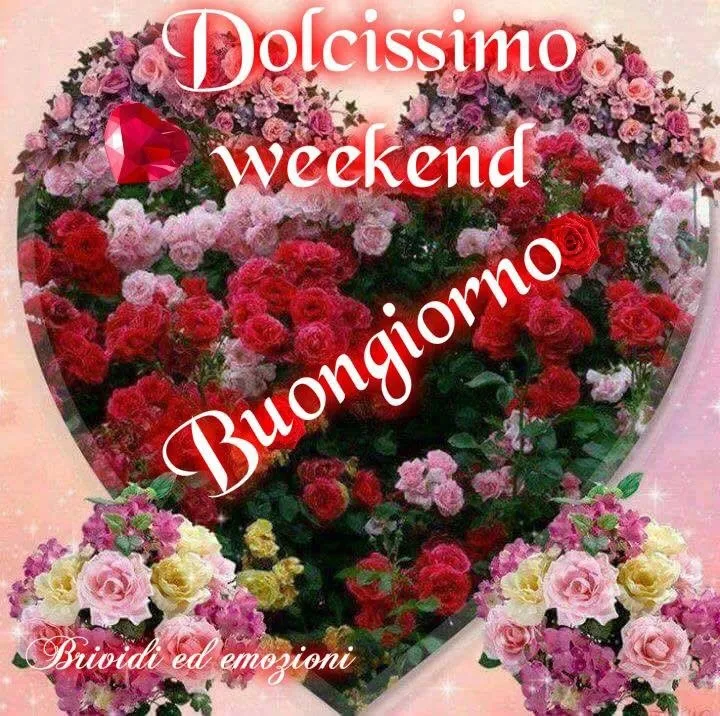
Resources/Images/Buongiornissimi/Saturday/70a5dd85-ea8a-4b44-bcf1-9fd2db836b1e.webp
