VivIngInf/kaffettino-rebrewed/Resources/Images/Buongiornissimi/Saturday/770e54b7-4708-4f03-b16f-16b8a369686d.webp

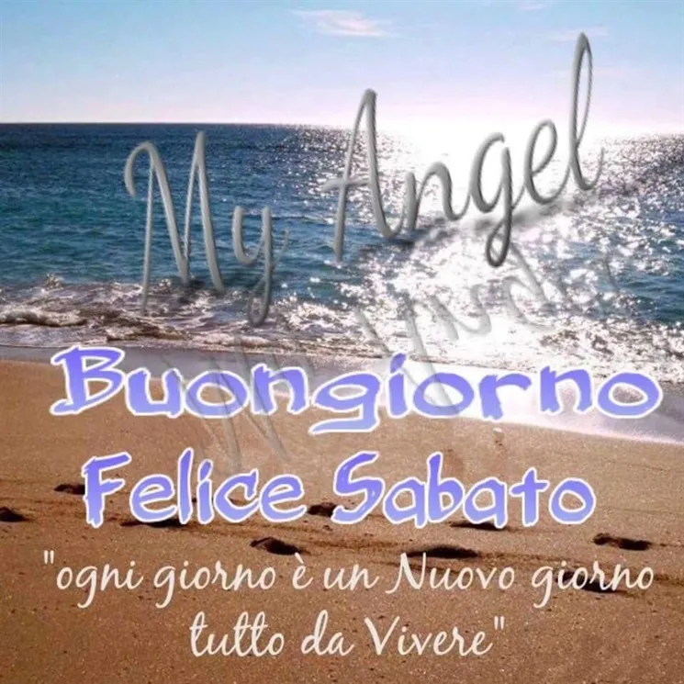
Resources/Images/Buongiornissimi/Saturday/770e54b7-4708-4f03-b16f-16b8a369686d.webp
