VivIngInf/kaffettino-rebrewed/Resources/Images/Buongiornissimi/Saturday/933b1cc6-b47f-458a-b04b-2c21dcd0d410.webp

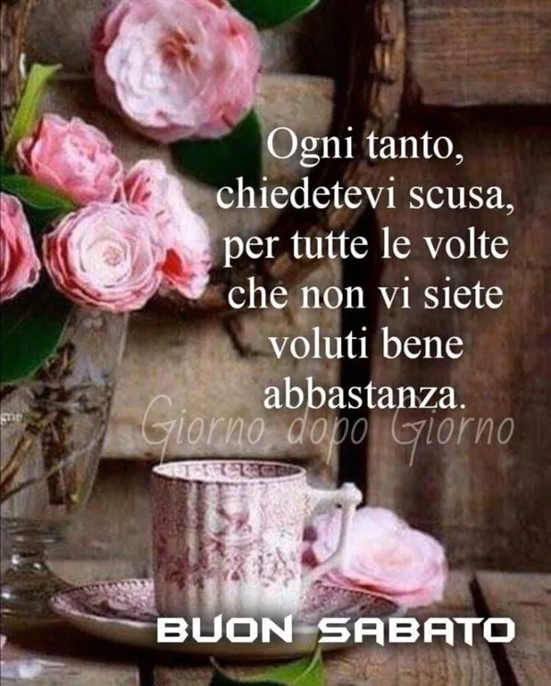
Resources/Images/Buongiornissimi/Saturday/933b1cc6-b47f-458a-b04b-2c21dcd0d410.webp
