VivIngInf/kaffettino-rebrewed/Resources/Images/Buongiornissimi/Saturday/7910f4a0-ed06-47e2-8225-b305b14da9d7.webp

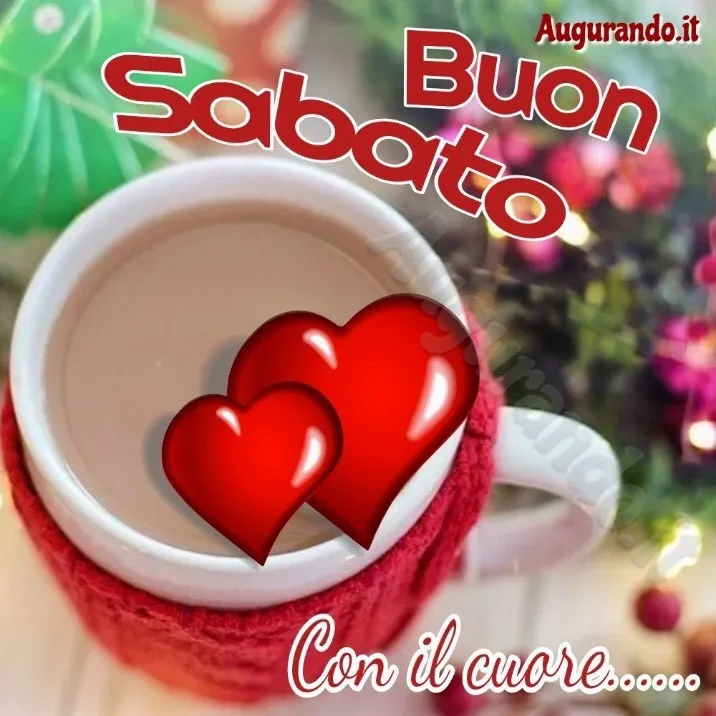
Resources/Images/Buongiornissimi/Saturday/7910f4a0-ed06-47e2-8225-b305b14da9d7.webp
