VivIngInf/kaffettino-rebrewed/Resources/Images/Buongiornissimi/Sunday/0bb54a3e-ab8d-4a5f-bb08-aea1f1b38e7e_010.webp

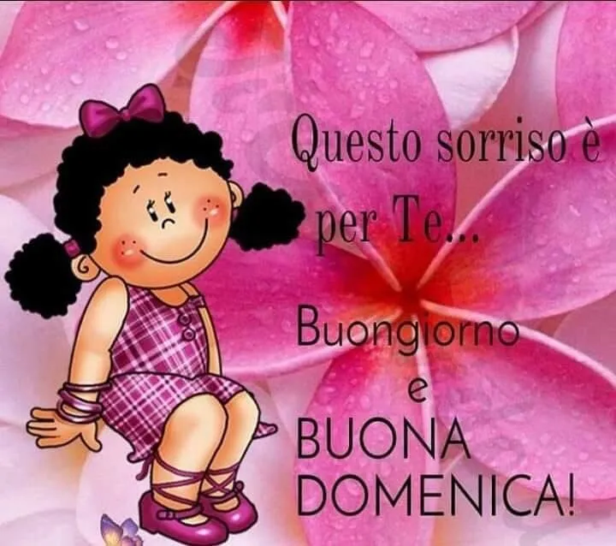
Resources/Images/Buongiornissimi/Sunday/0bb54a3e-ab8d-4a5f-bb08-aea1f1b38e7e_010.webp
