VivIngInf/kaffettino-rebrewed/Resources/Images/Buongiornissimi/Sunday/f4c4e380-99a4-4442-97f7-6592fcd643a6.webp

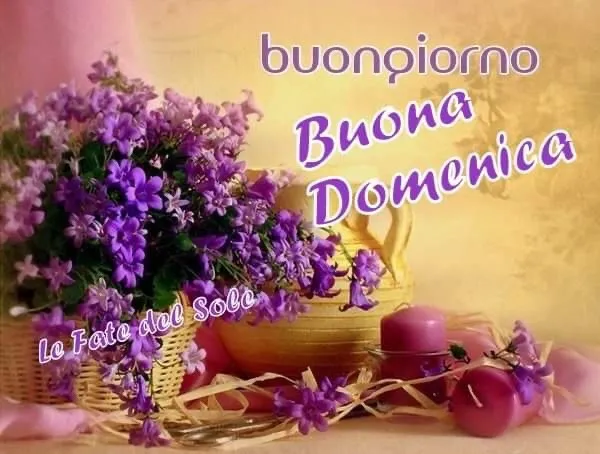
Resources/Images/Buongiornissimi/Sunday/f4c4e380-99a4-4442-97f7-6592fcd643a6.webp
