VivIngInf/kaffettino-rebrewed/Resources/Images/Buongiornissimi/Thursday/5d3f99b7-e492-40f8-a615-7aecf7b4134f.webp

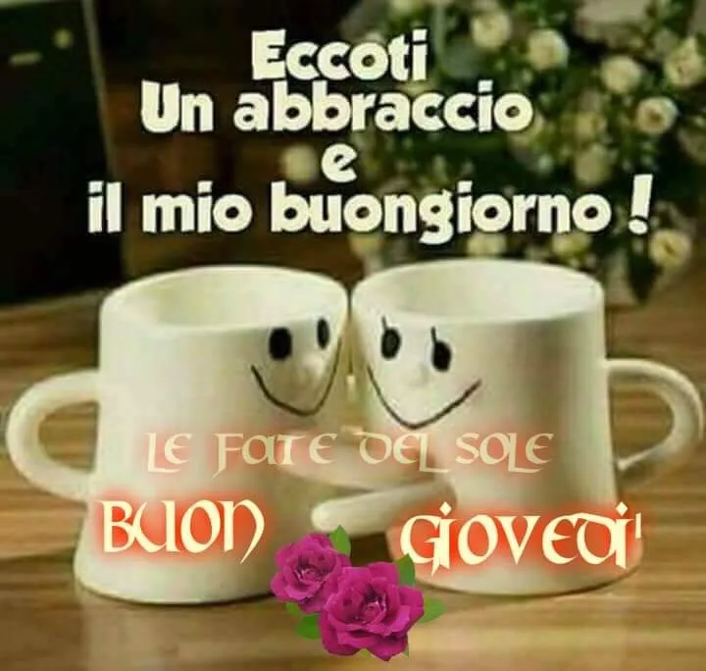
Resources/Images/Buongiornissimi/Thursday/5d3f99b7-e492-40f8-a615-7aecf7b4134f.webp
