VivIngInf/kaffettino-rebrewed/Resources/Images/Buongiornissimi/Thursday/9e50eae5-2db8-4561-a0e2-ca1e008ff99c.webp

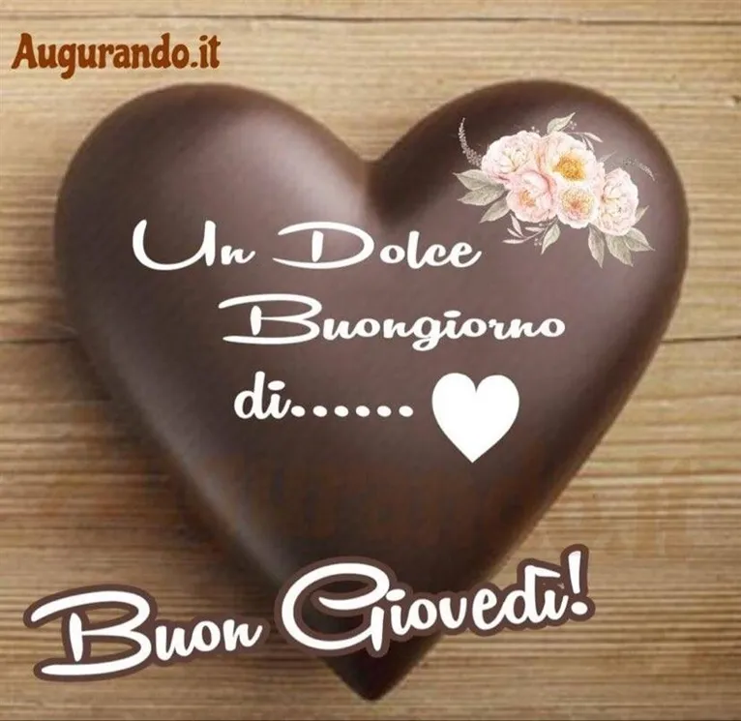
Resources/Images/Buongiornissimi/Thursday/9e50eae5-2db8-4561-a0e2-ca1e008ff99c.webp
