VivIngInf/kaffettino-rebrewed/Resources/Images/Buongiornissimi/Tuesday/b057d2a9-5b58-470f-a73e-bced1b9841d7.webp

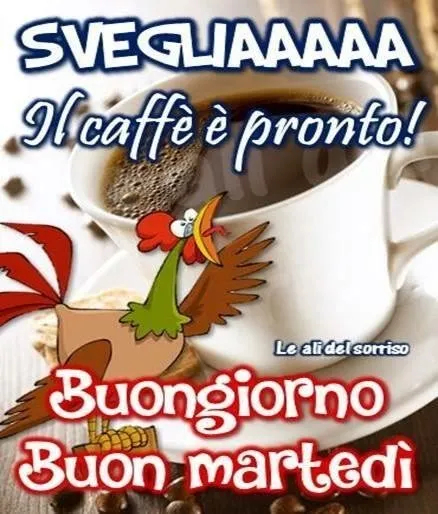
Resources/Images/Buongiornissimi/Tuesday/b057d2a9-5b58-470f-a73e-bced1b9841d7.webp
