VivIngInf/kaffettino-rebrewed/Resources/Images/Buongiornissimi/Tuesday/cb51c09a-1ffa-4f30-bb67-cb6aab5aebb2.webp

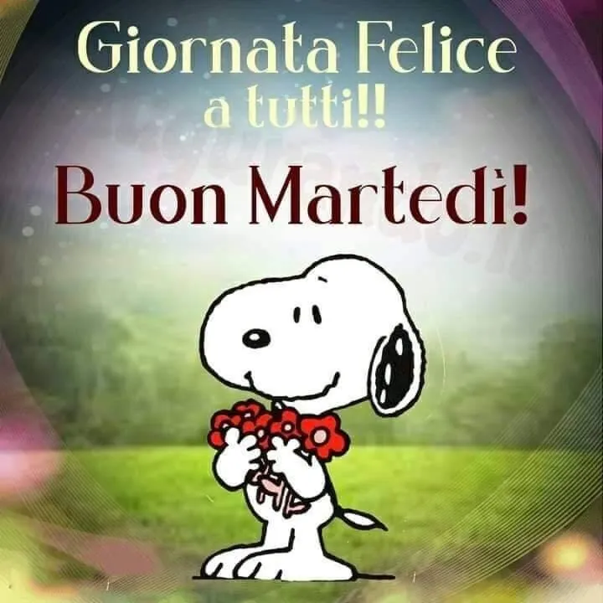
Resources/Images/Buongiornissimi/Tuesday/cb51c09a-1ffa-4f30-bb67-cb6aab5aebb2.webp
