VivIngInf/kaffettino-rebrewed/Resources/Images/Buongiornissimi/Wednesday/6dd8014ffa339842632e0494fba622a3.jpg

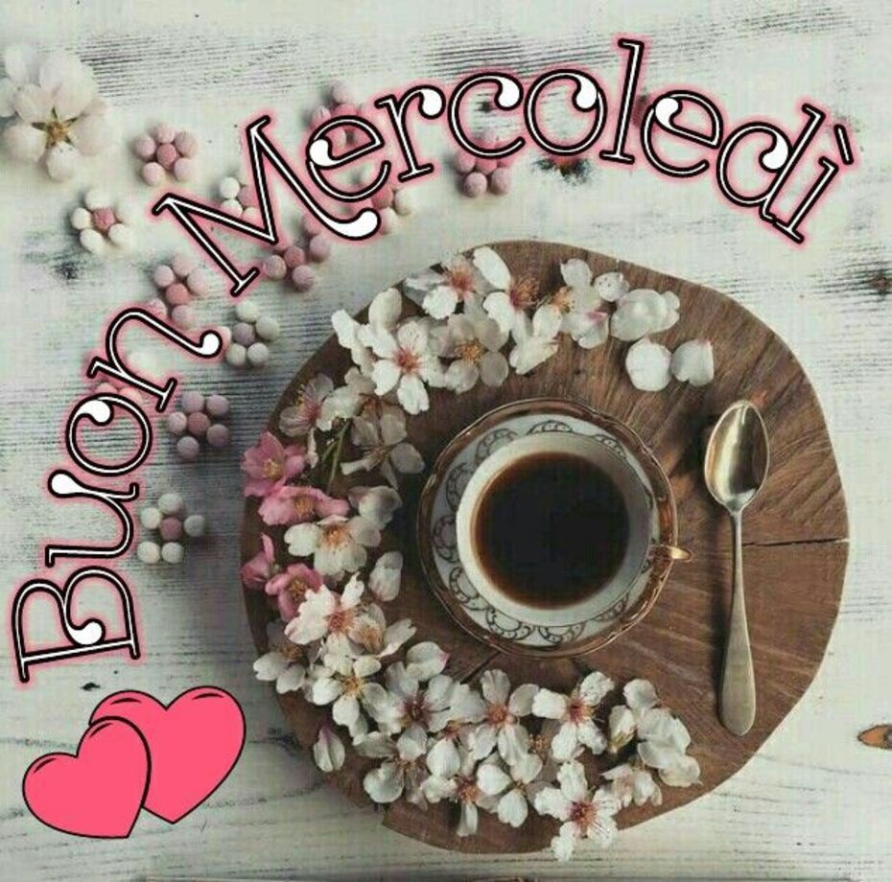
Resources/Images/Buongiornissimi/Wednesday/6dd8014ffa339842632e0494fba622a3.jpg
