VivIngInf/kaffettino-rebrewed/Resources/Images/Buongiornissimi/Wednesday/86e811a80887bb181a61200da7bd7031.jpg

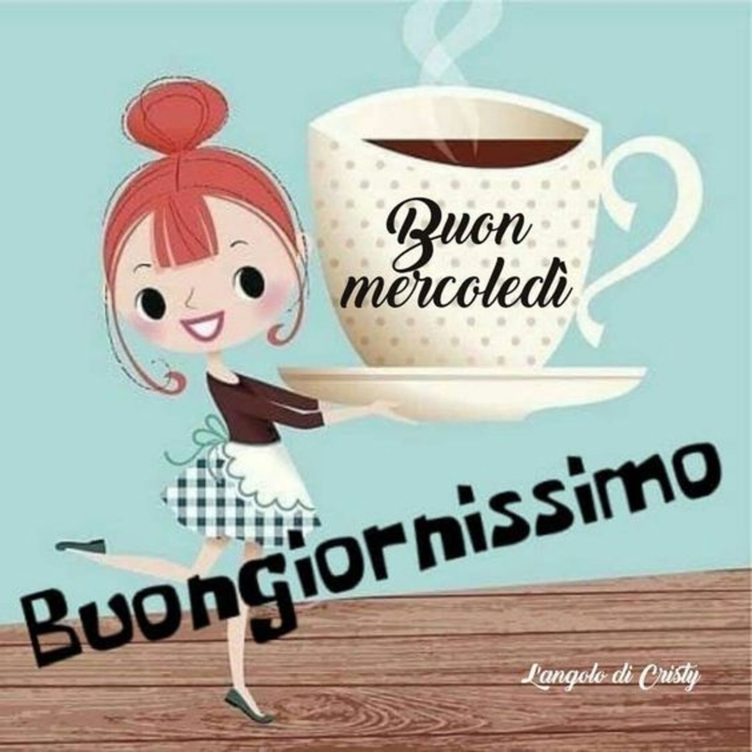
Resources/Images/Buongiornissimi/Wednesday/86e811a80887bb181a61200da7bd7031.jpg
