VivIngInf/kaffettino-rebrewed/Resources/Images/Buongiornissimi/Wednesday/buon-mercoledì-amici-7.jpg

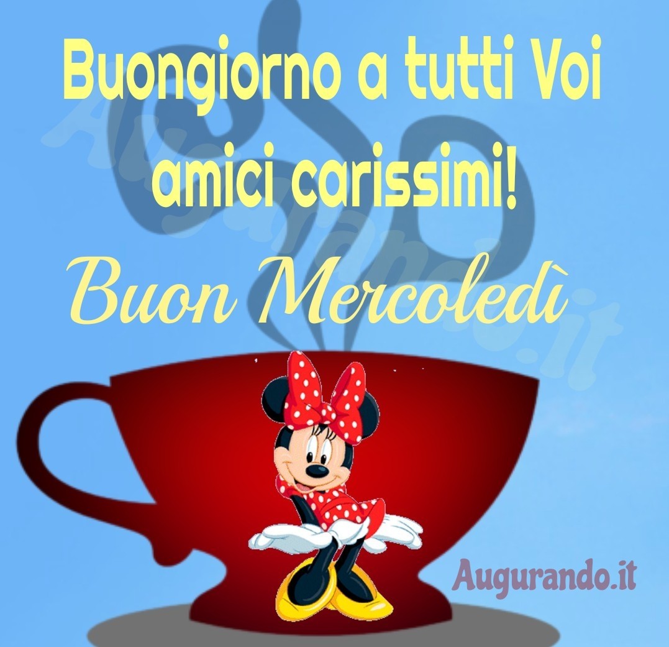
Resources/Images/Buongiornissimi/Wednesday/buon-mercoledì-amici-7.jpg
