VivIngInf/kaffettino-rebrewed/Resources/Images/Buongiornissimi/Wednesday/buon-mercoledì-amici-24.jpg

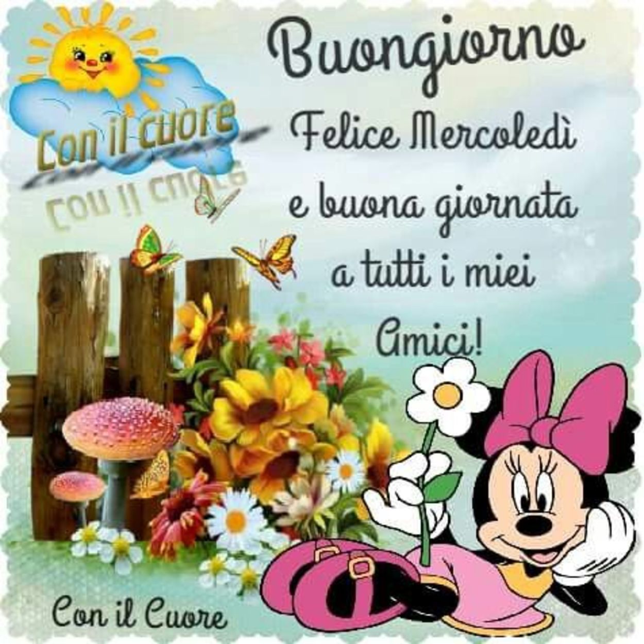
Resources/Images/Buongiornissimi/Wednesday/buon-mercoledì-amici-24.jpg
