VivIngInf/kaffettino-rebrewed/Resources/Images/Buongiornissimi/Wednesday/Buon-mercoledì-con-affetto-e-simpatia.jpg

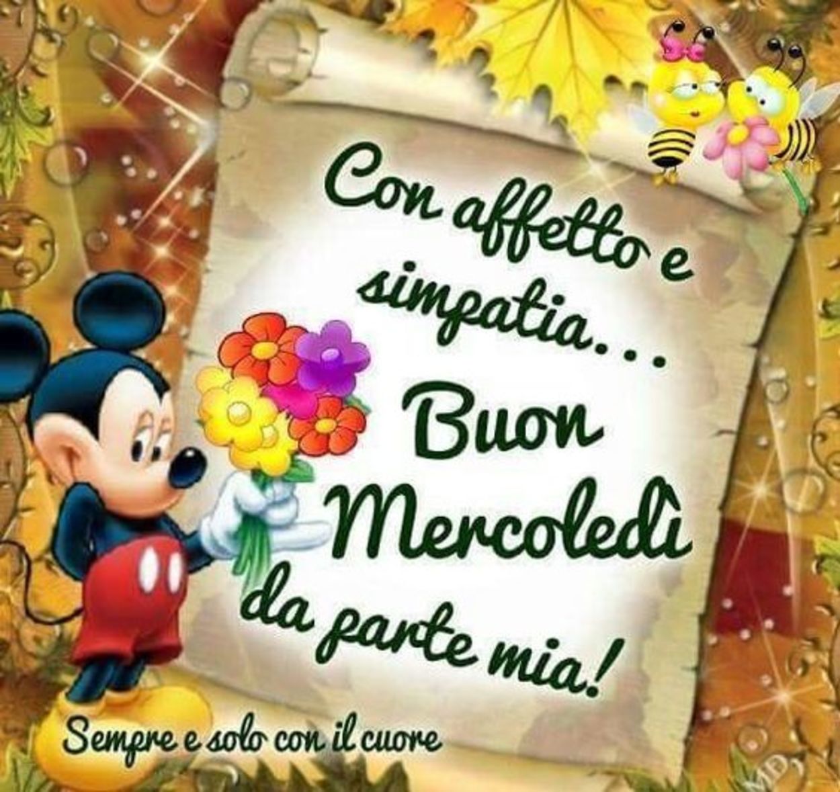
Resources/Images/Buongiornissimi/Wednesday/Buon-mercoledì-con-affetto-e-simpatia.jpg
