VivIngInf/kaffettino-rebrewed/Resources/Images/Buongiornissimi/Wednesday/Buongiorno-mercoledi-9-600x330.webp

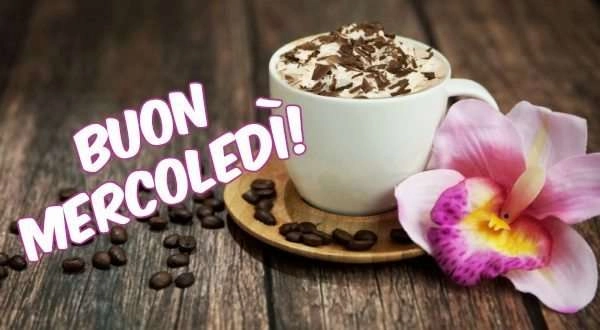
Resources/Images/Buongiornissimi/Wednesday/Buongiorno-mercoledi-9-600x330.webp
