VivIngInf/kaffettino-rebrewed/Resources/Images/Buongiornissimi/Wednesday/Foto-Buon-Mercoledì-59.jpg

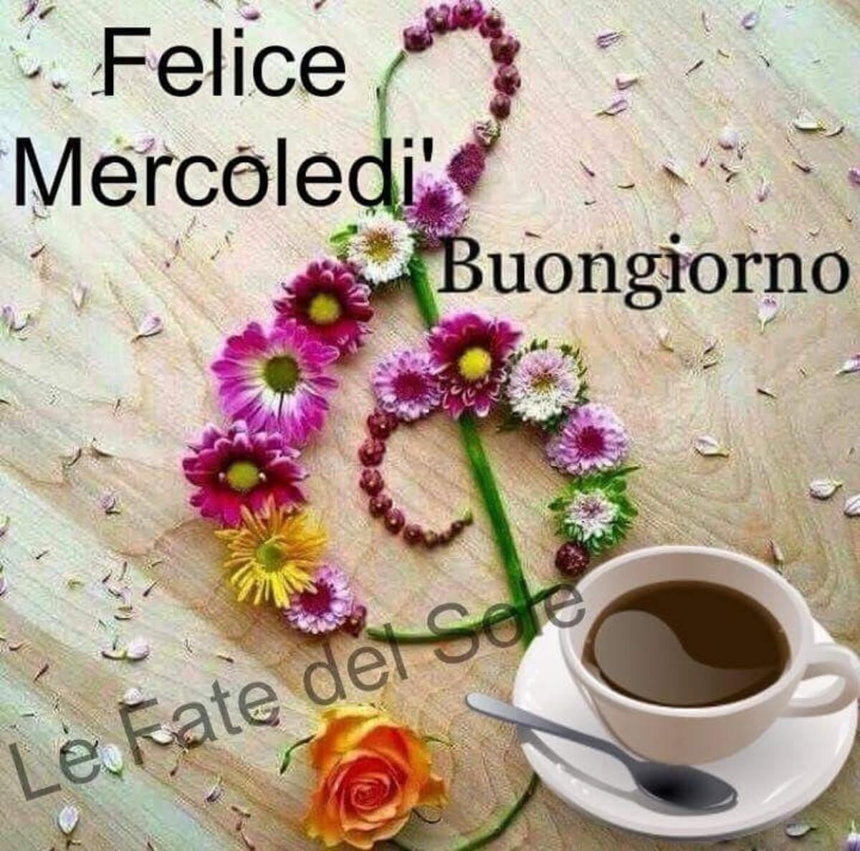
Resources/Images/Buongiornissimi/Wednesday/Foto-Buon-Mercoledì-59.jpg
