VivIngInf/kaffettino-rebrewed/Resources/Images/Buongiornissimi/Wednesday/Frasi-bellissime-x-Buon-Mercoledì-82.jpg

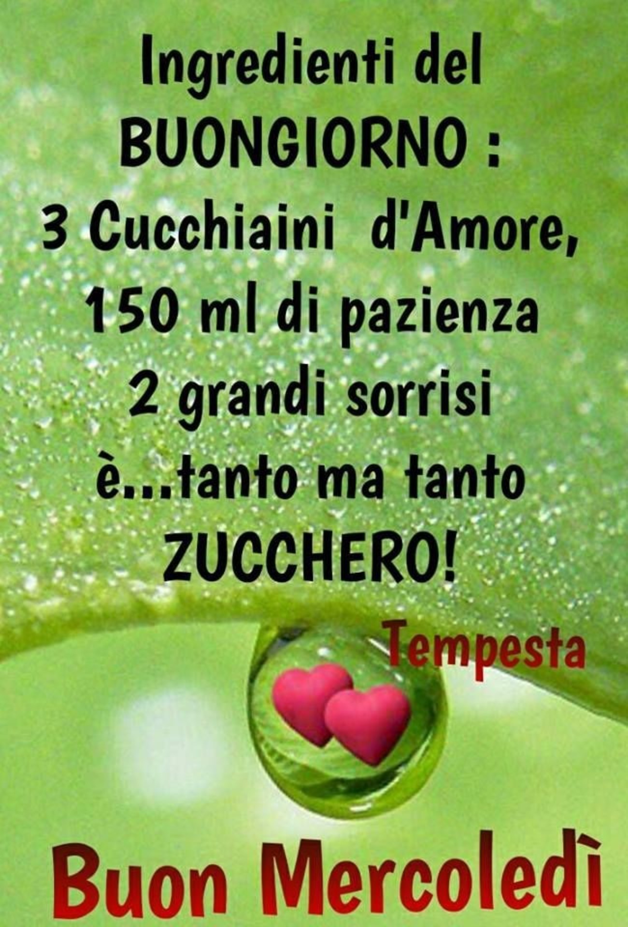
Resources/Images/Buongiornissimi/Wednesday/Frasi-bellissime-x-Buon-Mercoledì-82.jpg
