VivIngInf/kaffettino-rebrewed/Resources/Images/Buongiornissimi/Wednesday/mercoledi_054.jpg

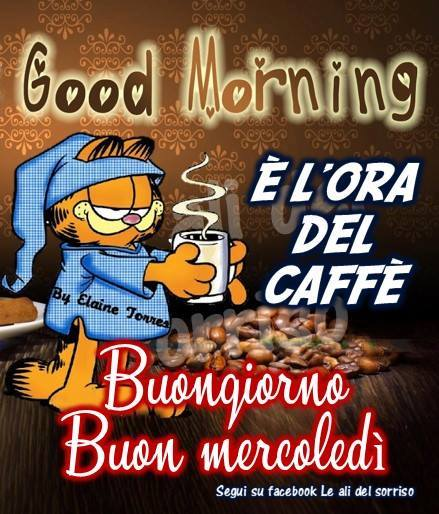
Resources/Images/Buongiornissimi/Wednesday/mercoledi_054.jpg
